CXD8/CXD-ROUTER/Sch/CXD-ROUTER-1.kicad_sch

## KiCad design Sch/CXD-ROUTER-1.kicad_sch (2026-08-12)

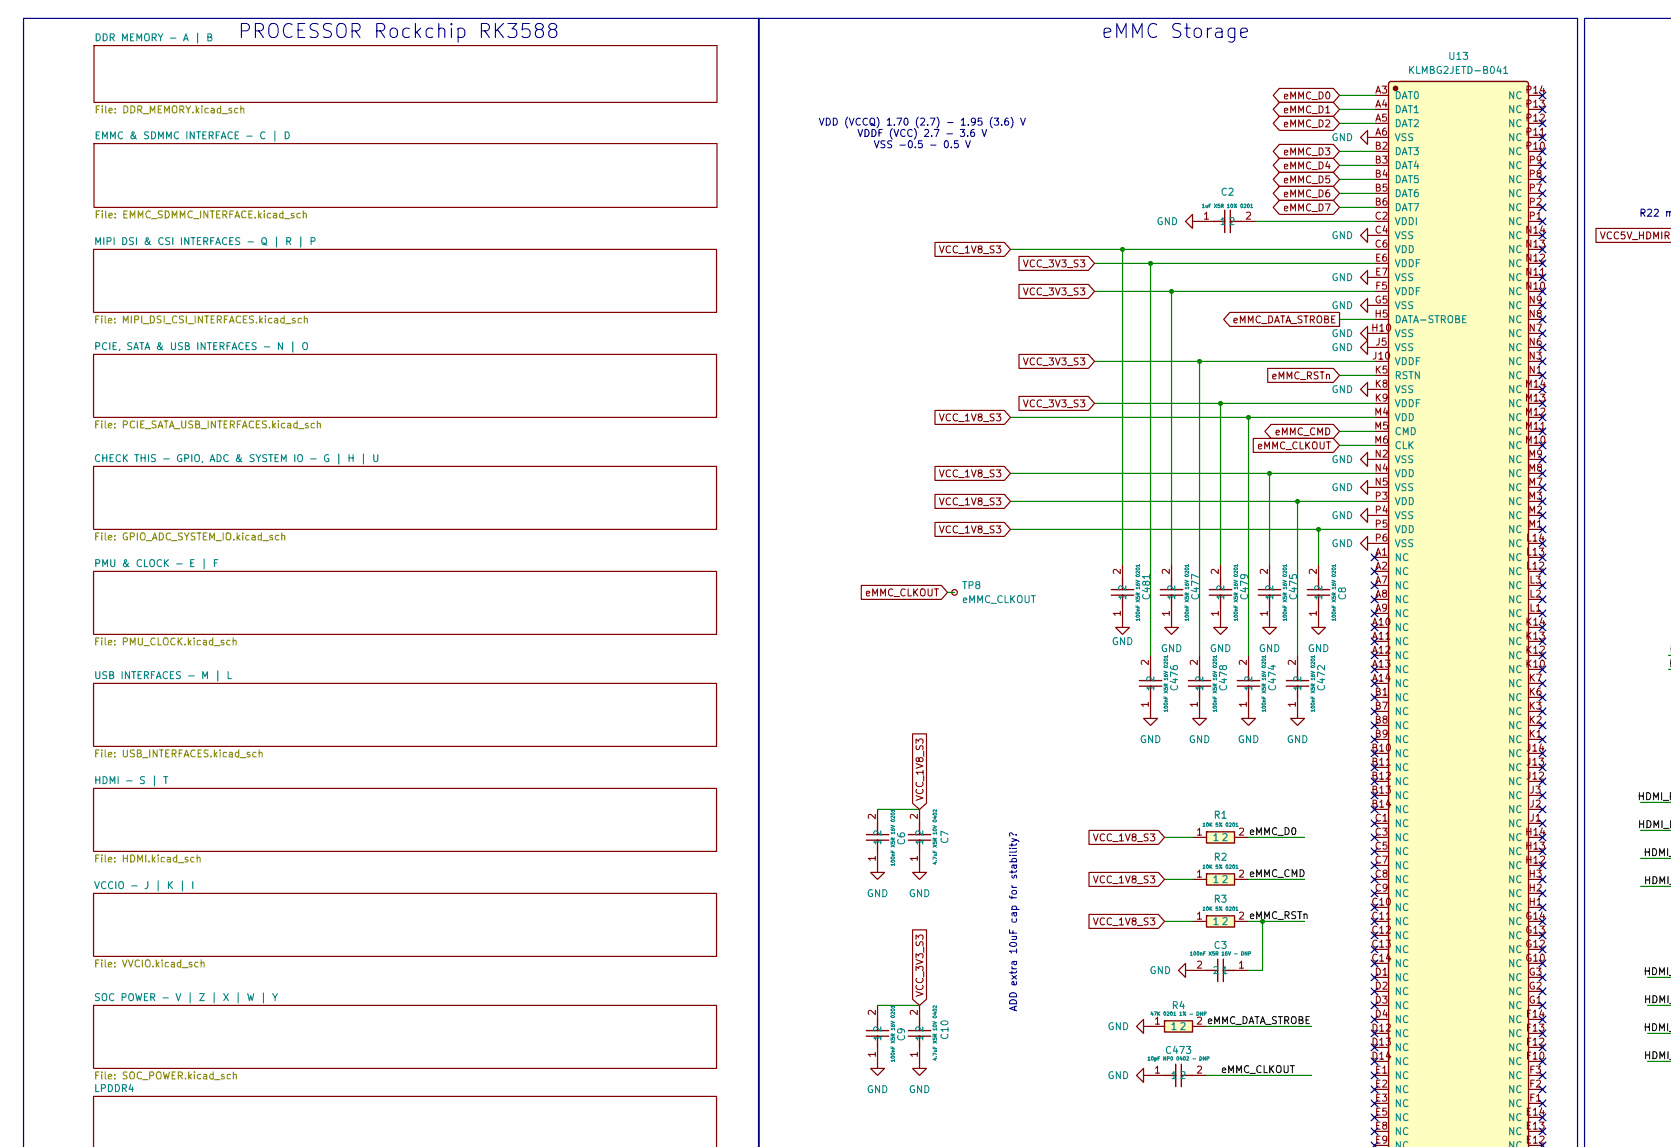
[picture p30: schematic CXD-ROUTER-1.kicad_sch, part in row 1, column 1]

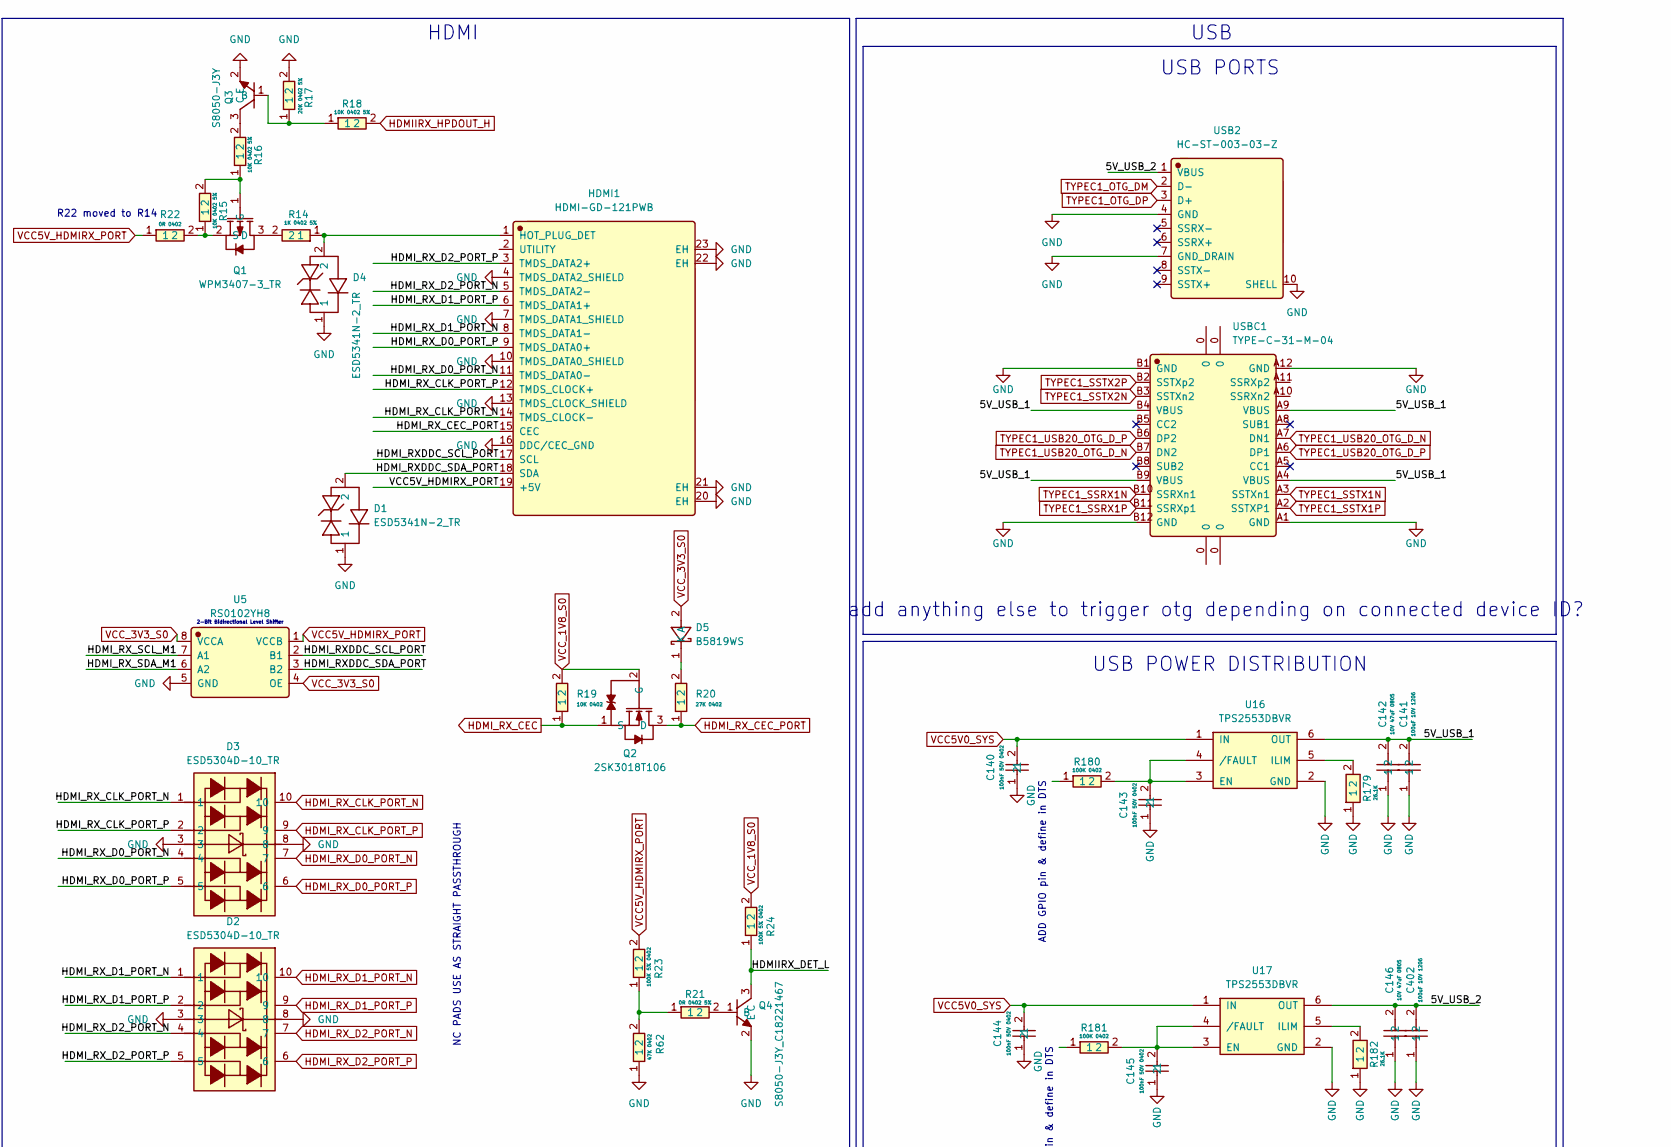
[picture p31: schematic CXD-ROUTER-1.kicad_sch, part in row 1, column 2]

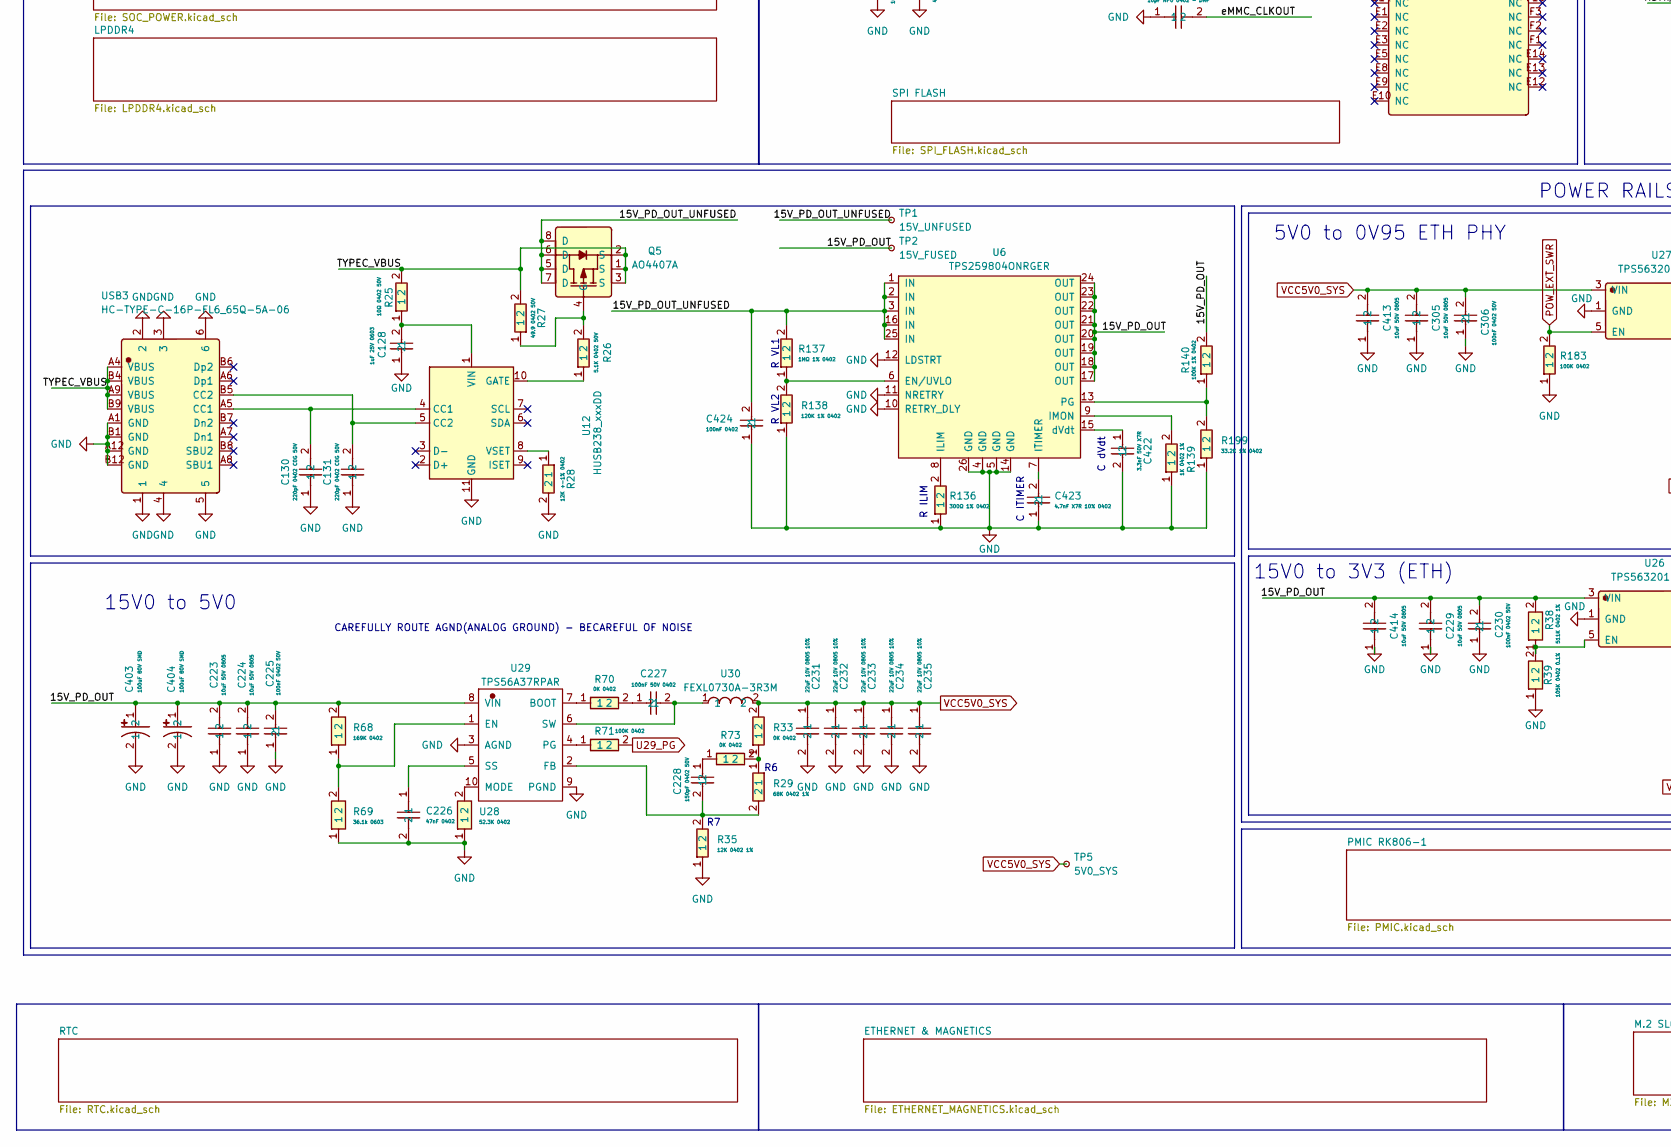
[picture p32: schematic CXD-ROUTER-1.kicad_sch, part in row 2, column 1]

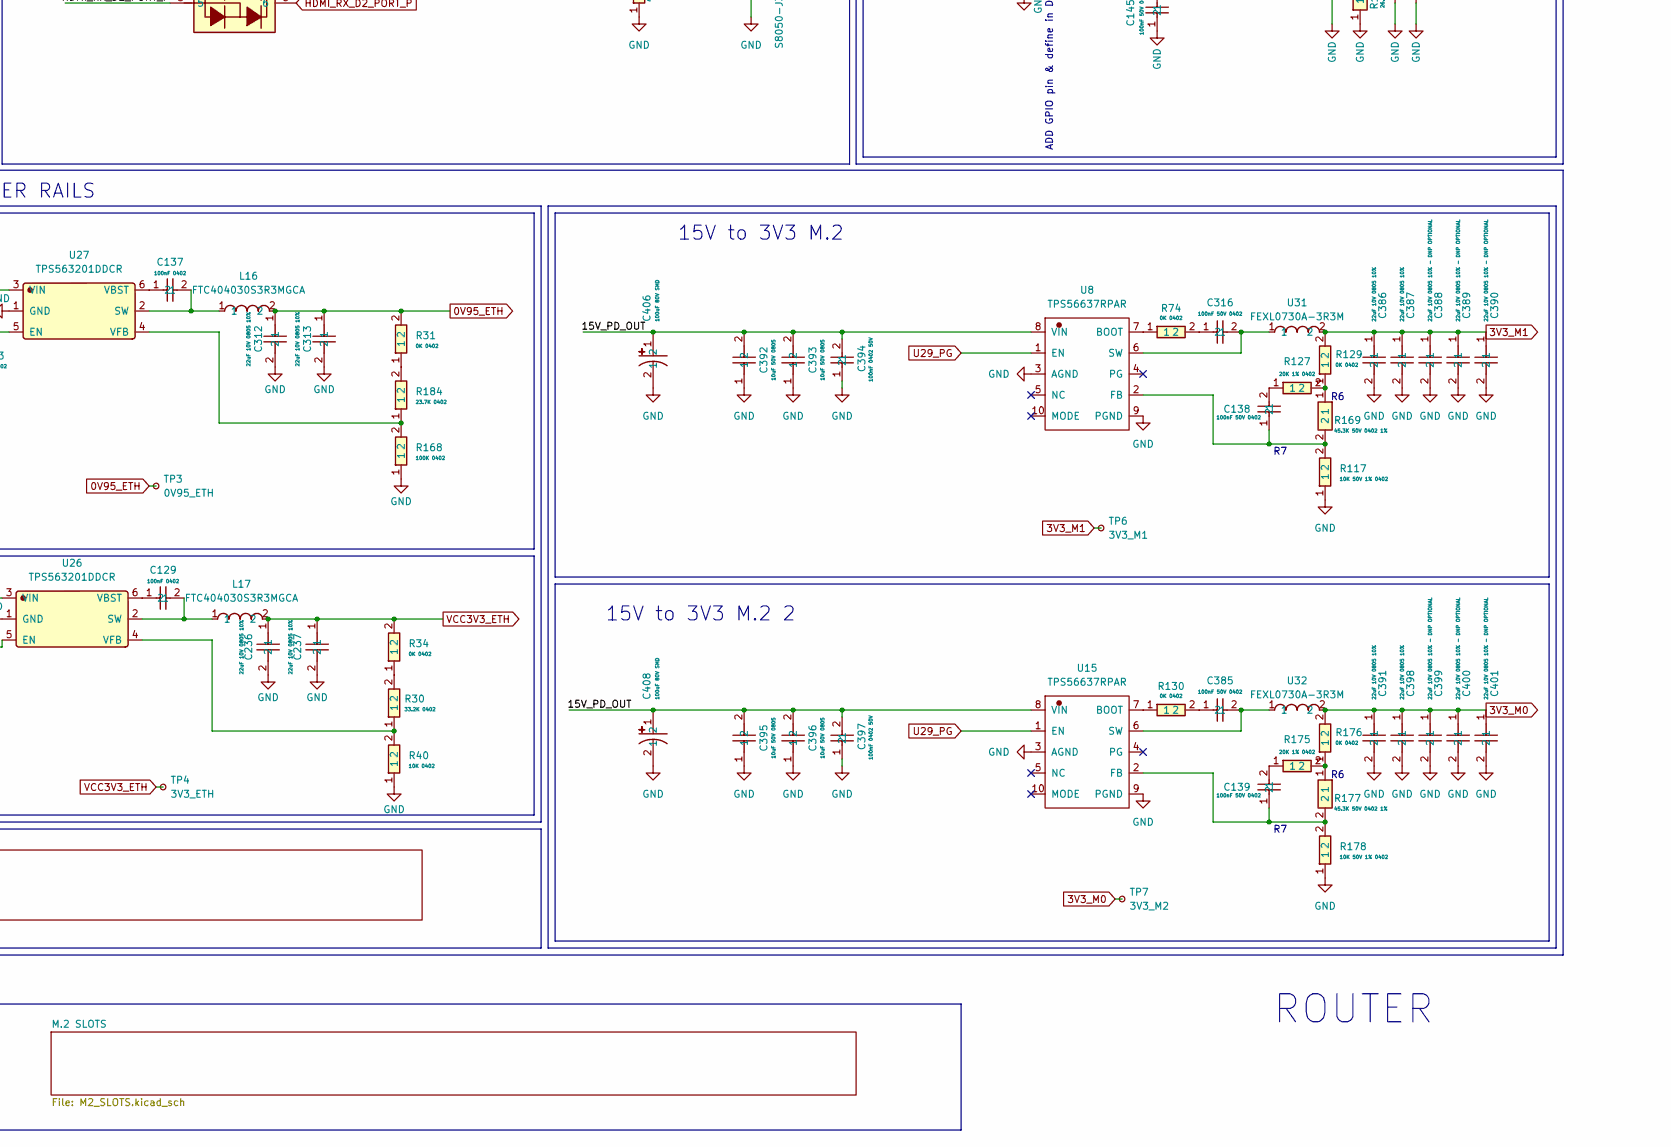
[picture p33: schematic CXD-ROUTER-1.kicad_sch, part in row 2, column 2]

Parts:
C2: 1uF X5R 10% 0201; RC0201FR-0749R9L; Manufacturer Part CC0201KRX5R5BB105; LCSC C541330
C3: 100nF X5R 16V - DNP; RC0201FR-0749R9L; Manufacturer Part CL03A104KO3NNNC; LCSC C307380
C6, C8, C9, C472, C474, C475, C476, C477, C478, C479, C481: 100nF X5R 16V 0201; RC0201FR-0749R9L; Manufacturer Part CL03A104KO3NNNC; LCSC C307380
C7, C10: 4.7uF X5R 10V 0402; RC0402JR-070RL; Manufacturer Part CL05A475KP5NRNC; LCSC C368809
C128: 1uF 25V 0603; CL10B105KA8NNNC; Manufacturer Part CL10B105KA8NNNC; LCSC C29936
C129, C137, C424: 100nF 0402; RC0402JR-070RL; Manufacturer Part CC0402KRX5R9BB104; LCSC C105882
C130, C131: 220pF 0402 C0G 50V; RC0402JR-070RL; Manufacturer Part GRM1555C1H221JA01D; LCSC C71693
C138, C139, C140, C143, C144, C145, C227, C316, C385: 100nF 50V 0402; RC0402JR-070RL; Manufacturer Part CC0402KRX5R9BB104; LCSC C105882
C141, C402: 100uF 10V 1206; GRM31CR61A107MEA8L; Manufacturer Part GRM31CR61A107MEA8L; LCSC C883598
C142, C146: 10V 47uF 0805; GRM21BR61A476ME15L; Manufacturer Part GRM21BR61A476ME15L; LCSC C124129
C223, C224, C229, C305, C392, C393, C395, C396, C413, C414: 10uF 50V 0805; GRM21BR61H106KE43L; Manufacturer Part GRM21BR61H106KE43L; LCSC C440198
C225, C230, C306, C394, C397: 100nF 0402 50V; RC0402JR-070RL; Manufacturer Part CC0402KRX5R9BB104; LCSC C105882
C226: 47nF 0402; RC0402JR-070RL; Manufacturer Part CL05B473KB5VPNC; LCSC C307339
C228: 150pF 0402 50V; RC0402JR-070RL; Manufacturer Part CC0402JRNPO9BN151; LCSC C106998
C231, C232, C233, C234, C235, C236, C237, C312, C313, C386, C387, C391, C398: 22uF 10V 0805 10%; CL21A226KPCLRNC; Manufacturer Part CL21A226KPCLRNC; LCSC C318688
C388, C389, C390, C399, C400, C401: 22uF 10V 0805 10% - DNP OPTIONAL; CL21A226KPCLRNC; Manufacturer Part CL21A226KPCLRNC; LCSC C318688
C403, C404, C406, C408: 100uF 80V SMD; VKME1001K101MV; Manufacturer Part VKME1001K101MV; LCSC C487410
C422: 3.3nF 50V X7R; RC0402FR-071KL; Manufacturer Part CC0402KRX7R9BB332; LCSC C107028
C423: 4.7nF X7R 10% 0402; RC0402FR-071KL; Manufacturer Part CC0402KRX7R9BB472; LCSC C106208
C473: 10pF NP0 0402 - DNP; FRC0402F1693TS; Manufacturer Part CC0402FRNPO9BN100; LCSC C513681
D1, D4: ESD5341N-2_TR; Manufacturer Part ESD5341N-2/TR; LCSC C239773
D2, D3: ESD5304D-10_TR; Manufacturer Part ESD5304D-10/TR; LCSC C153722
D5: B5819WS; B5819WS_C916992; Manufacturer Part B5819WS; LCSC C916992
HDMI1: HDMI-GD-121PWB; Manufacturer Part HDMI-GD-121PWB; LCSC C7425334
L16, L17: FTC404030S3R3MGCA; Manufacturer Part FTC404030S3R3MGCA; LCSC C39676082
Q1: WPM3407-3_TR; Manufacturer Part WPM3407-3/TR; LCSC C167139
Q2: 2SK3018T106; Manufacturer Part 2SK3018T106; LCSC C113315
Q3: S8050-J3Y; S8050-J3Y_C18221467; Manufacturer Part S8050-J3Y; LCSC C18221467
Q4: S8050-J3Y_C18221467; Manufacturer Part S8050-J3Y; LCSC C18221467
Q5: AO4407A; Manufacturer Part AO4407A; LCSC C16072
R1, R2, R3: 10K 5% 0201; RC0402JR-0710KL; Manufacturer Part RC0402JR-0710KL; LCSC C60489
R4: 47K 0201 1% - DNP; RC0201FR-0747KL; Manufacturer Part RC0201FR-0747KL; LCSC C138139
R14: 1K 0402 5%; RC0402JR-071KL; Manufacturer Part RC0402JR-071KL; LCSC C105637
R15, R16, R18: 10K 0402 5%; RC0402JR-0710KL; Manufacturer Part RC0402JR-0710KL; LCSC C60489
R17: 20K 0402 5%; RC0402JR-0720KL; Manufacturer Part RC0402JR-0720KL; LCSC C137902
R19, R40: 10K 0402; RC0402FR-0710KL; Manufacturer Part RC0402FR-0710KL; LCSC C60490
R20: 27K 0402; RC0402JR-0727KL; Manufacturer Part RC0402JR-0727KL; LCSC C137891
R21: 0R 0402 5%; RC0402JR-070RL; Manufacturer Part RC0402JR-070RL; LCSC C60485
R22: 0R 0402; RC0402JR-070RL; Manufacturer Part RC0402JR-070RL; LCSC C60485
R23, R24: 100K 5% 0402; RC0402JR-07100KL; Manufacturer Part RC0402JR-07100KL; LCSC C106234
R25: 10Ω 0402 50V; RC0402FR-0710RL; Manufacturer Part RC0402FR-0710RL; LCSC C138066
R26: 5.1K 0402 50V; RC0402FR-075K1L; Manufacturer Part RC0402FR-075K1L; LCSC C105872
R27: 49.9 0402 50V; RC0402FR-0749K9L; Manufacturer Part RC0402FR-0749K9L; LCSC C137969
R28: 12K +-1% 0402; 0402WGF1402TCE; Manufacturer Part 0402WGF1402TCE; LCSC C54831
R29: 68K 0402 1%; RC0402FR-0768KL; Manufacturer Part RC0402FR-0768KL; LCSC C137947
R30: 33.2K 0402; RC0402FR-0733K2L; Manufacturer Part RC0402FR-0733K2L; LCSC C130276
R31, R33, R34, R70, R73, R74, R129, R130, R176: 0K 0402; RC0402JR-070RL; Manufacturer Part RC0402JR-070RL; LCSC C60485
R35: 12K 0402 1%; RC0402FR-0712KL; Manufacturer Part RC0402FR-0712KL; LCSC C114760
R38: 511K 0402 1%; AF0402FR-07511KL; Manufacturer Part AF0402FR-07511KL; LCSC C2100703
R39: 105K 0402 0.1%; ARG02BTC1053; Manufacturer Part ARG02BTC1053; LCSC C2984407
R62: 47K 0402; RC0201FR-0747KL; Manufacturer Part RC0201FR-0747KL; LCSC C138139
R68: 169K 0402; FRC0402F1693TS; Manufacturer Part FRC0402F1693TS; LCSC C2974012
R69: 36.1k 0603; RT0603BRD0736K1L; Manufacturer Part RT0603BRD0736K1L; LCSC C861351
R71, R168, R180, R181, R183: 100K 0402; RC0402FR-07100KL; Manufacturer Part RC0402FR-07100KL; LCSC C60491
R117, R178: 10K 50V 1% 0402; RC0402FR-0710KL; Manufacturer Part RC0402FR-0710KL; LCSC C60490
R127, R175: 20K 1% 0402; RC0402FR-0720KL; Manufacturer Part RC0402FR-0720KL; LCSC C93942
R136: 300Ω 1% 0402; RC0402FR-07300RL; Manufacturer Part RC0402FR-07300RL; LCSC C138010
R137: 1MΩ 1% 0402; RC0402FR-071ML; Manufacturer Part RC0402FR-071ML; LCSC C138033
R138: 120K 1% 0402; RC0402FR-07120KL; Manufacturer Part RC0402FR-07120KL; LCSC C93945
R139: 1K 0402 1%; RC0402FR-071KL; Manufacturer Part RC0402FR-071KL; LCSC C106235
R140: 100K 1% 0402; RC0402FR-07100KL; Manufacturer Part RC0402FR-07100KL; LCSC C60491
R169, R177: 45.3K 50V 0402 1%; RT0402BRD0745K3L; Manufacturer Part RT0402BRD0745K3L; LCSC C852795
R179, R182: 26.1K; AT0402BRD0726K1L; Manufacturer Part AT0402BRD0726K1L; LCSC C850915
R184: 23.7K 0402; RT0402BRD0723K7L; Manufacturer Part RT0402BRD0723K7L; LCSC C852656
R199: 33.2K 1% 0402; RC0402FR-0733K2L; Manufacturer Part RC0402FR-0733K2L; LCSC C130276
TP1: 15V_UNFUSED; TestPoint_Pad_1.0x1.0mm
TP2: 15V_FUSED; TestPoint_Pad_1.0x1.0mm
TP3: 0V95_ETH; TestPoint_Pad_1.0x1.0mm
TP4: 3V3_ETH; TestPoint_Pad_1.0x1.0mm
TP5: 5V0_SYS; TestPoint_Pad_1.0x1.0mm
TP6: 3V3_M1; TestPoint_Pad_1.0x1.0mm
TP7: 3V3_M2; TestPoint_Pad_1.0x1.0mm
TP8: eMMC_CLKOUT; TestPoint_Pad_1.0x1.0mm
U5: RS0102YH8; Manufacturer Part RS0102YH8; LCSC C783414
U6: TPS259804ONRGER; Manufacturer Part TPS259804ONRGER; LCSC C2878936
U8, U15: TPS56637RPAR; Manufacturer Part TPS56637RPAR; LCSC C841386
U12: HUSB238_xxxDD; WDFN-10-1EP_3x3mm_P0.5mm_EP1.8x2.5mm
U13: KLMBG2JETD-B041; Manufacturer Part KLMBG2JETD-B041; LCSC C2803245
U16, U17: TPS2553DBVR; Manufacturer Part TPS2553DBVR; LCSC C55266
U26, U27: TPS563201DDCR; Manufacturer Part TPS563201DDCR; LCSC C116592
U28: 52.3K 0402; RT0402BRD0752K3L; Manufacturer Part RT0402BRD0752K3L; LCSC C852832
U29: TPS56A37RPAR; Manufacturer Part TPS56A37RPAR; LCSC C22392669
U30, U31, U32: FEXL0730A-3R3M; Manufacturer Part FEXL0730A-3R3M; LCSC C5378561
USB2: HC-ST-003-03-Z; Manufacturer Part HC-ST-003-03-Z; LCSC C2845335
USB3: HC-TYPE-C-16P-FL6_65Q-5A-06; Manufacturer Part HC-TYPE-C-16P-FL6.65Q-5A-06; LCSC C5342434
USBC1: TYPE-C-31-M-04; Manufacturer Part TYPE-C-31-M-04; LCSC C129018

Connections:
0V95_ETH: C312.1, C313.1, L16.2, R31.2, TP3.1
3V3_M0: C391.1, C398.1, C399.1, C400.1, C401.1, R176.2, TP7.1, U32.2
3V3_M1: C386.1, C387.1, C388.1, C389.1, C390.1, R129.2, TP6.1, U31.2
5V_USB_1: C141.2, C142.2, U16.6 (OUT), USBC1.A4 (VBUS), USBC1.A9 (VBUS), USBC1.B4 (VBUS), USBC1.B9 (VBUS)
5V_USB_2: C146.2, C402.2, U17.6 (OUT), USB2.1 (VBUS)
15V_PD_OUT: C223.2, C224.2, C225.2, C229.2, C230.2, C392.2, C393.2, C394.2, C395.2, C396.2, C397.2, C403.1, C404.1, C406.1, C408.1, C414.2, R38.2, R68.2, R140.2, TP2.1, U6.17 (OUT), U6.18 (OUT), U6.19 (OUT), U6.20 (OUT), U6.21 (OUT), U6.22 (OUT), U6.23 (OUT), U6.24 (OUT), U8.8 (VIN), U15.8 (VIN), U26.3 (VIN), U29.8 (VIN)
15V_PD_OUT_UNFUSED: C424.2, Q5.5 (D), Q5.6 (D), Q5.7 (D), Q5.8 (D), R137.2, TP1.1, U6.1 (IN), U6.2 (IN), U6.3 (IN), U6.16 (IN), U6.25 (IN)
GND: C2.1, C3.2, C6.1, C7.1, C8.1, C9.1, C10.1, C128.1, C130.1, C131.1, C140.1, C141.1, C142.1, C143.1, C144.1, C145.1, C146.1, C223.1, C224.1, C225.1, C226.2, C229.1, C230.1, C231.2, C232.2, C233.2, C234.2, C235.2, C236.2, C237.2, C305.1, C306.1, C312.2, C313.2, C386.2, C387.2, C388.2, C389.2, C390.2, C391.2, C392.1, C393.1, C394.1, C395.1, C396.1, C397.1, C398.2, C399.2, C400.2, C401.2, C402.1, C403.2, C404.2, C406.2, C408.2, C413.1, C414.1, C422.2, C423.1, C424.1, C472.1, C473.1, C474.1, C475.1, C476.1, C477.1, C478.1, C479.1, C481.1, D1.1, D2.3, D2.8, D3.3, D3.8, D4.1, HDMI1.4 (TMDS_DATA2_SHIELD), HDMI1.7 (TMDS_DATA1_SHIELD), HDMI1.10 (TMDS_DATA0_SHIELD), HDMI1.13 (TMDS_CLOCK_SHIELD), HDMI1.16 (DDC/CEC_GND), HDMI1.20 (EH), HDMI1.21 (EH), HDMI1.22 (EH), HDMI1.23 (EH), Q3.2 (E), Q4.2 (E), R4.1, R17.2, R28.2, R35.1, R39.1, R40.1, R62.1, R69.1, R117.1, R136.1, R138.1, R139.1, R168.1, R178.1, R179.1, R182.1, R183.1, R199.1, U5.5 (GND), U6.4 (GND), U6.5 (GND), U6.10 (RETRY_DLY), U6.11 (NRETRY), U6.12 (LDSTRT), U6.14 (GND), U6.26 (GND), U8.3 (AGND), U8.9 (PGND), U12.11 (GND), U13.A6 (VSS), U13.C4 (VSS), U13.E7 (VSS), U13.G5 (VSS), U13.H10 (VSS), U13.J5 (VSS), U13.K8 (VSS), U13.N2 (VSS), U13.N5 (VSS), U13.P4 (VSS), U13.P6 (VSS), U15.3 (AGND), U15.9 (PGND), U16.2 (GND), U17.2 (GND), U26.1 (GND), U27.1 (GND), U28.1, U29.3 (AGND), U29.9 (PGND), USB2.4 (GND), USB2.7 (GND_DRAIN), USB2.10 (SHELL), USB3.1, USB3.2, USB3.3, USB3.4, USB3.5, USB3.6, USB3.A1 (GND), USB3.A12 (GND), USB3.B1 (GND), USB3.B12 (GND), USBC1.A1 (GND), USBC1.A12 (GND), USBC1.B1 (GND), USBC1.B12 (GND)
HDMIIRX_DET_L: Q4.3 (C), R24.1
HDMIIRX_HPDOUT_H: R18.2
HDMI_RXDDC_SCL_PORT: HDMI1.17 (SCL), U5.2 (B1)
HDMI_RXDDC_SDA_PORT: D1.2, HDMI1.18 (SDA), U5.3 (B2)
HDMI_RX_CEC: Q2.1 (S), R19.1
HDMI_RX_CEC_PORT: HDMI1.15 (CEC), Q2.3 (D), R20.1
HDMI_RX_CLK_PORT_N: D3.1, D3.10, HDMI1.14 (TMDS_CLOCK-)
HDMI_RX_CLK_PORT_P: D3.2, D3.9, HDMI1.12 (TMDS_CLOCK+)
HDMI_RX_D0_PORT_N: D3.4, D3.7, HDMI1.11 (TMDS_DATA0-)
HDMI_RX_D0_PORT_P: D3.5, D3.6, HDMI1.9 (TMDS_DATA0+)
HDMI_RX_D1_PORT_N: D2.1, D2.10, HDMI1.8 (TMDS_DATA1-)
HDMI_RX_D1_PORT_P: D2.2, D2.9, HDMI1.6 (TMDS_DATA1+)
HDMI_RX_D2_PORT_N: D2.4, D2.7, HDMI1.5 (TMDS_DATA2-)
HDMI_RX_D2_PORT_P: D2.5, D2.6, HDMI1.3 (TMDS_DATA2+)
HDMI_RX_SCL_M1: U5.7 (A1)
HDMI_RX_SDA_M1: U5.6 (A2)
unnamed: C2.2, U13.C2 (VDDI)
unnamed: C128.2, R25.1, U12.1 (VIN)
unnamed: C129.1, U26.6 (VBST)
unnamed: C129.2, L17.1, U26.2 (SW)
unnamed: C130.2, U12.4 (CC1), USB3.A5 (CC1)
unnamed: C131.2, U12.5 (CC2), USB3.B5 (CC2)
unnamed: C137.1, U27.6 (VBST)
unnamed: C137.2, L16.1, U27.2 (SW)
unnamed: C138.1, R117.2, R169.2, U8.2 (FB)
unnamed: C138.2, R127.1
unnamed: C139.1, R177.2, R178.2, U15.2 (FB)
unnamed: C139.2, R175.1
unnamed: C143.2, R180.2, U16.3 (EN), U16.4 (/FAULT)
unnamed: C145.2, R181.2, U17.3 (EN), U17.4 (/FAULT)
unnamed: C226.1, U29.5 (SS)
unnamed: C227.1, R70.2
unnamed: C227.2, U29.6 (SW), U30.1
unnamed: C228.1, R73.1
unnamed: C228.2, R29.2, R35.2, U29.2 (FB)
unnamed: C316.1, R74.2
unnamed: C316.2, U8.6 (SW), U31.1
unnamed: C385.1, R130.2
unnamed: C385.2, U15.6 (SW), U32.1
unnamed: C422.1, U6.15 (dVdt)
unnamed: C423.2, U6.7 (ITIMER)
unnamed: D4.2, R14.1
unnamed: D5.1 (K), R20.2
unnamed: Q1.1 (G), R15.2, R16.1
unnamed: Q1.2 (S), R15.1, R22.2
unnamed: Q1.3 (D), R14.2
unnamed: Q3.1 (B), R17.1, R18.1
unnamed: Q3.3 (C), R16.2
unnamed: Q4.1 (B), R21.2
unnamed: Q5.4 (G), R26.2, R27.1
unnamed: R21.1, R23.1, R62.2
unnamed: R26.1, U12.10 (GATE)
unnamed: R28.1, U12.8 (VSET)
unnamed: R29.1, R33.1, R73.2
unnamed: R30.1, R40.2, U26.4 (VFB)
unnamed: R30.2, R34.1
unnamed: R38.1, R39.2, U26.5 (EN)
unnamed: R68.1, R69.2, U29.1 (EN)
unnamed: R70.1, U29.7 (BOOT)
unnamed: R71.1, U29.4 (PG)
unnamed: R74.1, U8.7 (BOOT)
unnamed: R127.2, R129.1, R169.1
unnamed: R130.1, U15.7 (BOOT)
unnamed: R136.2, U6.8 (ILIM)
unnamed: R137.1, R138.2, U6.6 (EN/UVLO)
unnamed: R139.2, U6.9 (IMON)
unnamed: R140.1, R199.2, U6.13 (PG)
unnamed: R168.2, R184.1, U27.4 (VFB)
unnamed: R175.2, R176.1, R177.1
unnamed: R179.2, U16.5 (ILIM)
unnamed: R182.2, U17.5 (ILIM)
unnamed: R31.1, R184.2
unnamed: U28.2, U29.10 (MODE)
POW_EXT_SWR: R183.2, U27.5 (EN)
TYPEC1_OTG_DM: USB2.2 (D-)
TYPEC1_OTG_DP: USB2.3 (D+)
TYPEC1_SSRX1N: USBC1.B10 (SSRXn1)
TYPEC1_SSRX1P: USBC1.B11 (SSRXp1)
TYPEC1_SSTX1N: USBC1.A3 (SSTXn1)
TYPEC1_SSTX1P: USBC1.A2 (SSTXP1)
TYPEC1_SSTX2N: USBC1.B3 (SSTXn2)
TYPEC1_SSTX2P: USBC1.B2 (SSTXp2)
TYPEC1_USB20_OTG_D_N: USBC1.A7 (DN1), USBC1.B7 (DN2)
TYPEC1_USB20_OTG_D_P: USBC1.A6 (DP1), USBC1.B6 (DP2)
TYPEC_VBUS: Q5.1 (S), Q5.2 (S), Q5.3 (S), R25.2, R27.2, USB3.A4 (VBUS), USB3.A9 (VBUS), USB3.B4 (VBUS), USB3.B9 (VBUS)
U29_PG: R71.2, U8.1 (EN), U15.1 (EN)
VCC3V3_ETH: C236.1, C237.1, L17.2, R34.2, TP4.1
VCC5V0_SYS: C140.2, C144.2, C231.1, C232.1, C233.1, C234.1, C235.1, C305.2, C306.2, C413.2, R33.2, TP5.1, U16.1 (IN), U17.1 (IN), U27.3 (VIN), U30.2
VCC5V_HDMIRX_PORT: HDMI1.19 (+5V), R22.1, R23.2, U5.1 (VCCB)
VCC_1V8_S0: Q2.2 (G), R19.2, R24.2
VCC_1V8_S3: C6.2, C7.2, C8.2, C472.2, C474.2, C475.2, C481.2, R1.1, R2.1, R3.1, U13.C6 (VDD), U13.M4 (VDD), U13.N4 (VDD), U13.P3 (VDD), U13.P5 (VDD)
VCC_3V3_S0: D5.2 (A), U5.4 (OE), U5.8 (VCCA)
VCC_3V3_S3: C9.2, C10.2, C476.2, C477.2, C478.2, C479.2, U13.E6 (VDDF), U13.F5 (VDDF), U13.J10 (VDDF), U13.K9 (VDDF)
eMMC_CLKOUT: C473.2, TP8.1, U13.M6 (CLK)
eMMC_CMD: R2.2, U13.M5 (CMD)
eMMC_D0: R1.2, U13.A3 (DAT0)
eMMC_D1: U13.A4 (DAT1)
eMMC_D2: U13.A5 (DAT2)
eMMC_D3: U13.B2 (DAT3)
eMMC_D4: U13.B3 (DAT4)
eMMC_D5: U13.B4 (DAT5)
eMMC_D6: U13.B5 (DAT6)
eMMC_D7: U13.B6 (DAT7)
eMMC_DATA_STROBE: R4.2, U13.H5 (DATA-STROBE)
eMMC_RSTn: C3.1, R3.2, U13.K5 (RSTN)

Notes on the sheet:
C ITIMER
add anything else to trigger otg depending on connected device ID?
eMMC Storage
R22 moved to R14
ADD extra 10uF cap for stability?
5V0 to 0V95 ETH PHY
NC PADS USE AS STRAIGHT PASSTHROUGH
VDD (VCCQ) 1.70 (2.7) - 1.95 (3.6) V VDDF (VCC) 2.7 - 3.6 V VSS -0.5 - 0.5 V
ROUTER
R VL1
C dVdt  
USB POWER DISTRIBUTION
USB
15V0 to 5V0
POWER RAILS
R VL2
R ILIM
HDMI
CAREFULLY ROUTE AGND(ANALOG GROUND) - BECAREFUL OF NOISE
15V to 3V3 M.2
PROCESSOR Rockchip RK3588
USB PORTS
15V0 to 3V3 (ETH)
2-Bit Bidirectional Level Shifter
ADD GPIO pin & define in DTS
15V to 3V3 M.2 2
