CXD8/CXD-ROUTER/Sch/DDR_MEMORY-2.kicad_sch

## KiCad design Sch/DDR_MEMORY-2.kicad_sch (2026-08-12)

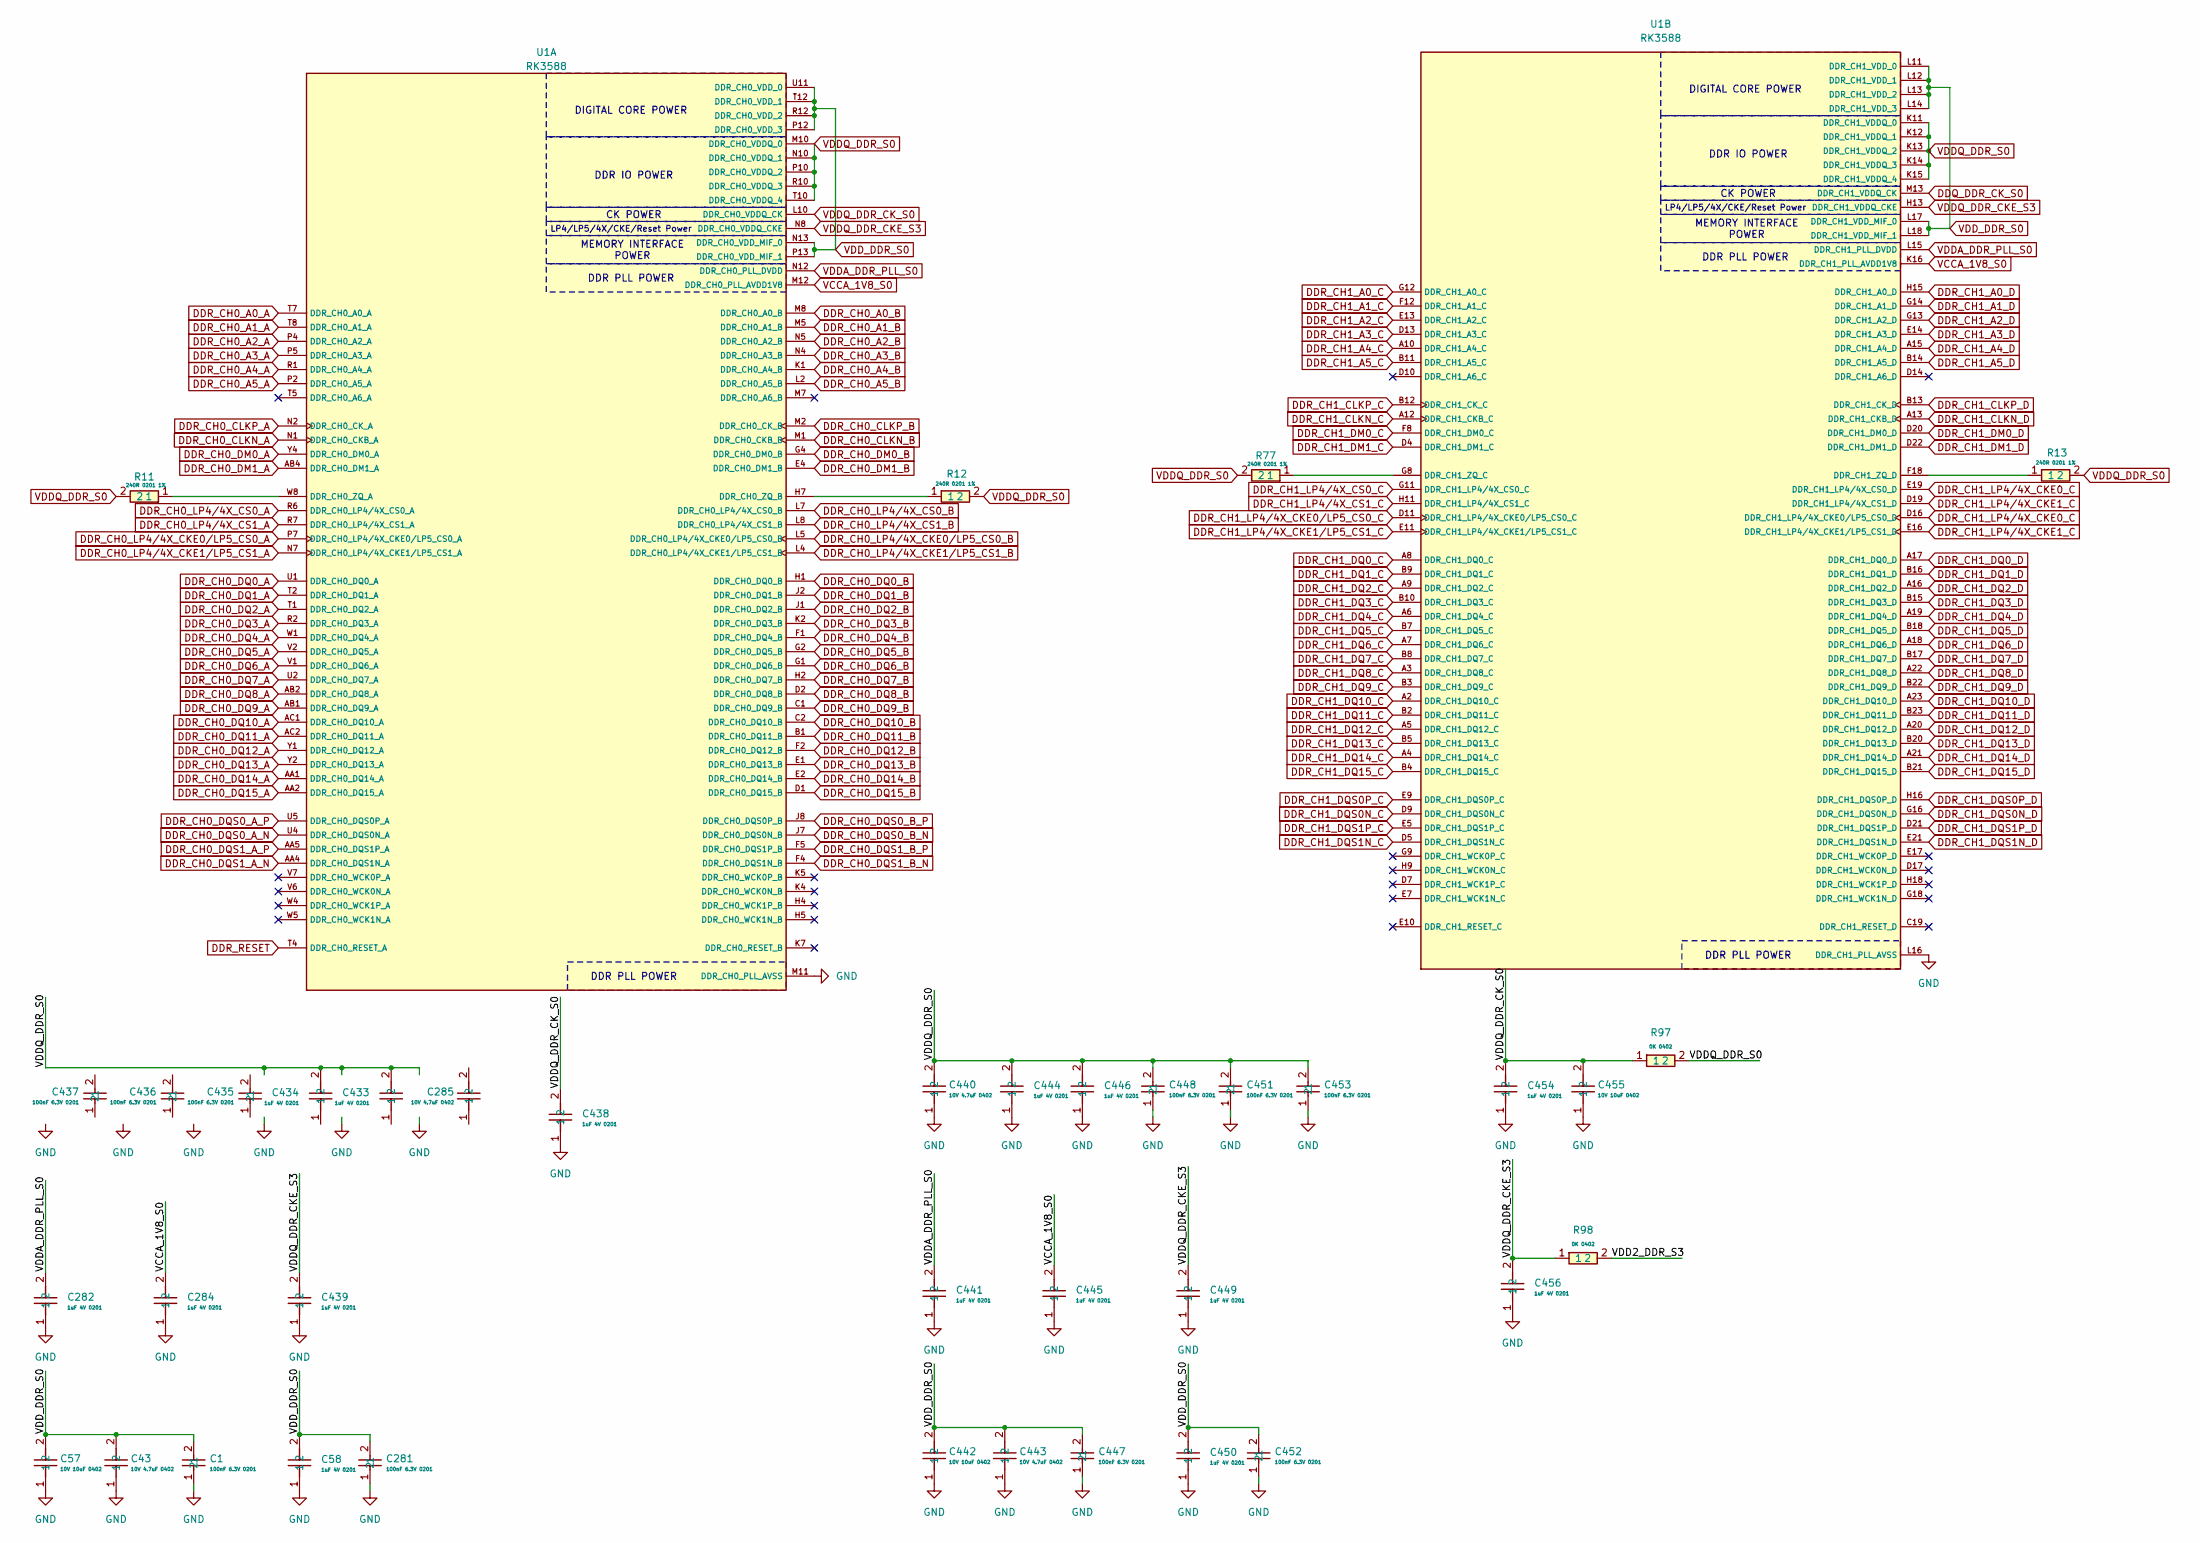
[picture p34: schematic DDR_MEMORY-2.kicad_sch]

Parts:
C1, C281, C435, C436, C437, C447, C448, C451, C452, C453: 100nF 6.3V 0201; RC0201FR-0749R9L; Manufacturer Part CC0201KRX5R5BB104; LCSC C190187
C43, C285, C440, C443: 10V 4.7uF 0402; FRC0402F1693TS; Manufacturer Part CC0402MRX5R6BB475; LCSC C469468
C57, C442, C455: 10V 10uF 0402; 10uF_X5R_10V_0402; Manufacturer Part CL05A106MP5NUNC; LCSC C315248
C58, C282, C284, C433, C434, C438, C439, C441, C444, C445, C446, C449, C450, C454, C456: 1uF 4V 0201; RC0201FR-0749R9L; Manufacturer Part GRM033C80G105MEA2D; LCSC C161455
R11, R12, R13, R77: 240R 0201 1%; RC0201FR-07240RL; Manufacturer Part RC0201FR-07240RL; LCSC C155745
R97, R98: 0K 0402; RC0402JR-070RL; Manufacturer Part RC0402JR-070RL; LCSC C60485
U1: RK3588; BGA1088C65P34X34_2300X2300X204N; PARTREV 1.0

Connections:
DDQ_DDR_CK_S0: U1.M13 (DDR_CH1_VDDQ_CK)
DDR_CH0_A0_A: U1.T7 (DDR_CH0_A0_A)
DDR_CH0_A0_B: U1.M8 (DDR_CH0_A0_B)
DDR_CH0_A1_A: U1.T8 (DDR_CH0_A1_A)
DDR_CH0_A1_B: U1.M5 (DDR_CH0_A1_B)
DDR_CH0_A2_A: U1.P4 (DDR_CH0_A2_A)
DDR_CH0_A2_B: U1.N5 (DDR_CH0_A2_B)
DDR_CH0_A3_A: U1.P5 (DDR_CH0_A3_A)
DDR_CH0_A3_B: U1.N4 (DDR_CH0_A3_B)
DDR_CH0_A4_A: U1.R1 (DDR_CH0_A4_A)
DDR_CH0_A4_B: U1.K1 (DDR_CH0_A4_B)
DDR_CH0_A5_A: U1.P2 (DDR_CH0_A5_A)
DDR_CH0_A5_B: U1.L2 (DDR_CH0_A5_B)
DDR_CH0_CLKN_A: U1.N1 (DDR_CH0_CKB_A)
DDR_CH0_CLKN_B: U1.M1 (DDR_CH0_CKB_B)
DDR_CH0_CLKP_A: U1.N2 (DDR_CH0_CK_A)
DDR_CH0_CLKP_B: U1.M2 (DDR_CH0_CK_B)
DDR_CH0_DM0_A: U1.Y4 (DDR_CH0_DM0_A)
DDR_CH0_DM0_B: U1.G4 (DDR_CH0_DM0_B)
DDR_CH0_DM1_A: U1.AB4 (DDR_CH0_DM1_A)
DDR_CH0_DM1_B: U1.E4 (DDR_CH0_DM1_B)
DDR_CH0_DQ0_A: U1.U1 (DDR_CH0_DQ0_A)
DDR_CH0_DQ0_B: U1.H1 (DDR_CH0_DQ0_B)
DDR_CH0_DQ1_A: U1.T2 (DDR_CH0_DQ1_A)
DDR_CH0_DQ1_B: U1.J2 (DDR_CH0_DQ1_B)
DDR_CH0_DQ2_A: U1.T1 (DDR_CH0_DQ2_A)
DDR_CH0_DQ2_B: U1.J1 (DDR_CH0_DQ2_B)
DDR_CH0_DQ3_A: U1.R2 (DDR_CH0_DQ3_A)
DDR_CH0_DQ3_B: U1.K2 (DDR_CH0_DQ3_B)
DDR_CH0_DQ4_A: U1.W1 (DDR_CH0_DQ4_A)
DDR_CH0_DQ4_B: U1.F1 (DDR_CH0_DQ4_B)
DDR_CH0_DQ5_A: U1.V2 (DDR_CH0_DQ5_A)
DDR_CH0_DQ5_B: U1.G2 (DDR_CH0_DQ5_B)
DDR_CH0_DQ6_A: U1.V1 (DDR_CH0_DQ6_A)
DDR_CH0_DQ6_B: U1.G1 (DDR_CH0_DQ6_B)
DDR_CH0_DQ7_A: U1.U2 (DDR_CH0_DQ7_A)
DDR_CH0_DQ7_B: U1.H2 (DDR_CH0_DQ7_B)
DDR_CH0_DQ8_A: U1.AB2 (DDR_CH0_DQ8_A)
DDR_CH0_DQ8_B: U1.D2 (DDR_CH0_DQ8_B)
DDR_CH0_DQ9_A: U1.AB1 (DDR_CH0_DQ9_A)
DDR_CH0_DQ9_B: U1.C1 (DDR_CH0_DQ9_B)
DDR_CH0_DQ10_A: U1.AC1 (DDR_CH0_DQ10_A)
DDR_CH0_DQ10_B: U1.C2 (DDR_CH0_DQ10_B)
DDR_CH0_DQ11_A: U1.AC2 (DDR_CH0_DQ11_A)
DDR_CH0_DQ11_B: U1.B1 (DDR_CH0_DQ11_B)
DDR_CH0_DQ12_A: U1.Y1 (DDR_CH0_DQ12_A)
DDR_CH0_DQ12_B: U1.F2 (DDR_CH0_DQ12_B)
DDR_CH0_DQ13_A: U1.Y2 (DDR_CH0_DQ13_A)
DDR_CH0_DQ13_B: U1.E1 (DDR_CH0_DQ13_B)
DDR_CH0_DQ14_A: U1.AA1 (DDR_CH0_DQ14_A)
DDR_CH0_DQ14_B: U1.E2 (DDR_CH0_DQ14_B)
DDR_CH0_DQ15_A: U1.AA2 (DDR_CH0_DQ15_A)
DDR_CH0_DQ15_B: U1.D1 (DDR_CH0_DQ15_B)
DDR_CH0_DQS0_A_N: U1.U4 (DDR_CH0_DQS0N_A)
DDR_CH0_DQS0_A_P: U1.U5 (DDR_CH0_DQS0P_A)
DDR_CH0_DQS0_B_N: U1.J7 (DDR_CH0_DQS0N_B)
DDR_CH0_DQS0_B_P: U1.J8 (DDR_CH0_DQS0P_B)
DDR_CH0_DQS1_A_N: U1.AA4 (DDR_CH0_DQS1N_A)
DDR_CH0_DQS1_A_P: U1.AA5 (DDR_CH0_DQS1P_A)
DDR_CH0_DQS1_B_N: U1.F4 (DDR_CH0_DQS1N_B)
DDR_CH0_DQS1_B_P: U1.F5 (DDR_CH0_DQS1P_B)
DDR_CH0_LP4/4X_CKE0/LP5_CS0_A: U1.P7 (DDR_CH0_LP4/4X_CKE0/LP5_CS0_A)
DDR_CH0_LP4/4X_CKE0/LP5_CS0_B: U1.L5 (DDR_CH0_LP4/4X_CKE0/LP5_CS0_B)
DDR_CH0_LP4/4X_CKE1/LP5_CS1_A: U1.N7 (DDR_CH0_LP4/4X_CKE1/LP5_CS1_A)
DDR_CH0_LP4/4X_CKE1/LP5_CS1_B: U1.L4 (DDR_CH0_LP4/4X_CKE1/LP5_CS1_B)
DDR_CH0_LP4/4X_CS0_A: U1.R6 (DDR_CH0_LP4/4X_CS0_A)
DDR_CH0_LP4/4X_CS0_B: U1.L7 (DDR_CH0_LP4/4X_CS0_B)
DDR_CH0_LP4/4X_CS1_A: U1.R7 (DDR_CH0_LP4/4X_CS1_A)
DDR_CH0_LP4/4X_CS1_B: U1.L8 (DDR_CH0_LP4/4X_CS1_B)
DDR_CH1_A0_C: U1.G12 (DDR_CH1_A0_C)
DDR_CH1_A0_D: U1.H15 (DDR_CH1_A0_D)
DDR_CH1_A1_C: U1.F12 (DDR_CH1_A1_C)
DDR_CH1_A1_D: U1.G14 (DDR_CH1_A1_D)
DDR_CH1_A2_C: U1.E13 (DDR_CH1_A2_C)
DDR_CH1_A2_D: U1.G13 (DDR_CH1_A2_D)
DDR_CH1_A3_C: U1.D13 (DDR_CH1_A3_C)
DDR_CH1_A3_D: U1.E14 (DDR_CH1_A3_D)
DDR_CH1_A4_C: U1.A10 (DDR_CH1_A4_C)
DDR_CH1_A4_D: U1.A15 (DDR_CH1_A4_D)
DDR_CH1_A5_C: U1.B11 (DDR_CH1_A5_C)
DDR_CH1_A5_D: U1.B14 (DDR_CH1_A5_D)
DDR_CH1_CLKN_C: U1.A12 (DDR_CH1_CKB_C)
DDR_CH1_CLKN_D: U1.A13 (DDR_CH1_CKB_D)
DDR_CH1_CLKP_C: U1.B12 (DDR_CH1_CK_C)
DDR_CH1_CLKP_D: U1.B13 (DDR_CH1_CK_D)
DDR_CH1_DM0_C: U1.F8 (DDR_CH1_DM0_C)
DDR_CH1_DM0_D: U1.D20 (DDR_CH1_DM0_D)
DDR_CH1_DM1_C: U1.D4 (DDR_CH1_DM1_C)
DDR_CH1_DM1_D: U1.D22 (DDR_CH1_DM1_D)
DDR_CH1_DQ0_C: U1.A8 (DDR_CH1_DQ0_C)
DDR_CH1_DQ0_D: U1.A17 (DDR_CH1_DQ0_D)
DDR_CH1_DQ1_C: U1.B9 (DDR_CH1_DQ1_C)
DDR_CH1_DQ1_D: U1.B16 (DDR_CH1_DQ1_D)
DDR_CH1_DQ2_C: U1.A9 (DDR_CH1_DQ2_C)
DDR_CH1_DQ2_D: U1.A16 (DDR_CH1_DQ2_D)
DDR_CH1_DQ3_C: U1.B10 (DDR_CH1_DQ3_C)
DDR_CH1_DQ3_D: U1.B15 (DDR_CH1_DQ3_D)
DDR_CH1_DQ4_C: U1.A6 (DDR_CH1_DQ4_C)
DDR_CH1_DQ4_D: U1.A19 (DDR_CH1_DQ4_D)
DDR_CH1_DQ5_C: U1.B7 (DDR_CH1_DQ5_C)
DDR_CH1_DQ5_D: U1.B18 (DDR_CH1_DQ5_D)
DDR_CH1_DQ6_C: U1.A7 (DDR_CH1_DQ6_C)
DDR_CH1_DQ6_D: U1.A18 (DDR_CH1_DQ6_D)
DDR_CH1_DQ7_C: U1.B8 (DDR_CH1_DQ7_C)
DDR_CH1_DQ7_D: U1.B17 (DDR_CH1_DQ7_D)
DDR_CH1_DQ8_C: U1.A3 (DDR_CH1_DQ8_C)
DDR_CH1_DQ8_D: U1.A22 (DDR_CH1_DQ8_D)
DDR_CH1_DQ9_C: U1.B3 (DDR_CH1_DQ9_C)
DDR_CH1_DQ9_D: U1.B22 (DDR_CH1_DQ9_D)
DDR_CH1_DQ10_C: U1.A2 (DDR_CH1_DQ10_C)
DDR_CH1_DQ10_D: U1.A23 (DDR_CH1_DQ10_D)
DDR_CH1_DQ11_C: U1.B2 (DDR_CH1_DQ11_C)
DDR_CH1_DQ11_D: U1.B23 (DDR_CH1_DQ11_D)
DDR_CH1_DQ12_C: U1.A5 (DDR_CH1_DQ12_C)
DDR_CH1_DQ12_D: U1.A20 (DDR_CH1_DQ12_D)
DDR_CH1_DQ13_C: U1.B5 (DDR_CH1_DQ13_C)
DDR_CH1_DQ13_D: U1.B20 (DDR_CH1_DQ13_D)
DDR_CH1_DQ14_C: U1.A4 (DDR_CH1_DQ14_C)
DDR_CH1_DQ14_D: U1.A21 (DDR_CH1_DQ14_D)
DDR_CH1_DQ15_C: U1.B4 (DDR_CH1_DQ15_C)
DDR_CH1_DQ15_D: U1.B21 (DDR_CH1_DQ15_D)
DDR_CH1_DQS0N_C: U1.D9 (DDR_CH1_DQS0N_C)
DDR_CH1_DQS0N_D: U1.G16 (DDR_CH1_DQS0N_D)
DDR_CH1_DQS0P_C: U1.E9 (DDR_CH1_DQS0P_C)
DDR_CH1_DQS0P_D: U1.H16 (DDR_CH1_DQS0P_D)
DDR_CH1_DQS1N_C: U1.D5 (DDR_CH1_DQS1N_C)
DDR_CH1_DQS1N_D: U1.E21 (DDR_CH1_DQS1N_D)
DDR_CH1_DQS1P_C: U1.E5 (DDR_CH1_DQS1P_C)
DDR_CH1_DQS1P_D: U1.D21 (DDR_CH1_DQS1P_D)
DDR_CH1_LP4/4X_CKE0_C: U1.D16 (DDR_CH1_LP4/4X_CKE0/LP5_CS0_D), U1.E19 (DDR_CH1_LP4/4X_CS0_D)
DDR_CH1_LP4/4X_CKE0/LP5_CS0_C: U1.D11 (DDR_CH1_LP4/4X_CKE0/LP5_CS0_C)
DDR_CH1_LP4/4X_CKE1_C: U1.D19 (DDR_CH1_LP4/4X_CS1_D), U1.E16 (DDR_CH1_LP4/4X_CKE1/LP5_CS1_D)
DDR_CH1_LP4/4X_CKE1/LP5_CS1_C: U1.E11 (DDR_CH1_LP4/4X_CKE1/LP5_CS1_C)
DDR_CH1_LP4/4X_CS0_C: U1.G11 (DDR_CH1_LP4/4X_CS0_C)
DDR_CH1_LP4/4X_CS1_C: U1.H11 (DDR_CH1_LP4/4X_CS1_C)
DDR_RESET: U1.T4 (DDR_CH0_RESET_A)
GND: C1.1, C43.1, C57.1, C58.1, C281.1, C282.1, C284.1, C438.1, C439.1, C440.1, C441.1, C442.1, C443.1, C444.1, C445.1, C446.1, C447.1, C448.1, C449.1, C450.1, C451.1, C452.1, C453.1, C454.1, C455.1, C456.1, U1.L16 (DDR_CH1_PLL_AVSS), U1.M11 (DDR_CH0_PLL_AVSS)
unnamed: R11.1, U1.W8 (DDR_CH0_ZQ_A)
unnamed: R12.1, U1.H7 (DDR_CH0_ZQ_B)
unnamed: R13.1, U1.F18 (DDR_CH1_ZQ_D)
unnamed: R77.1, U1.G8 (DDR_CH1_ZQ_C)
VCCA_1V8_S0: C284.2, C445.2, U1.K16 (DDR_CH1_PLL_AVDD1V8), U1.M12 (DDR_CH0_PLL_AVDD1V8)
VDD2_DDR_S3: R98.2
VDDA_DDR_PLL_S0: C282.2, C441.2, U1.L15 (DDR_CH1_PLL_DVDD), U1.N12 (DDR_CH0_PLL_DVDD)
VDDQ_DDR_CKE_S3: C439.2, C449.2, C456.2, R98.1, U1.H13 (DDR_CH1_VDDQ_CKE), U1.N8 (DDR_CH0_VDDQ_CKE)
VDDQ_DDR_CK_S0: C438.2, C454.2, C455.2, R97.1, U1.L10 (DDR_CH0_VDDQ_CK)
VDDQ_DDR_S0: C433.2, C434.2, C440.2, C444.2, C446.2, C448.2, C451.2, C453.2, R11.2, R12.2, R13.2, R77.2, R97.2, U1.K11 (DDR_CH1_VDDQ_0), U1.K12 (DDR_CH1_VDDQ_1), U1.K13 (DDR_CH1_VDDQ_2), U1.K14 (DDR_CH1_VDDQ_3), U1.K15 (DDR_CH1_VDDQ_4), U1.M10 (DDR_CH0_VDDQ_0), U1.N10 (DDR_CH0_VDDQ_1), U1.P10 (DDR_CH0_VDDQ_2), U1.R10 (DDR_CH0_VDDQ_3), U1.T10 (DDR_CH0_VDDQ_4)
VDD_DDR_S0: C1.2, C43.2, C57.2, C58.2, C281.2, C442.2, C443.2, C447.2, C450.2, C452.2, U1.L11 (DDR_CH1_VDD_0), U1.L12 (DDR_CH1_VDD_1), U1.L13 (DDR_CH1_VDD_2), U1.L14 (DDR_CH1_VDD_3), U1.L17 (DDR_CH1_VDD_MIF_0), U1.L18 (DDR_CH1_VDD_MIF_1), U1.N13 (DDR_CH0_VDD_MIF_0), U1.P12 (DDR_CH0_VDD_3), U1.P13 (DDR_CH0_VDD_MIF_1), U1.R12 (DDR_CH0_VDD_2), U1.T12 (DDR_CH0_VDD_1), U1.U11 (DDR_CH0_VDD_0)

Notes on the sheet:
DIGITAL CORE POWER
DDR PLL POWER
LP4/LP5/4X/CKE/Reset Power
DDR IO POWER
MEMORY INTERFACE POWER
CK POWER
