CXD8/CXD-ROUTER/Sch/EMMC_SDMMC_INTERFACE-3.kicad_sch

## KiCad design Sch/EMMC_SDMMC_INTERFACE-3.kicad_sch (2026-08-12)

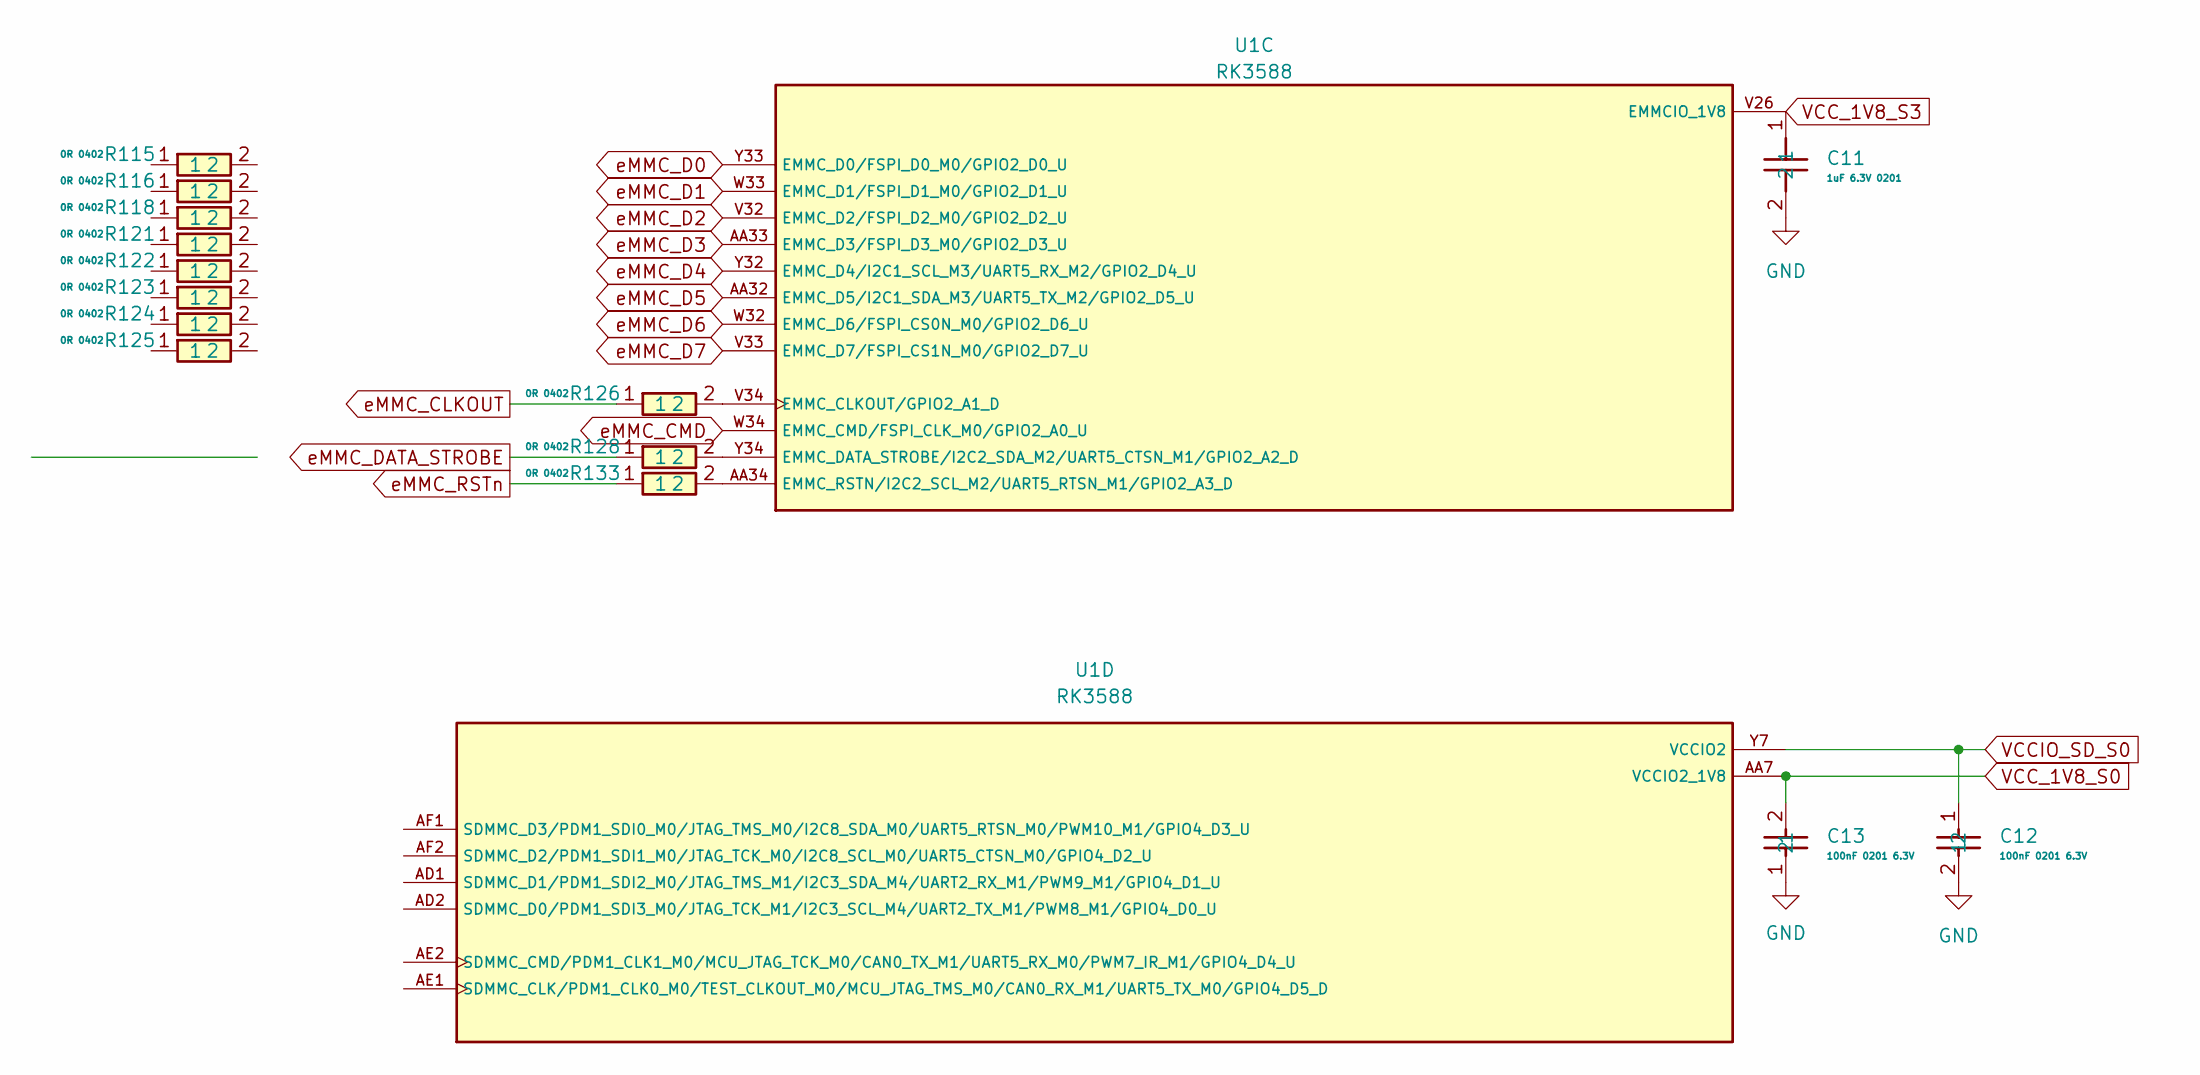
[picture p35: schematic EMMC_SDMMC_INTERFACE-3.kicad_sch]

Parts:
C11: 1uF 6.3V 0201; RC0201FR-0749R9L; Manufacturer Part CC0201KRX5R5BB105; LCSC C541330
C12, C13: 100nF 0201 6.3V; RC0201FR-0749R9L; Manufacturer Part CC0201KRX5R5BB104; LCSC C190187
R115, R116, R118, R121, R122, R123, R124, R125, R126, R128, R133: 0R 0402; RC0402JR-070RL; Manufacturer Part RC0402JR-070RL; LCSC C60485
U1: RK3588; BGA1088C65P34X34_2300X2300X204N; PARTREV 1.0

Connections:
GND: C11.2, C12.2, C13.1
unnamed: R126.2, U1.V34 (EMMC_CLKOUT/GPIO2_A1_D)
unnamed: R128.2, U1.Y34 (EMMC_DATA_STROBE/I2C2_SDA_M2/UART5_CTSN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)
unnamed: R133.2, U1.AA34 (EMMC_RSTN/I2C2_SCL_M2/UART5_RTSN_M1/GPI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)
VCCIO_SD_S0: C12.1, U1.Y7 (VCCIO2)
VCC_1V8_S0: C13.2, U1.AA7 (VCCIO2_1V8)
VCC_1V8_S3: C11.1, U1.V26 (EMMCIO_1V8)
eMMC_CLKOUT: R126.1
eMMC_CMD: U1.W34 (EMMC_CMD/FSPI_CLK_M0/GPIO2_A0_U)
eMMC_D0: U1.Y33 (EMMC_D0/FSPI_D0_M0/GPIO2_D0_U)
eMMC_D1: U1.W33 (EMMC_D1/FSPI_D1_M0/GPIO2_D1_U)
eMMC_D2: U1.V32 (EMMC_D2/FSPI_D2_M0/GPIO2_D2_U)
eMMC_D3: U1.AA33 (EMMC_D3/FSPI_D3_M0/GPIO2_D3_U)
eMMC_D4: U1.Y32 (EMMC_D4/I2C1_SCL_M3/UART5_RX_M2/GPIO2_D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)
eMMC_D5: U1.AA32 (EMMC_D5/I2C1_SDA_M3/UART5_TX_M2/GPIO2_D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)
eMMC_D6: U1.W32 (EMMC_D6/FSPI_CS0N_M0/GPIO2_D6_U)
eMMC_D7: U1.V33 (EMMC_D7/FSPI_CS1N_M0/GPIO2_D7_U)
eMMC_DATA_STROBE: R128.1
eMMC_RSTn: R133.1
