CXD8/CXD-ROUTER/Sch/ETHERNET_MAGNETICS-11.kicad_sch

## KiCad design Sch/ETHERNET_MAGNETICS-11.kicad_sch (2026-08-12)

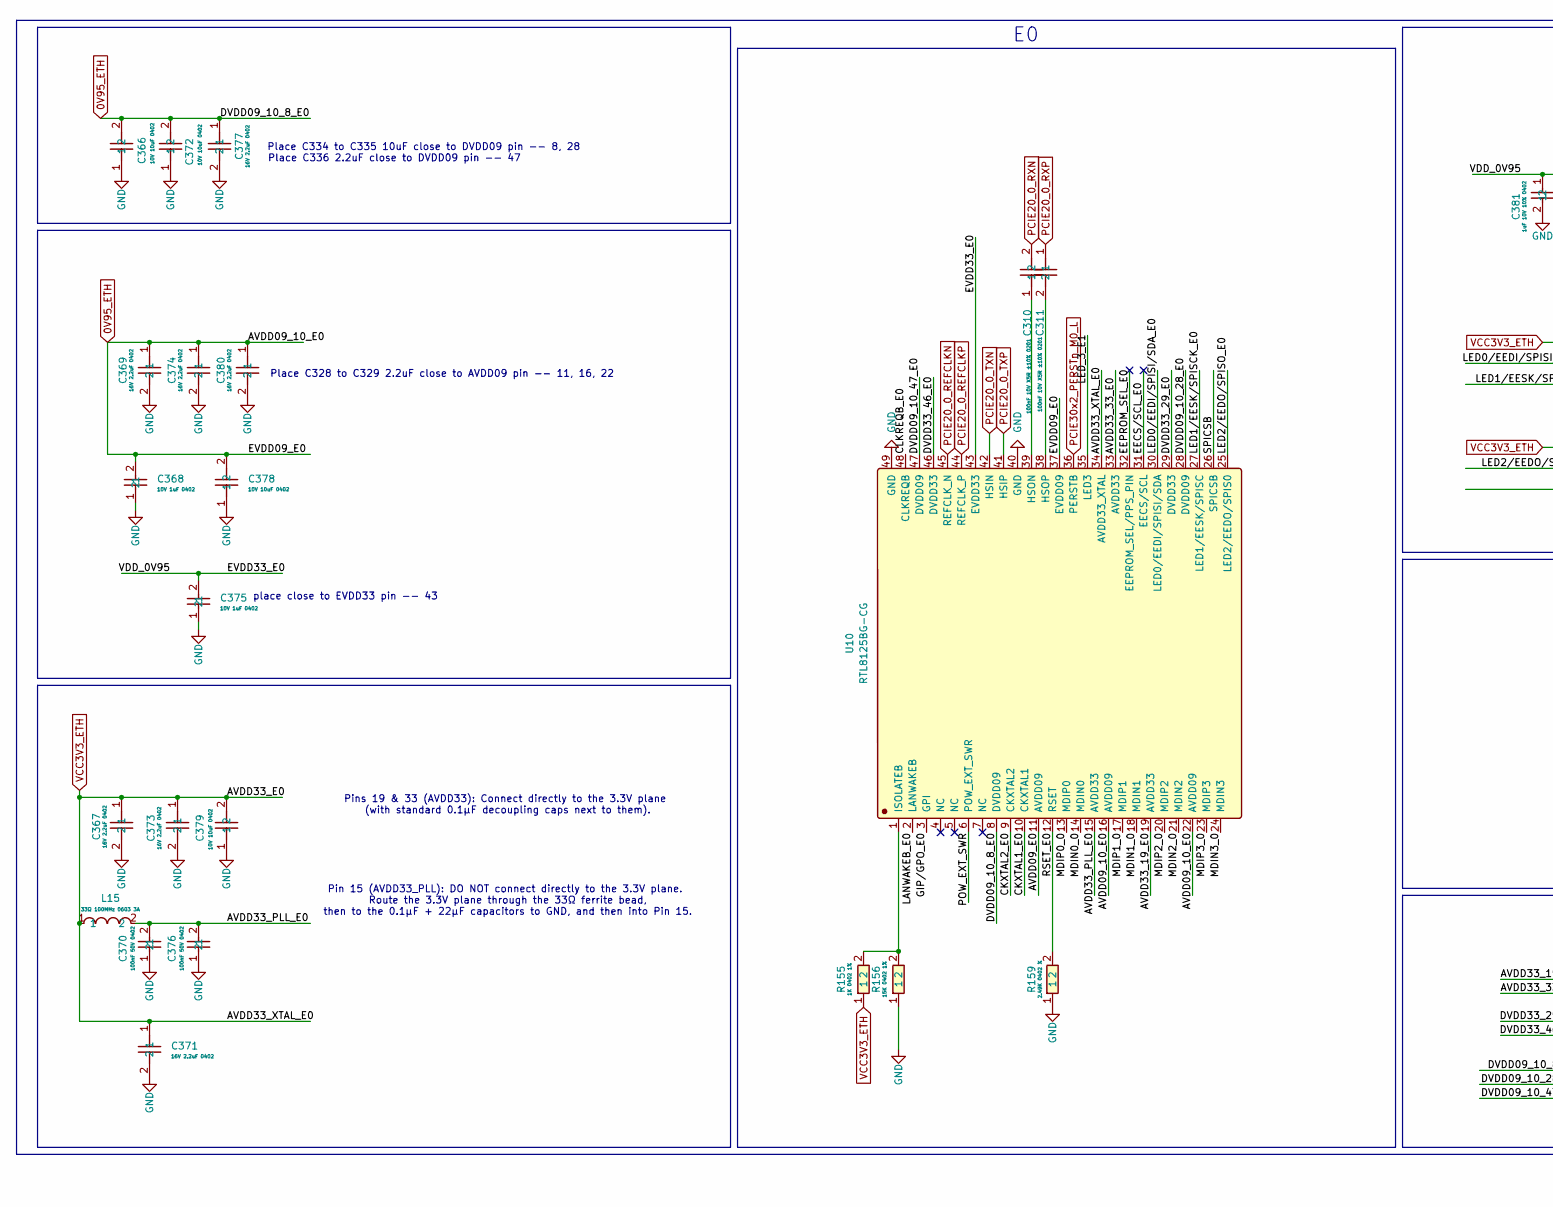
[picture p36: schematic ETHERNET_MAGNETICS-11.kicad_sch, part in row 1, column 1]

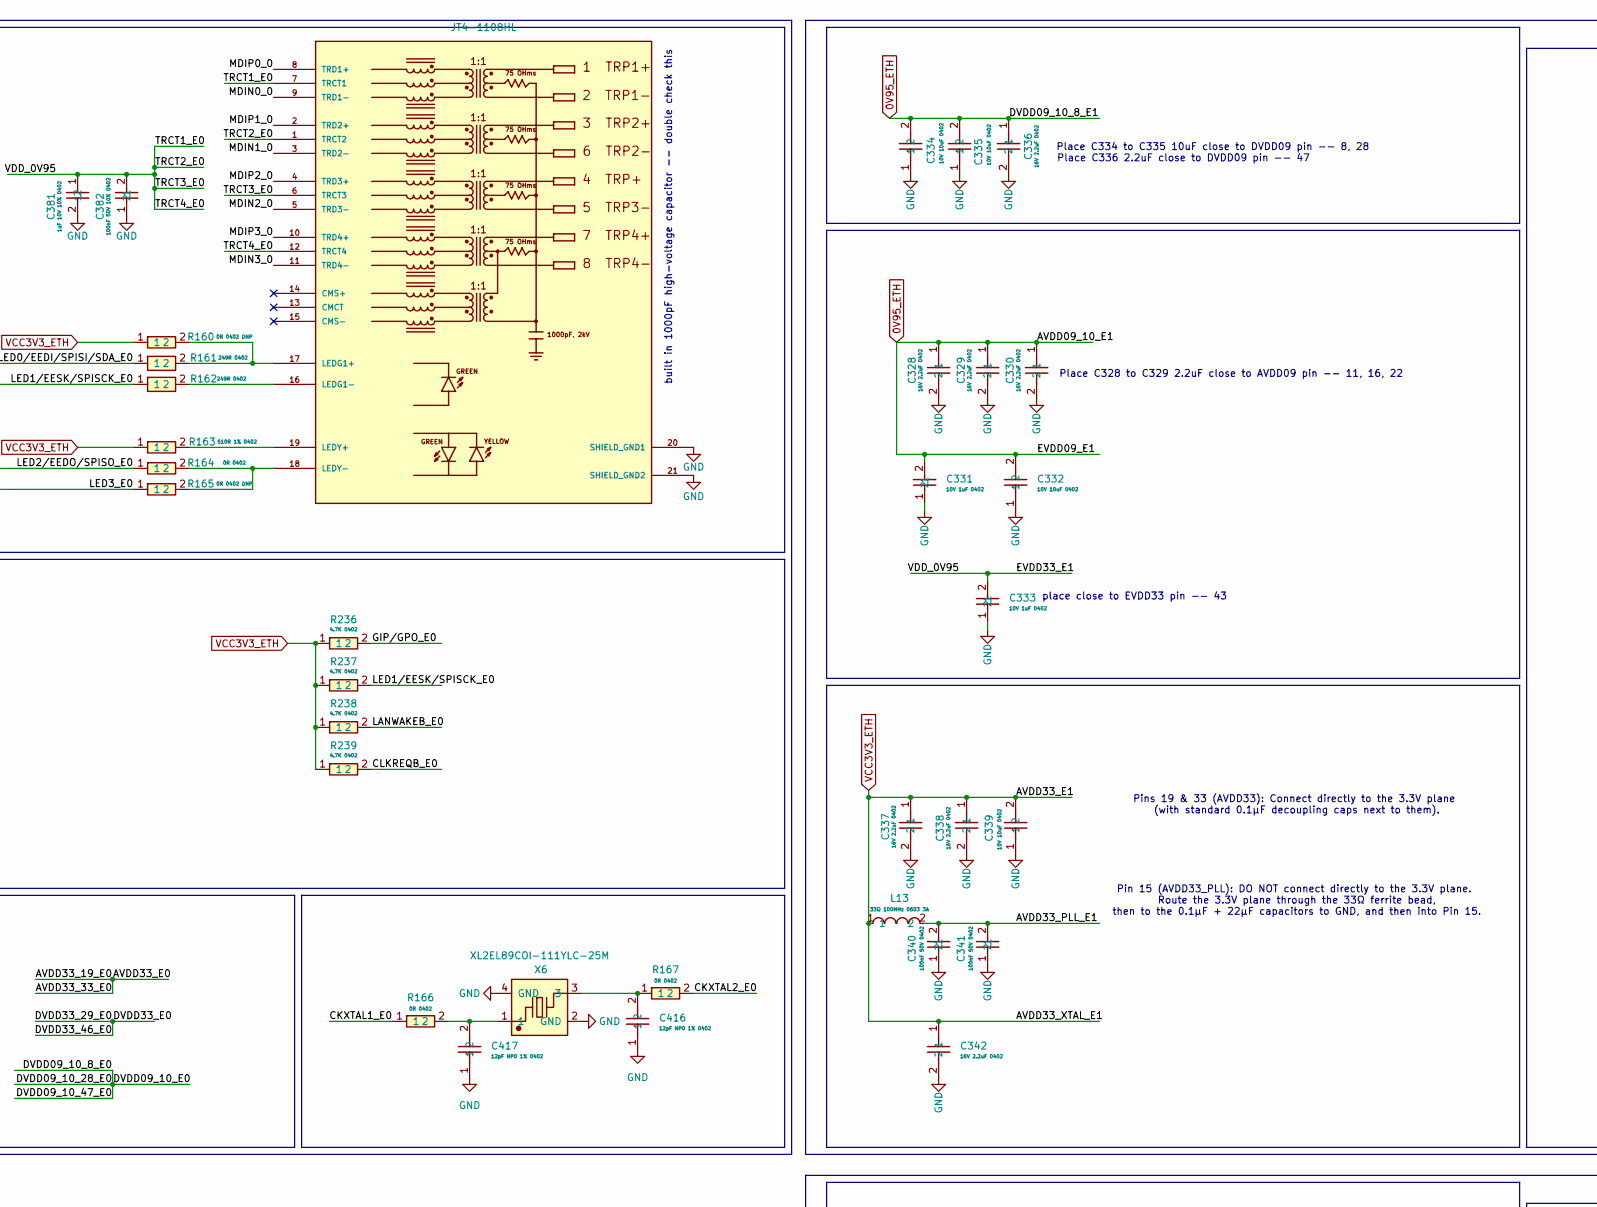
[picture p37: schematic ETHERNET_MAGNETICS-11.kicad_sch, part in row 1, column 2]

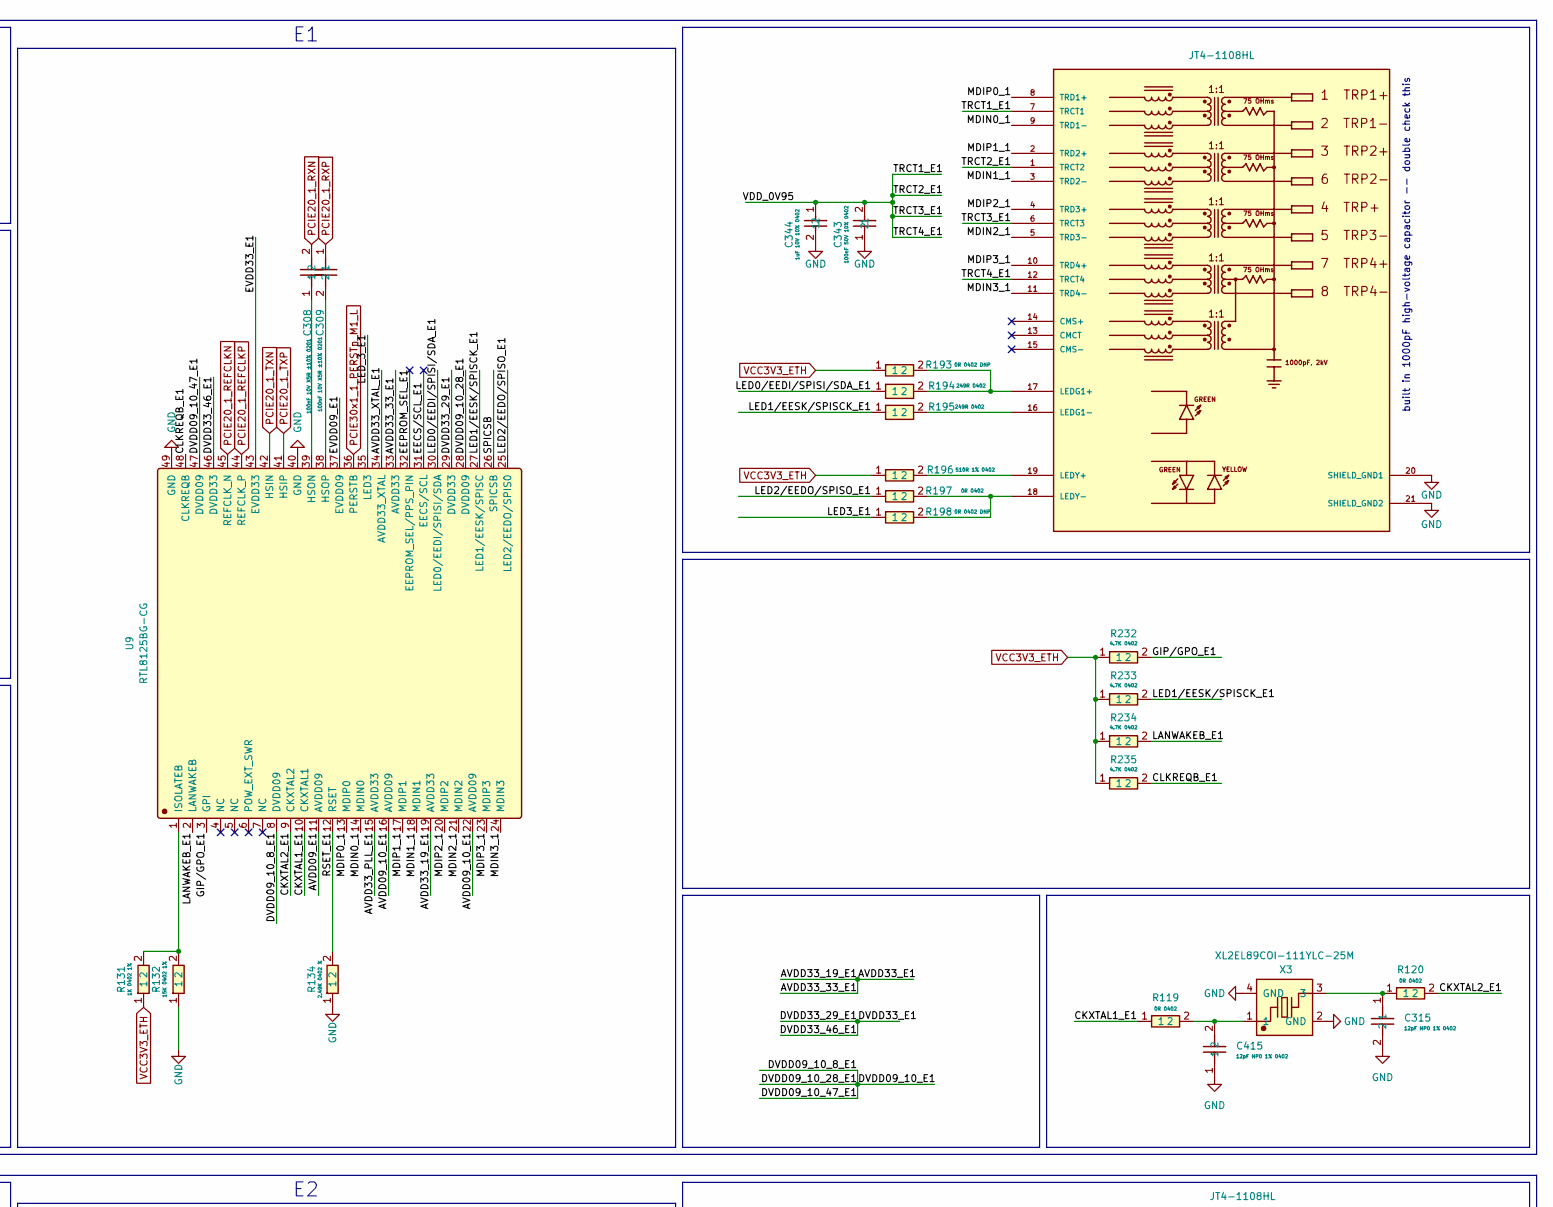
[picture p38: schematic ETHERNET_MAGNETICS-11.kicad_sch, part in row 1, column 3]

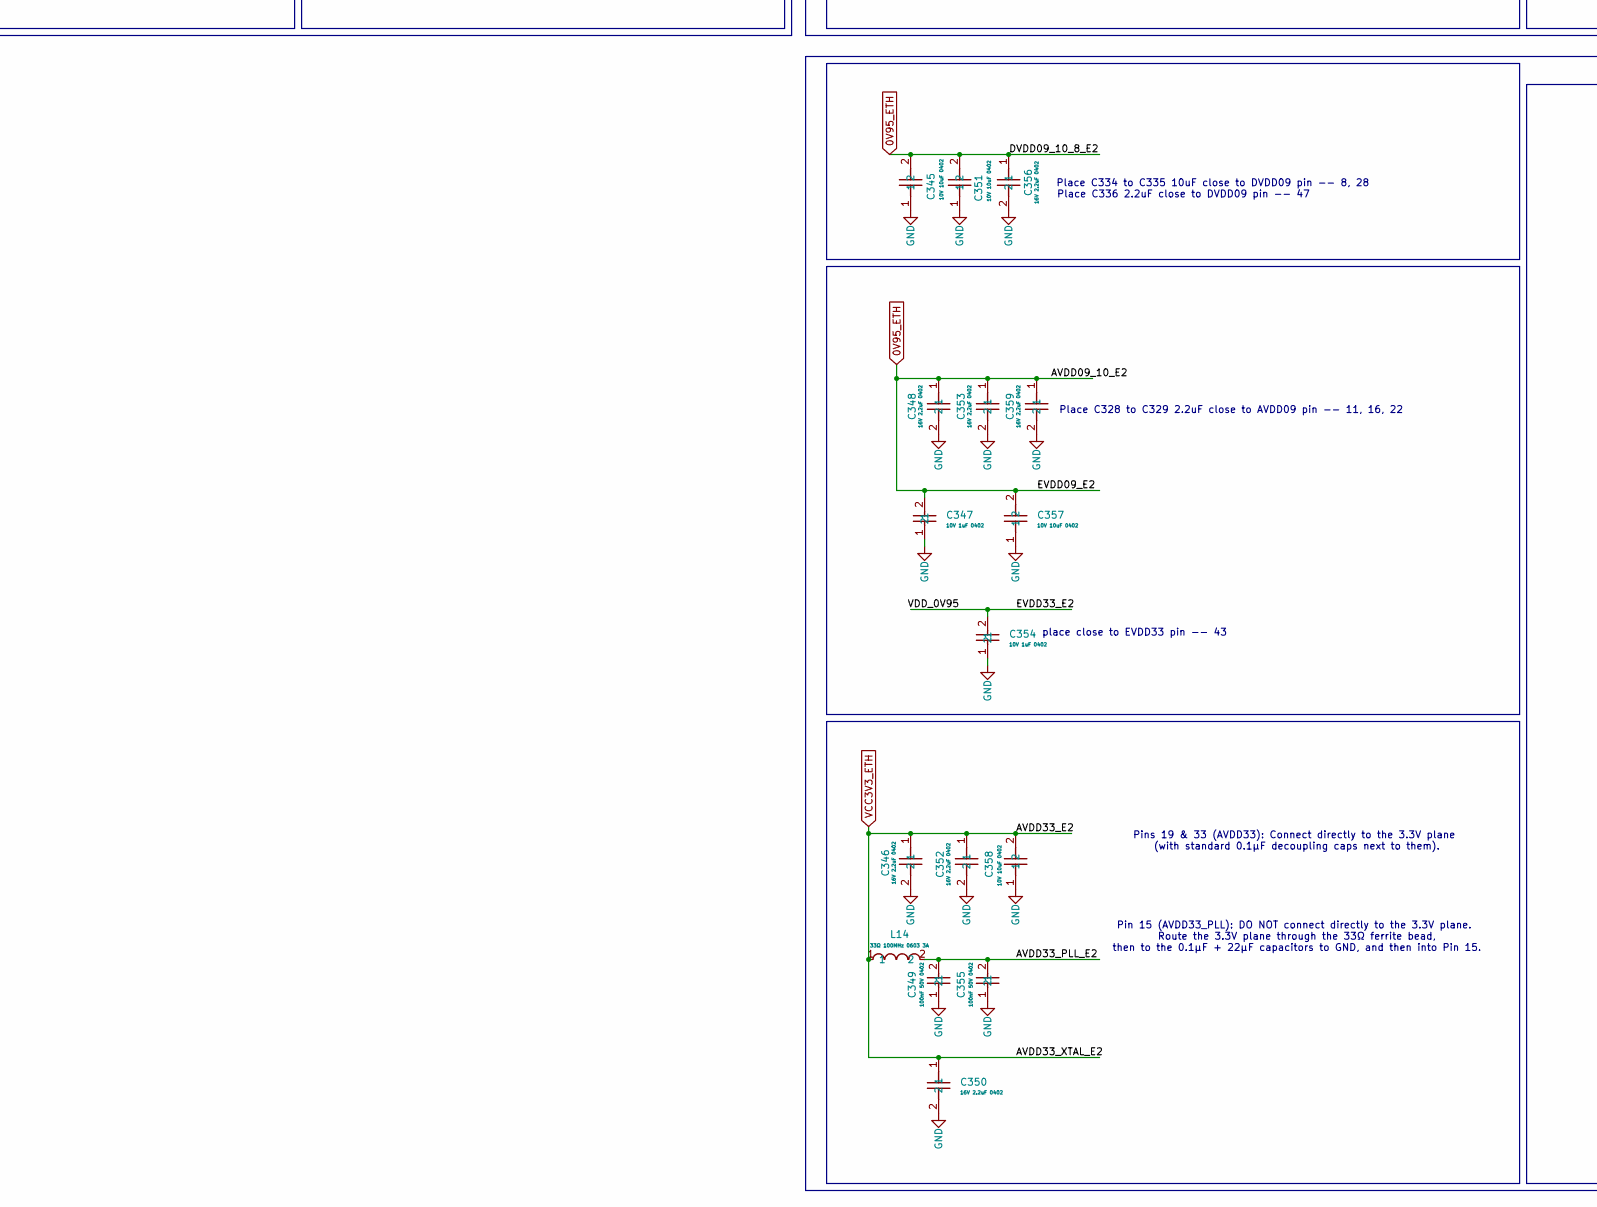
[picture p39: schematic ETHERNET_MAGNETICS-11.kicad_sch, part in row 2, column 2]

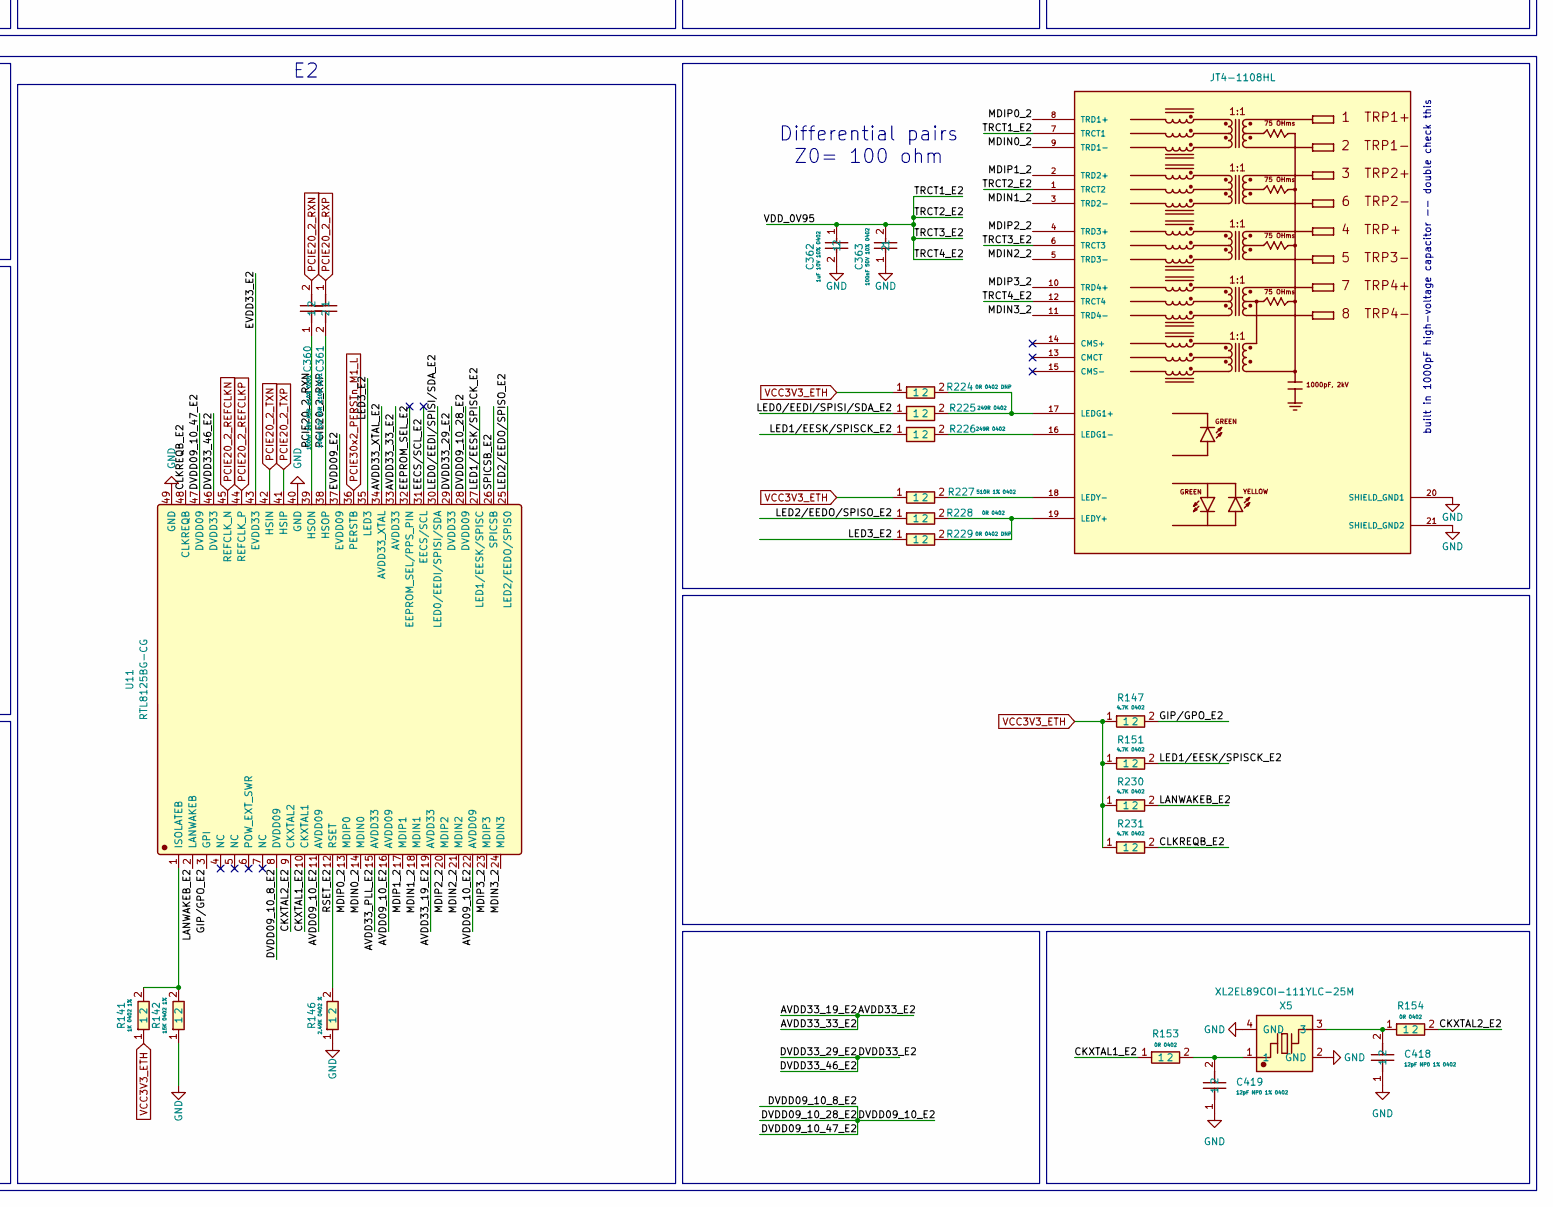
[picture p40: schematic ETHERNET_MAGNETICS-11.kicad_sch, part in row 2, column 3]

Parts:
C308, C309, C310, C311, C360, C361: 100nF 10V X5R ±10% 0201; CL03A104KP3NNNC; Manufacturer Part CL03A104KP3NNNC; LCSC C49062
C315, C415, C416, C417, C418, C419: 12pF NP0 1% 0402; RC0402FR-071KL; Manufacturer Part CC0402FRNPO9BN120; LCSC C326662
C328, C329, C330, C336, C337, C338, C342, C346, C348, C350, C352, C353, C356, C359, C367, C369, C371, C373, C374, C377, C380: 16V 2.2uF 0402; FRC0402F1693TS; Manufacturer Part CL05A225KO5NQNC; LCSC C170151
C331, C333, C347, C354, C368, C375: 10V 1uF 0402; FRC0402F1693TS; Manufacturer Part CL05A105KP5NNNC; LCSC C14445
C332, C334, C335, C339, C345, C351, C357, C358, C366, C372, C378, C379: 10V 10uF 0402; 10uF_X5R_10V_0402; Manufacturer Part CL05A106MP5NUNC; LCSC C315248
C340, C341, C349, C355, C370, C376: 100nF 50V 0402; RC0402JR-070RL; Manufacturer Part CC0402KRX5R9BB104; LCSC C105882
C343, C363, C382: 100nF 50V 10% 0402; RC0402JR-070RL; Manufacturer Part CC0402KRX5R9BB104; LCSC C105882
C344, C362, C381: 1uF 10V 10% 0402; FRC0402F1693TS; Manufacturer Part CL05A105KP5NNNC; LCSC C14445
J0, J1, J2: JT4-1108HL; PULSE_JT4-1108HL
L13, L14, L15: 33Ω 100MHz 0603 3A; BLM18PG330SN1D; Manufacturer Part BLM18PG330SN1D; LCSC C88984
R119, R120, R153, R154, R164, R166, R167, R197, R228: 0R 0402; RC0402JR-070RL; Manufacturer Part RC0402JR-070RL; LCSC C60485
R131, R141, R155: 1K 0402 1%; RC0402FR-071KL; Manufacturer Part RC0402FR-071KL; LCSC C106235
R132, R142, R156: 15K 0402 1%; RC0402FR-0715KL; Manufacturer Part RC0402FR-0715KL; LCSC C114761
R134, R146, R159: 2.49K 0402 %; RC0402FR-072K49L; Manufacturer Part RC0402FR-072K49L; LCSC C145071
R147, R151, R230, R231, R232, R233, R234, R235, R236, R237, R238, R239: 4.7K 0402; RC0402FR-074K7L; Manufacturer Part RC0402FR-074K7L; LCSC C105871
R160, R165, R193, R198, R224, R229: 0R 0402 DNP; RC0402JR-070RL; Manufacturer Part RC0402JR-070RL; LCSC C60485
R161, R162, R194, R195, R225, R226: 249R 0402; CRCW0402249RFKED; Manufacturer Part CRCW0402249RFKED; LCSC C482112
R163, R196, R227: 510R 1% 0402; RC0402FR-07510RL; Manufacturer Part RC0402FR-07510RL; LCSC C276273
U9, U10, U11: RTL8125BG-CG; Manufacturer Part RTL8125BG-CG; LCSC C3013605
X3, X5, X6: XL2EL89COI-111YLC-25M; Manufacturer Part XL2EL89COI-111YLC-25M; LCSC C5444544

Connections:
0V95_ETH: C328.1, C329.1, C330.1, C331.2, C332.2, C334.2, C335.2, C336.1, C345.2, C347.2, C348.1, C351.2, C353.1, C356.1, C357.2, C359.1, C366.2, C368.2, C369.1, C372.2, C374.1, C377.1, C378.2, C380.1, U9.8 (DVDD09), U9.16 (AVDD09), U9.22 (AVDD09), U9.28 (DVDD09), U9.37 (EVDD09), U9.47 (DVDD09), U10.8 (DVDD09), U10.16 (AVDD09), U10.22 (AVDD09), U10.28 (DVDD09), U10.37 (EVDD09), U10.47 (DVDD09), U11.8 (DVDD09), U11.11 (AVDD09), U11.16 (AVDD09), U11.22 (AVDD09), U11.28 (DVDD09), U11.37 (EVDD09), U11.47 (DVDD09)
AVDD09_E0: U10.11 (AVDD09)
AVDD09_E1: U9.11 (AVDD09)
AVDD33_PLL_E0: C370.2, C376.2, L15.2, U10.15 (AVDD33)
AVDD33_PLL_E1: C340.2, C341.2, L13.2, U9.15 (AVDD33)
AVDD33_PLL_E2: C349.2, C355.2, L14.2, U11.15 (AVDD33)
CKXTAL1_E0: R166.1, U10.10 (CKXTAL1)
CKXTAL1_E1: R119.1, U9.10 (CKXTAL1)
CKXTAL1_E2: R153.1, U11.10 (CKXTAL1)
CKXTAL2_E0: R167.2, U10.9 (CKXTAL2)
CKXTAL2_E1: R120.2, U9.9 (CKXTAL2)
CKXTAL2_E2: R154.2, U11.9 (CKXTAL2)
CLKREQB_E0: R239.2, U10.48 (CLKREQB)
CLKREQB_E1: R235.2, U9.48 (CLKREQB)
CLKREQB_E2: R231.2, U11.48 (CLKREQB)
DVDD33_29_E0: U10.29 (DVDD33), U10.46 (DVDD33)
DVDD33_29_E1: U9.29 (DVDD33), U9.46 (DVDD33)
DVDD33_29_E2: U11.29 (DVDD33), U11.46 (DVDD33)
EECS/SCL_E0: U10.31 (EECS/SCL)
EECS/SCL_E1: U9.31 (EECS/SCL)
EECS/SCL_E2: U11.31 (EECS/SCL)
EEPROM_SEL_E0: U10.32 (EEPROM_SEL/PPS_PIN)
EEPROM_SEL_E1: U9.32 (EEPROM_SEL/PPS_PIN)
EEPROM_SEL_E2: U11.32 (EEPROM_SEL/PPS_PIN)
EVDD33_E0: C333.2, C343.2, C344.1, C354.2, C362.1, C363.2, C375.2, C381.1, C382.2, J0.1 (TRCT2), J0.6 (TRCT3), J0.7 (TRCT1), J0.12 (TRCT4), J1.1 (TRCT2), J1.6 (TRCT3), J1.7 (TRCT1), J1.12 (TRCT4), J2.1 (TRCT2), J2.6 (TRCT3), J2.7 (TRCT1), J2.12 (TRCT4), U9.43 (EVDD33), U10.43 (EVDD33), U11.43 (EVDD33)
GIP/GPO_E0: R236.2, U10.3 (GPI)
GIP/GPO_E1: R232.2, U9.3 (GPI)
GIP/GPO_E2: R147.2, U11.3 (GPI)
GND: C315.2, C328.2, C329.2, C330.2, C331.1, C332.1, C333.1, C334.1, C335.1, C336.2, C337.2, C338.2, C339.1, C340.1, C341.1, C342.2, C343.1, C344.2, C345.1, C346.2, C347.1, C348.2, C349.1, C350.2, C351.1, C352.2, C353.2, C354.1, C355.1, C356.2, C357.1, C358.1, C359.2, C362.2, C363.1, C366.1, C367.2, C368.1, C369.2, C370.1, C371.2, C372.1, C373.2, C374.2, C375.1, C376.1, C377.2, C378.1, C379.1, C380.2, C381.2, C382.1, C415.1, C416.1, C417.1, C418.1, C419.1, J0.20 (SHIELD_GND1), J0.21 (SHIELD_GND2), J1.20 (SHIELD_GND1), J1.21 (SHIELD_GND2), J2.20 (SHIELD_GND1), J2.21 (SHIELD_GND2), R132.1, R134.1, R142.1, R146.1, R156.1, R159.1, U9.40 (GND), U9.49 (GND), U10.40 (GND), U10.49 (GND), U11.40 (GND), U11.49 (GND), X3.2 (GND), X3.4 (GND), X5.2 (GND), X5.4 (GND), X6.2 (GND), X6.4 (GND)
LANWAKEB_E0: R238.2, U10.2 (LANWAKEB)
LANWAKEB_E1: R234.2, U9.2 (LANWAKEB)
LANWAKEB_E2: R230.2, U11.2 (LANWAKEB)
LED0/EEDI/SPISI/SDA_E0: R161.1, U10.30 (LED0/EEDI/SPISI/SDA)
LED0/EEDI/SPISI/SDA_E1: R194.1, U9.30 (LED0/EEDI/SPISI/SDA)
LED0/EEDI/SPISI/SDA_E2: R225.1, U11.30 (LED0/EEDI/SPISI/SDA)
LED1/EESK/SPISCK_E0: R162.1, R237.2, U10.27 (LED1/EESK/SPISC)
LED1/EESK/SPISCK_E1: R195.1, R233.2, U9.27 (LED1/EESK/SPISC)
LED1/EESK/SPISCK_E2: R151.2, R226.1, U11.27 (LED1/EESK/SPISC)
LED2/EEDO/SPISO_E0: R164.1, U10.25 (LED2/EEDO/SPIS0)
LED2/EEDO/SPISO_E1: R197.1, U9.25 (LED2/EEDO/SPIS0)
LED2/EEDO/SPISO_E2: R228.1, U11.25 (LED2/EEDO/SPIS0)
LED3_E0: R165.1
LED3_E1: R198.1
LED3_E2: R229.1, U11.35 (LED3)
LED_3_E1: U9.35 (LED3), U10.35 (LED3)
MDIN0_0: J0.9 (TRD1-), U10.14 (MDIN0)
MDIN0_1: J1.9 (TRD1-), U9.14 (MDIN0)
MDIN0_2: J2.9 (TRD1-), U11.14 (MDIN0)
MDIN1_0: J0.3 (TRD2-), U10.18 (MDIN1)
MDIN1_1: J1.3 (TRD2-), U9.18 (MDIN1)
MDIN1_2: J2.3 (TRD2-), U11.18 (MDIN1)
MDIN2_0: J0.5 (TRD3-), U10.21 (MDIN2)
MDIN2_1: J1.5 (TRD3-), U9.21 (MDIN2)
MDIN2_2: J2.5 (TRD3-), U11.21 (MDIN2)
MDIN3_0: J0.11 (TRD4-), U10.24 (MDIN3)
MDIN3_1: J1.11 (TRD4-), U9.24 (MDIN3)
MDIN3_2: J2.11 (TRD4-), U11.24 (MDIN3)
MDIP0_0: J0.8 (TRD1+), U10.13 (MDIP0)
MDIP0_1: J1.8 (TRD1+), U9.13 (MDIP0)
MDIP0_2: J2.8 (TRD1+), U11.13 (MDIP0)
MDIP1_0: J0.2 (TRD2+), U10.17 (MDIP1)
MDIP1_1: J1.2 (TRD2+), U9.17 (MDIP1)
MDIP1_2: J2.2 (TRD2+), U11.17 (MDIP1)
MDIP2_0: J0.4 (TRD3+), U10.20 (MDIP2)
MDIP2_1: J1.4 (TRD3+), U9.20 (MDIP2)
MDIP2_2: J2.4 (TRD3+), U11.20 (MDIP2)
MDIP3_0: J0.10 (TRD4+), U10.23 (MDIP3)
MDIP3_1: J1.10 (TRD4+), U9.23 (MDIP3)
MDIP3_2: J2.10 (TRD4+), U11.23 (MDIP3)
unnamed: C308.1, U9.39 (HSON)
unnamed: C309.2, U9.38 (HSOP)
unnamed: C310.1, U10.39 (HSON)
unnamed: C311.2, U10.38 (HSOP)
unnamed: C315.1, R120.1, X3.3
unnamed: C415.2, R119.2, X3.1
unnamed: C416.2, R167.1, X6.3
unnamed: C417.2, R166.2, X6.1
unnamed: C418.2, R154.1, X5.3
unnamed: C419.2, R153.2, X5.1
unnamed: J0.16 (LEDG1-), R162.2
unnamed: J0.17 (LEDG1+), R160.2, R161.2
unnamed: J0.18 (LEDY-), R164.2, R165.2
unnamed: J0.19 (LEDY+), R163.2
unnamed: J1.16 (LEDG1-), R195.2
unnamed: J1.17 (LEDG1+), R193.2, R194.2
unnamed: J1.18 (LEDY-), R197.2, R198.2
unnamed: J1.19 (LEDY+), R196.2
unnamed: J2.16 (LEDG1-), R226.2
unnamed: J2.17 (LEDG1+), R224.2, R225.2
unnamed: J2.18 (LEDY-), R227.2
unnamed: J2.19 (LEDY+), R228.2, R229.2
unnamed: R131.2, R132.2, U9.1 (ISOLATEB)
unnamed: R141.2, R142.2, U11.1 (ISOLATEB)
unnamed: R155.2, R156.2, U10.1 (ISOLATEB)
PCIE20_0_REFCLKN: U10.45 (REFCLK_N)
PCIE20_0_REFCLKP: U10.44 (REFCLK_P)
PCIE20_0_RXN: C310.2
PCIE20_0_RXP: C311.1
PCIE20_0_TXN: U10.42 (HSIN)
PCIE20_0_TXP: U10.41 (HSIP)
PCIE20_1_REFCLKN: U9.45 (REFCLK_N)
PCIE20_1_REFCLKP: U9.44 (REFCLK_P)
PCIE20_1_RXN: C308.2
PCIE20_1_RXP: C309.1
PCIE20_1_TXN: U9.42 (HSIN)
PCIE20_1_TXP: U9.41 (HSIP)
PCIE20_2_REFCLKN: U11.45 (REFCLK_N)
PCIE20_2_REFCLKP: U11.44 (REFCLK_P)
PCIE20_2_RXN: C360.1, C360.2, U11.39 (HSON)
PCIE20_2_RXP: C361.1, C361.2, U11.38 (HSOP)
PCIE20_2_TXN: U11.42 (HSIN)
PCIE20_2_TXP: U11.41 (HSIP)
PCIE30x1_1_PERSTn_M1_L: U9.36 (PERSTB)
PCIE30x2_PERSTn_M0_L: U10.36 (PERSTB)
PCIE30x2_PERSTn_M1_L: U11.36 (PERSTB)
POW_EXT_SWR: U10.6 (POW_EXT_SWR)
RSET_E0: R159.2, U10.12 (RSET)
RSET_E1: R134.2, U9.12 (RSET)
RSET_E2: R146.2, U11.12 (RSET)
SPICSB: U9.26 (SPICSB), U10.26 (SPICSB)
SPICSB_E2: U11.26 (SPICSB)
VCC3V3_ETH: C337.1, C338.1, C339.2, C342.1, C346.1, C350.1, C352.1, C358.2, C367.1, C371.1, C373.1, C379.2, L13.1, L14.1, L15.1, R131.1, R141.1, R147.1, R151.1, R155.1, R160.1, R163.1, R193.1, R196.1, R224.1, R227.1, R230.1, R231.1, R232.1, R233.1, R234.1, R235.1, R236.1, R237.1, R238.1, R239.1, U9.19 (AVDD33), U9.33 (AVDD33), U9.34 (AVDD33_XTAL), U10.19 (AVDD33), U10.33 (AVDD33), U10.34 (AVDD33_XTAL), U11.19 (AVDD33), U11.33 (AVDD33), U11.34 (AVDD33_XTAL)

Notes on the sheet:
Place C336 2.2uF close to DVDD09 pin -- 47
place close to EVDD33 pin -- 43
Place C334 to C335 10uF close to DVDD09 pin -- 8, 28
Pins 19 & 33 (AVDD33): Connect directly to the 3.3V plane (with standard 0.1µF decoupling caps next to them). Pin 15 (AVDD33_PLL): DO NOT connect directly to the 3.3V plane. Route the 3.3V plane through the 33Ω ferrite bead, then to the 0.1µF + 22µF capacitors to GND, and then into Pin 15.
built in 1000pF high-voltage capacitor -- double check this
Place C328 to C329 2.2uF close to AVDD09 pin -- 11, 16, 22
Differential pairs Z0= 100 ohm
