CXD8/CXD-ROUTER/Sch/GPIO_ADC_SYSTEM_IO-6.kicad_sch

## KiCad design Sch/GPIO_ADC_SYSTEM_IO-6.kicad_sch (2026-08-12)

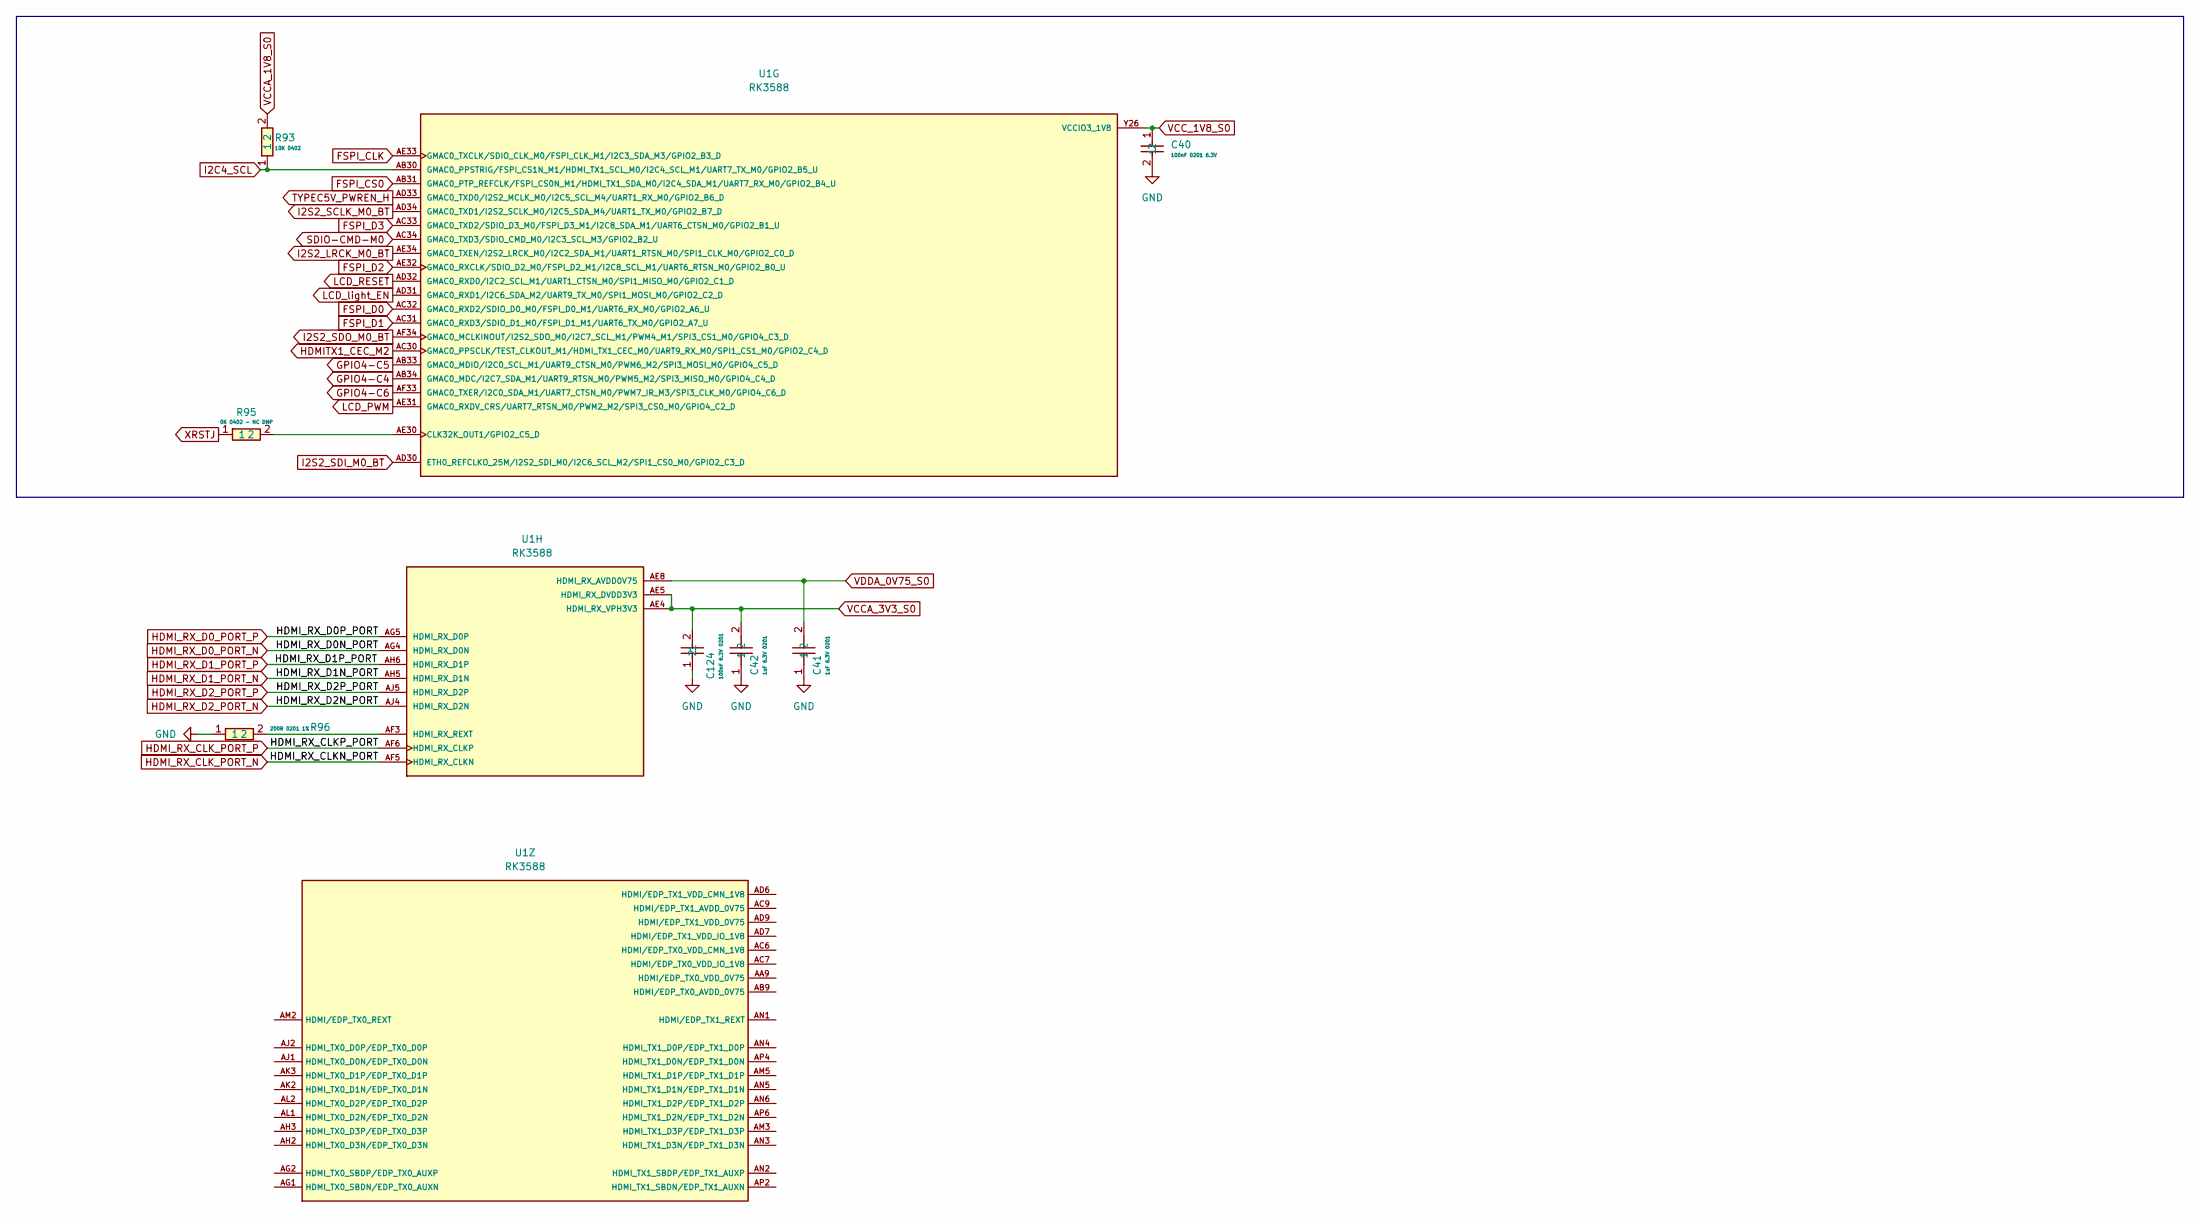
[picture p41: schematic GPIO_ADC_SYSTEM_IO-6.kicad_sch]

Parts:
C40: 100nF 0201 6.3V; RC0201FR-0749R9L; Manufacturer Part CC0201KRX5R5BB104; LCSC C190187
C41, C42: 1uF 6.3V 0201; RC0201FR-0749R9L; Manufacturer Part CC0201KRX5R5BB105; LCSC C541330
C124: 100nF 6.3V 0201; RC0201FR-0749R9L; Manufacturer Part CC0201KRX5R5BB104; LCSC C190187
R93: 10K 0402; RC0402JR-0710KL; Manufacturer Part RC0402JR-0710KL; LCSC C60489
R95: 0K 0402 - NC DNP; RC0402JR-070RL; Manufacturer Part RC0402JR-070RL; LCSC C60485
R96: 200R 0201 1%; RC0201FR-07200RL; Manufacturer Part RC0201FR-07200RL; LCSC C274337
U1: RK3588; BGA1088C65P34X34_2300X2300X204N; PARTREV 1.0

Connections:
FSPI_CLK: U1.AE33 (GMAC0_TXCLK/SDIO_CLK_M0/FSPI_CLK_M1/I2C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)
FSPI_CS0: U1.AB31 (GMAC0_PTP_REFCLK/FSPI_CS0N_M1/HDMI_TX1_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)
FSPI_D0: U1.AC32 (GMAC0_RXD2/SDIO_D0_M0/FSPI_D0_M1/UART6_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)
FSPI_D1: U1.AC31 (GMAC0_RXD3/SDIO_D1_M0/FSPI_D1_M1/UART6_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)
FSPI_D2: U1.AE32 (GMAC0_RXCLK/SDIO_D2_M0/FSPI_D2_M1/I2C8_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)
FSPI_D3: U1.AC33 (GMAC0_TXD2/SDIO_D3_M0/FSPI_D3_M1/I2C8_S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)
GND: C40.2, C41.1, C42.1, C124.1, R96.1
GPIO4-C4: U1.AB34 (GMAC0_MDC/I2C7_SDA_M1/UART9_RTSN_M0/PWM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)
GPIO4-C5: U1.AB33 (GMAC0_MDIO/I2C0_SCL_M1/UART9_CTSN_M0/PW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)
GPIO4-C6: U1.AF33 (GMAC0_TXER/I2C0_SDA_M1/UART7_CTSN_M0/PW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)
HDMITX1_CEC_M2: U1.AC30 (GMAC0_PPSCLK/TEST_CLKOUT_M1/HDMI_TX1_CE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)
HDMI_RX_CLK_PORT_N: U1.AF5 (HDMI_RX_CLKN)
HDMI_RX_CLK_PORT_P: U1.AF6 (HDMI_RX_CLKP)
HDMI_RX_D0_PORT_N: U1.AG4 (HDMI_RX_D0N)
HDMI_RX_D0_PORT_P: U1.AG5 (HDMI_RX_D0P)
HDMI_RX_D1_PORT_N: U1.AH5 (HDMI_RX_D1N)
HDMI_RX_D1_PORT_P: U1.AH6 (HDMI_RX_D1P)
HDMI_RX_D2_PORT_N: U1.AJ4 (HDMI_RX_D2N)
HDMI_RX_D2_PORT_P: U1.AJ5 (HDMI_RX_D2P)
I2C4_SCL: R93.1, U1.AB30 (GMAC0_PPSTRIG/FSPI_CS1N_M1/HDMI_TX1_SCL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)
I2S2_LRCK_M0_BT: U1.AE34 (GMAC0_TXEN/I2S2_LRCK_M0/I2C2_SDA_M1/UAR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)
I2S2_SCLK_M0_BT: U1.AD34 (GMAC0_TXD1/I2S2_SCLK_M0/I2C5_SDA_M4/UAR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)
I2S2_SDI_M0_BT: U1.AD30 (ETH0_REFCLKO_25M/I2S2_SDI_M0/I2C6_SCL_M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)
I2S2_SDO_M0_BT: U1.AF34 (GMAC0_MCLKINOUT/I2S2_SDO_M0/I2C7_SCL_M1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)
LCD_PWM: U1.AE31 (GMAC0_RXDV_CRS/UART7_RTSN_M0/PWM2_M2/SP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)
LCD_RESET: U1.AD32 (GMAC0_RXD0/I2C2_SCL_M1/UART1_CTSN_M0/SP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)
LCD_light_EN: U1.AD31 (GMAC0_RXD1/I2C6_SDA_M2/UART9_TX_M0/SPI1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)
unnamed: R95.2, U1.AE30 (CLK32K_OUT1/GPIO2_C5_D)
unnamed: R96.2, U1.AF3 (HDMI_RX_REXT)
SDIO-CMD-M0: U1.AC34 (GMAC0_TXD3/SDIO_CMD_M0/I2C3_SCL_M3/GPIO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)
TYPEC5V_PWREN_H: U1.AD33 (GMAC0_TXD0/I2S2_MCLK_M0/I2C5_SCL_M4/UAR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)
VCCA_1V8_S0: R93.2
VCCA_3V3_S0: C42.2, C124.2, U1.AE4 (HDMI_RX_VPH3V3), U1.AE5 (HDMI_RX_DVDD3V3)
VCC_1V8_S0: C40.1, U1.Y26 (VCCIO3_1V8)
VDDA_0V75_S0: C41.2, U1.AE8 (HDMI_RX_AVDD0V75)
XRSTJ: R95.1
