CXD8/CXD-ROUTER/Sch/HDMI-9.kicad_sch

## KiCad design Sch/HDMI-9.kicad_sch (2026-08-12)

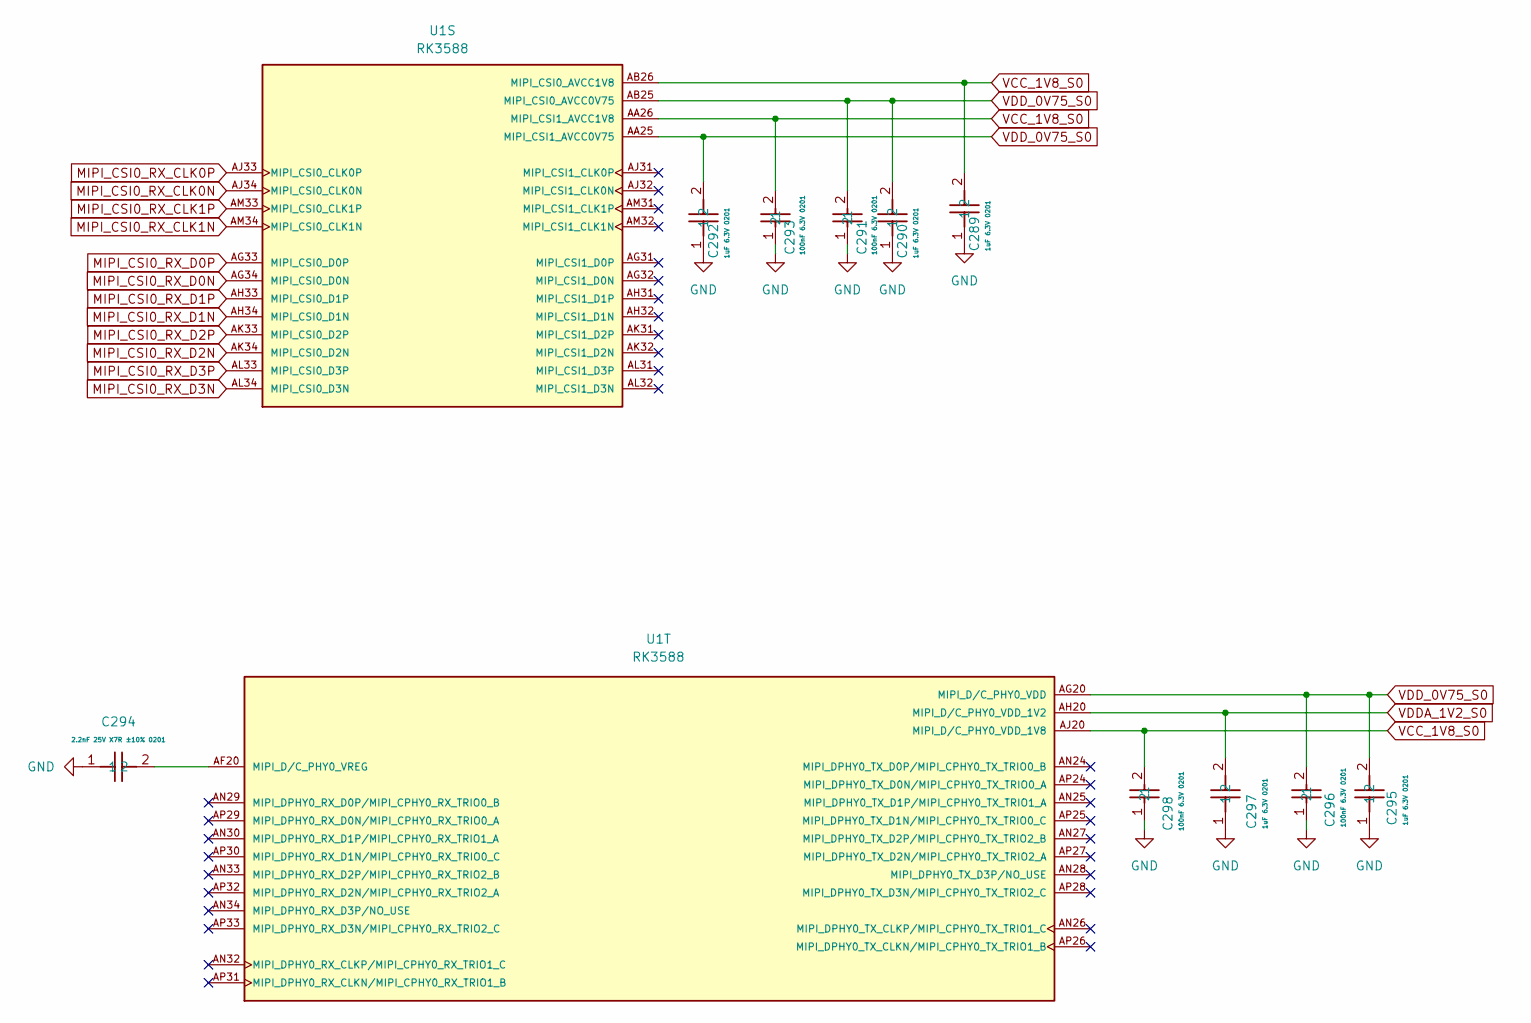
[picture p42: schematic HDMI-9.kicad_sch]

Parts:
C289, C290, C292, C295, C297: 1uF 6.3V 0201; RC0201FR-0749R9L; Manufacturer Part CC0201KRX5R5BB105; LCSC C541330
C291, C293, C296, C298: 100nF 6.3V 0201; RC0201FR-0749R9L; Manufacturer Part CC0201KRX5R5BB104; LCSC C190187
C294: 2.2nF 25V X7R ±10% 0201; RC0201FR-0747KL; Manufacturer Part GRM033R71E222KA12D; LCSC C161488
U1: RK3588; BGA1088C65P34X34_2300X2300X204N; PARTREV 1.0

Connections:
GND: C289.1, C290.1, C291.1, C292.1, C293.1, C294.1, C295.1, C296.1, C297.1, C298.1
MIPI_CSI0_RX_CLK0N: U1.AJ34 (MIPI_CSI0_CLK0N)
MIPI_CSI0_RX_CLK0P: U1.AJ33 (MIPI_CSI0_CLK0P)
MIPI_CSI0_RX_CLK1N: U1.AM34 (MIPI_CSI0_CLK1N)
MIPI_CSI0_RX_CLK1P: U1.AM33 (MIPI_CSI0_CLK1P)
MIPI_CSI0_RX_D0N: U1.AG34 (MIPI_CSI0_D0N)
MIPI_CSI0_RX_D0P: U1.AG33 (MIPI_CSI0_D0P)
MIPI_CSI0_RX_D1N: U1.AH34 (MIPI_CSI0_D1N)
MIPI_CSI0_RX_D1P: U1.AH33 (MIPI_CSI0_D1P)
MIPI_CSI0_RX_D2N: U1.AK34 (MIPI_CSI0_D2N)
MIPI_CSI0_RX_D2P: U1.AK33 (MIPI_CSI0_D2P)
MIPI_CSI0_RX_D3N: U1.AL34 (MIPI_CSI0_D3N)
MIPI_CSI0_RX_D3P: U1.AL33 (MIPI_CSI0_D3P)
unnamed: C294.2, U1.AF20 (MIPI_D/C_PHY0_VREG)
VCC_1V8_S0: C289.2, C293.2, C298.2, U1.AA26 (MIPI_CSI1_AVCC1V8), U1.AB26 (MIPI_CSI0_AVCC1V8), U1.AJ20 (MIPI_D/C_PHY0_VDD_1V8)
VDDA_1V2_S0: C297.2, U1.AH20 (MIPI_D/C_PHY0_VDD_1V2)
VDD_0V75_S0: C290.2, C291.2, C292.2, C295.2, C296.2, U1.AA25 (MIPI_CSI1_AVCC0V75), U1.AB25 (MIPI_CSI0_AVCC0V75), U1.AG20 (MIPI_D/C_PHY0_VDD)
