CXD8/CXD-ROUTER/Sch/LPDDR4-15.kicad_sch

## KiCad design Sch/LPDDR4-15.kicad_sch (2026-08-12)

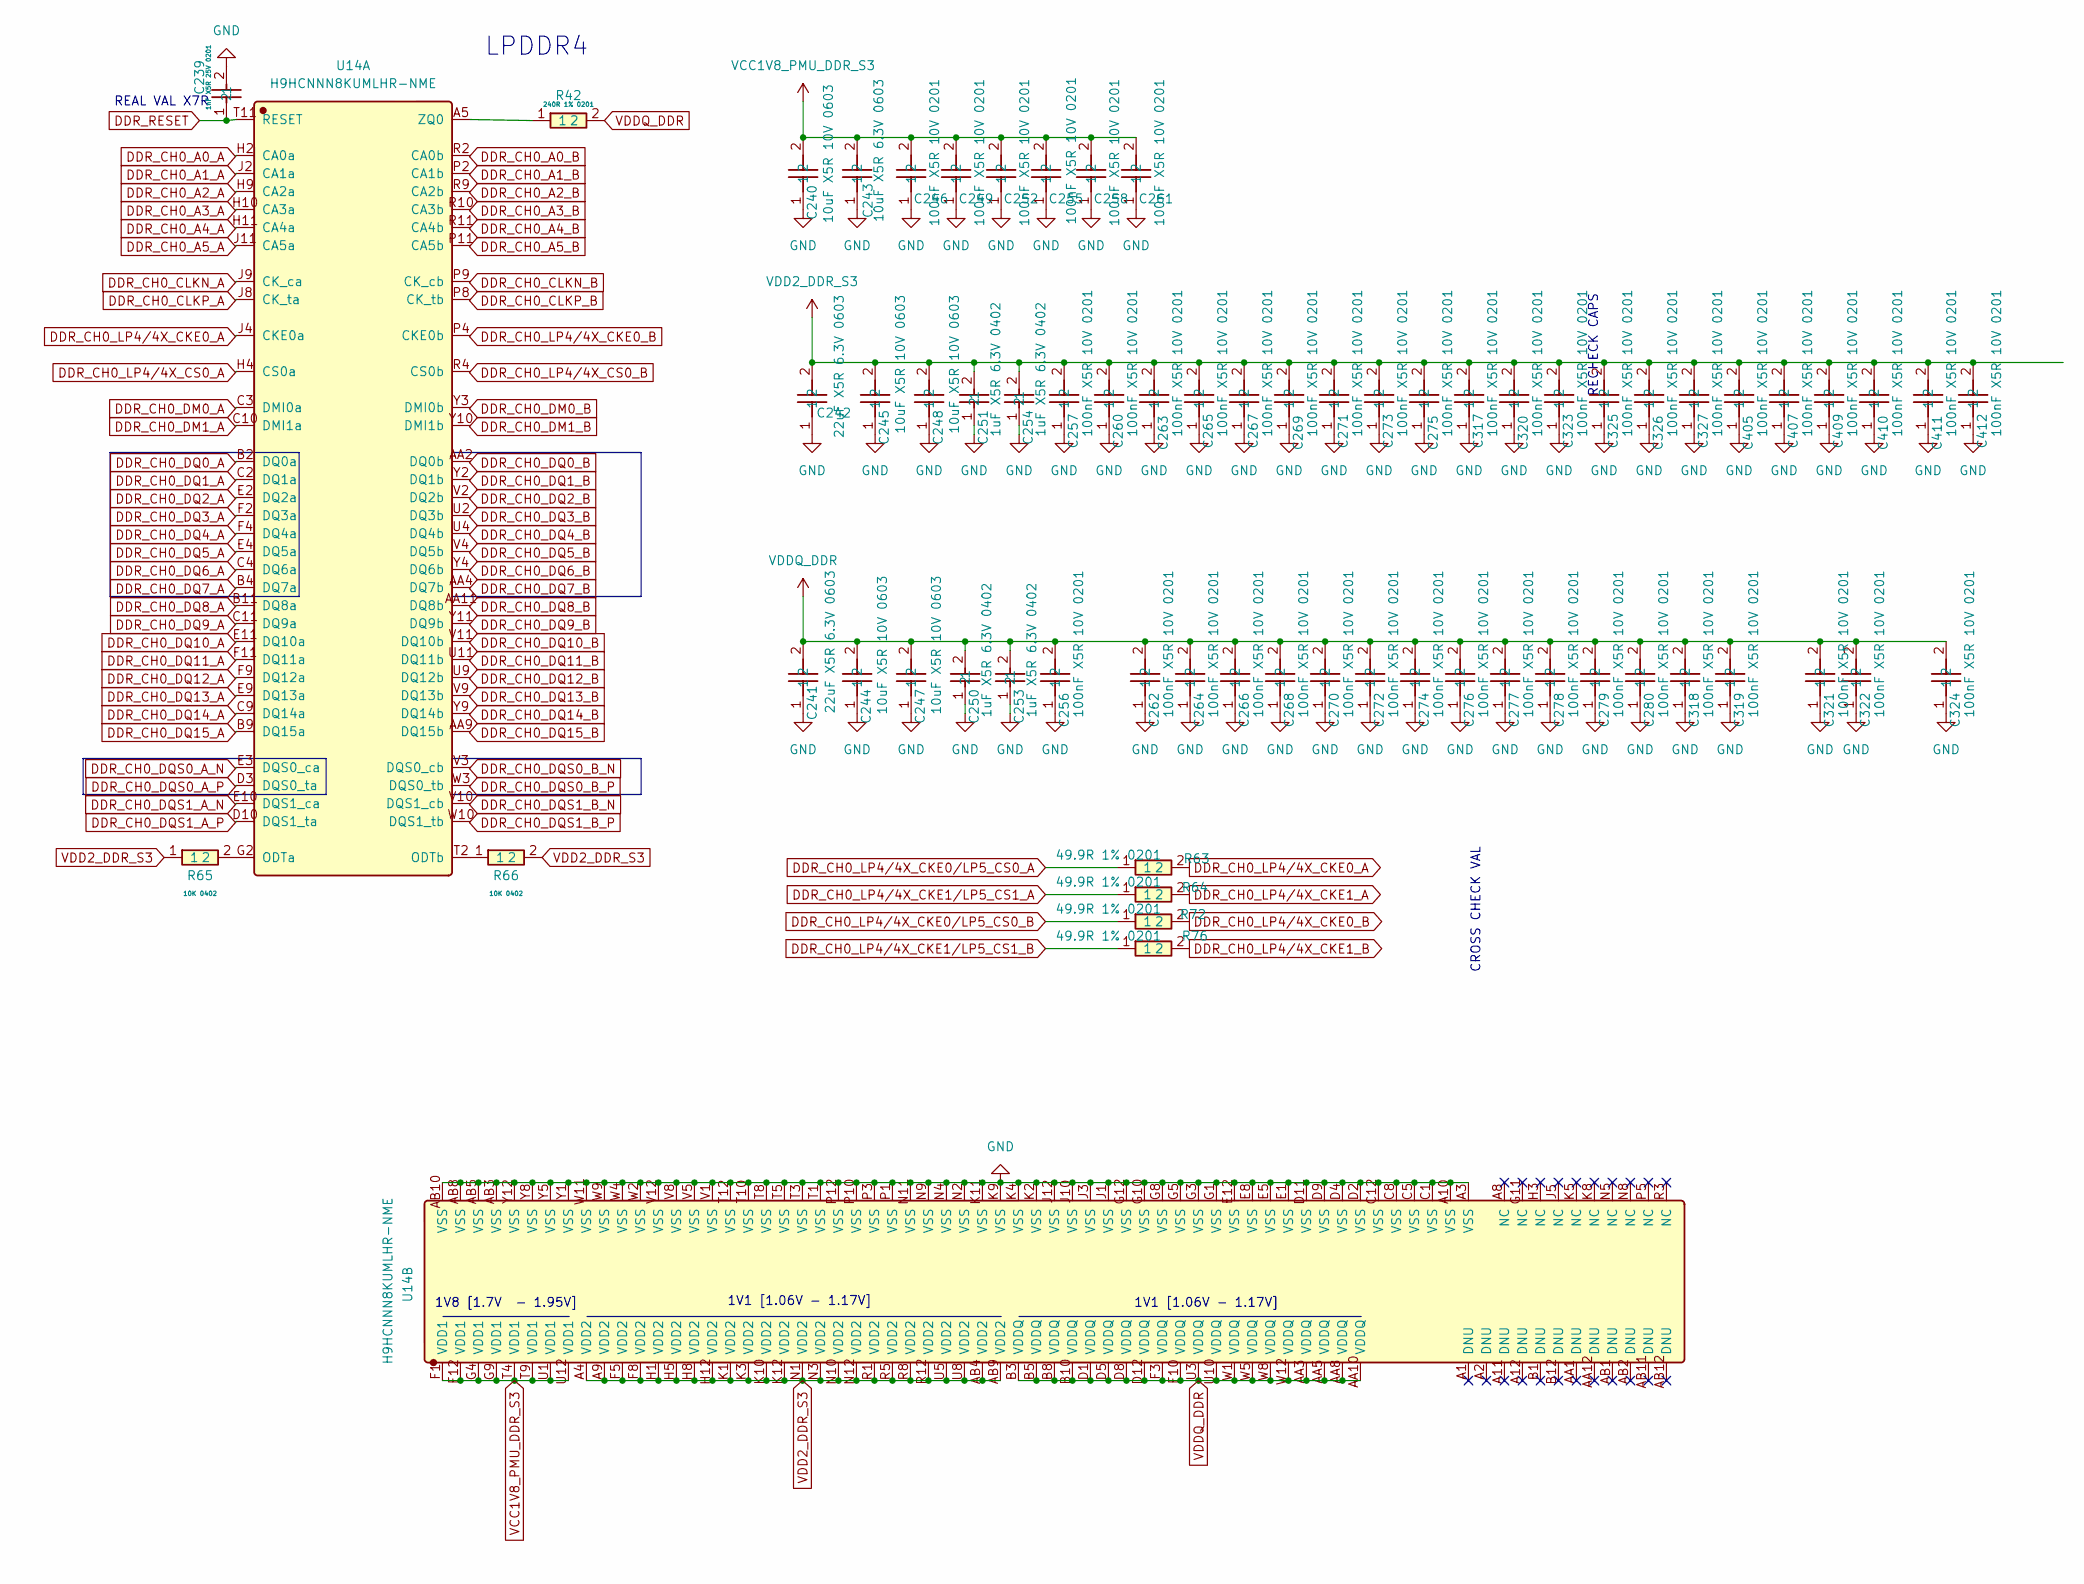
[picture p43: schematic LPDDR4-15.kicad_sch]

Parts:
C239: 1nF X5R 25V 0201; RC0201FR-07240RL; Manufacturer Part GRM033R71E102KA01D; LCSC C76943
C240, C244, C245, C247, C248: 10uF X5R 10V 0603; CL10A106KP8NNNC; Manufacturer Part CL10A106KP8NNNC; LCSC C19702
C241, C242: 22uF X5R 6.3V 0603; CL10A226MQ8NRNC; Manufacturer Part CL10A226MQ8NRNC; LCSC C59461
C243: 10uF X5R 6.3V 0603; CL10A106KQ8NNNC; Manufacturer Part CL10A106KQ8NNNC; LCSC C95839
C246, C249, C252, C255, C256, C257, C258, C260, C261, C262, C263, C264, C265, C266, C267, C268, C269, C270, C271, C272, C273, C274, C275, C276, C277, C278, C279, C280, C317, C318, C319, C320, C321, C322, C323, C324, C325, C326, C327, C405, C407, C409, C410, C411, C412: 100nF X5R 10V 0201; CL03A104KP3NNNC; Manufacturer Part CL03A104KP3NNNC; LCSC C49062
C250, C251, C253, C254: 1uF X5R 6.3V 0402; CL05A105KQ5NNNC; Manufacturer Part CL05A105KQ5NNNC; LCSC C107372
R42: 240R 1% 0201; RC0201FR-07240RL; Manufacturer Part RC0201FR-07240RL; LCSC C155745
R63, R64, R72, R76: 49.9R 1% 0201; RC0201FR-0749R9L; Manufacturer Part RC0201FR-0749R9L; LCSC C155744
R65, R66: 10K 0402; RC0402FR-0710KL; Manufacturer Part RC0402FR-0710KL; LCSC C60490
U14: H9HCNNN8KUMLHR-NME; Manufacturer Part H9HCNNN8KUMLHR-NME; LCSC C2912103

Connections:
DDR_CH0_A0_A: U14.H2 (CA0a)
DDR_CH0_A0_B: U14.R2 (CA0b)
DDR_CH0_A1_A: U14.J2 (CA1a)
DDR_CH0_A1_B: U14.P2 (CA1b)
DDR_CH0_A2_A: U14.H9 (CA2a)
DDR_CH0_A2_B: U14.R9 (CA2b)
DDR_CH0_A3_A: U14.H10 (CA3a)
DDR_CH0_A3_B: U14.R10 (CA3b)
DDR_CH0_A4_A: U14.H11 (CA4a)
DDR_CH0_A4_B: U14.R11 (CA4b)
DDR_CH0_A5_A: U14.J11 (CA5a)
DDR_CH0_A5_B: U14.P11 (CA5b)
DDR_CH0_CLKN_A: U14.J9 (CK_ca)
DDR_CH0_CLKN_B: U14.P9 (CK_cb)
DDR_CH0_CLKP_A: U14.J8 (CK_ta)
DDR_CH0_CLKP_B: U14.P8 (CK_tb)
DDR_CH0_DM0_A: U14.C3 (DMI0a)
DDR_CH0_DM0_B: U14.Y3 (DMI0b)
DDR_CH0_DM1_A: U14.C10 (DMI1a)
DDR_CH0_DM1_B: U14.Y10 (DMI1b)
DDR_CH0_DQ0_A: U14.B2 (DQ0a)
DDR_CH0_DQ0_B: U14.AA2 (DQ0b)
DDR_CH0_DQ1_A: U14.C2 (DQ1a)
DDR_CH0_DQ1_B: U14.Y2 (DQ1b)
DDR_CH0_DQ2_A: U14.E2 (DQ2a)
DDR_CH0_DQ2_B: U14.V2 (DQ2b)
DDR_CH0_DQ3_A: U14.F2 (DQ3a)
DDR_CH0_DQ3_B: U14.U2 (DQ3b)
DDR_CH0_DQ4_A: U14.F4 (DQ4a)
DDR_CH0_DQ4_B: U14.U4 (DQ4b)
DDR_CH0_DQ5_A: U14.E4 (DQ5a)
DDR_CH0_DQ5_B: U14.V4 (DQ5b)
DDR_CH0_DQ6_A: U14.C4 (DQ6a)
DDR_CH0_DQ6_B: U14.Y4 (DQ6b)
DDR_CH0_DQ7_A: U14.B4 (DQ7a)
DDR_CH0_DQ7_B: U14.AA4 (DQ7b)
DDR_CH0_DQ8_A: U14.B11 (DQ8a)
DDR_CH0_DQ8_B: U14.AA11 (DQ8b)
DDR_CH0_DQ9_A: U14.C11 (DQ9a)
DDR_CH0_DQ9_B: U14.Y11 (DQ9b)
DDR_CH0_DQ10_A: U14.E11 (DQ10a)
DDR_CH0_DQ10_B: U14.V11 (DQ10b)
DDR_CH0_DQ11_A: U14.F11 (DQ11a)
DDR_CH0_DQ11_B: U14.U11 (DQ11b)
DDR_CH0_DQ12_A: U14.F9 (DQ12a)
DDR_CH0_DQ12_B: U14.U9 (DQ12b)
DDR_CH0_DQ13_A: U14.E9 (DQ13a)
DDR_CH0_DQ13_B: U14.V9 (DQ13b)
DDR_CH0_DQ14_A: U14.C9 (DQ14a)
DDR_CH0_DQ14_B: U14.Y9 (DQ14b)
DDR_CH0_DQ15_A: U14.B9 (DQ15a)
DDR_CH0_DQ15_B: U14.AA9 (DQ15b)
DDR_CH0_DQS0_A_N: U14.E3 (DQS0_ca)
DDR_CH0_DQS0_A_P: U14.D3 (DQS0_ta)
DDR_CH0_DQS0_B_N: U14.V3 (DQS0_cb)
DDR_CH0_DQS0_B_P: U14.W3 (DQS0_tb)
DDR_CH0_DQS1_A_N: U14.E10 (DQS1_ca)
DDR_CH0_DQS1_A_P: U14.D10 (DQS1_ta)
DDR_CH0_DQS1_B_N: U14.V10 (DQS1_cb)
DDR_CH0_DQS1_B_P: U14.W10 (DQS1_tb)
DDR_CH0_LP4/4X_CKE0_A: R63.2, U14.J4 (CKE0a)
DDR_CH0_LP4/4X_CKE0_B: R72.2, U14.P4 (CKE0b)
DDR_CH0_LP4/4X_CKE0/LP5_CS0_A: R63.1
DDR_CH0_LP4/4X_CKE0/LP5_CS0_B: R72.1
DDR_CH0_LP4/4X_CKE1_A: R64.2
DDR_CH0_LP4/4X_CKE1_B: R76.2
DDR_CH0_LP4/4X_CKE1/LP5_CS1_A: R64.1
DDR_CH0_LP4/4X_CKE1/LP5_CS1_B: R76.1
DDR_CH0_LP4/4X_CS0_A: U14.H4 (CS0a)
DDR_CH0_LP4/4X_CS0_B: U14.R4 (CS0b)
DDR_RESET: C239.1, U14.T11 (RESET)
GND: C239.2, C240.1, C241.1, C242.1, C243.1, C244.1, C245.1, C246.1, C247.1, C248.1, C249.1, C250.1, C251.1, C252.1, C253.1, C254.1, C255.1, C256.1, C257.1, C258.1, C260.1, C261.1, C262.1, C263.1, C264.1, C265.1, C266.1, C267.1, C268.1, C269.1, C270.1, C271.1, C272.1, C273.1, C274.1, C275.1, C276.1, C277.1, C278.1, C279.1, C280.1, C317.1, C318.1, C319.1, C320.1, C321.1, C322.1, C323.1, C324.1, C325.1, C326.1, C327.1, C405.1, C407.1, C409.1, C410.1, C411.1, C412.1, U14.A3 (VSS), U14.A10 (VSS), U14.AB3 (VSS), U14.AB5 (VSS), U14.AB8 (VSS), U14.AB10 (VSS), U14.C1 (VSS), U14.C5 (VSS), U14.C8 (VSS), U14.C12 (VSS), U14.D2 (VSS), U14.D4 (VSS), U14.D9 (VSS), U14.D11 (VSS), U14.E1 (VSS), U14.E5 (VSS), U14.E8 (VSS), U14.E12 (VSS), U14.G1 (VSS), U14.G3 (VSS), U14.G5 (VSS), U14.G8 (VSS), U14.G10 (VSS), U14.G12 (VSS), U14.J1 (VSS), U14.J3 (VSS), U14.J10 (VSS), U14.J12 (VSS), U14.K2 (VSS), U14.K4 (VSS), U14.K9 (VSS), U14.K11 (VSS), U14.N2 (VSS), U14.N4 (VSS), U14.N9 (VSS), U14.N11 (VSS), U14.P1 (VSS), U14.P3 (VSS), U14.P10 (VSS), U14.P12 (VSS), U14.T1 (VSS), U14.T3 (VSS), U14.T5 (VSS), U14.T8 (VSS), U14.T10 (VSS), U14.T12 (VSS), U14.V1 (VSS), U14.V5 (VSS), U14.V8 (VSS), U14.V12 (VSS), U14.W2 (VSS), U14.W4 (VSS), U14.W9 (VSS), U14.W11 (VSS), U14.Y1 (VSS), U14.Y5 (VSS), U14.Y8 (VSS), U14.Y12 (VSS)
unnamed: R42.1, U14.A5 (ZQ0)
unnamed: R65.2, U14.G2 (ODTa)
unnamed: R66.1, U14.T2 (ODTb)
VCC1V8_PMU_DDR_S3: C240.2, C243.2, C246.2, C249.2, C252.2, C255.2, C258.2, C261.2, U14.F1 (VDD1), U14.F12 (VDD1), U14.G4 (VDD1), U14.G9 (VDD1), U14.T4 (VDD1), U14.T9 (VDD1), U14.U1 (VDD1), U14.U12 (VDD1)
VDD2_DDR_S3: C242.2, C245.2, C248.2, C251.2, C254.2, C257.2, C260.2, C263.2, C265.2, C267.2, C269.2, C271.2, C273.2, C275.2, C317.2, C320.2, C323.2, C325.2, C326.2, C327.2, C405.2, C407.2, C409.2, C410.2, C411.2, C412.2, R65.1, R66.2, U14.A4 (VDD2), U14.A9 (VDD2), U14.AB4 (VDD2), U14.AB9 (VDD2), U14.F5 (VDD2), U14.F8 (VDD2), U14.H1 (VDD2), U14.H5 (VDD2), U14.H8 (VDD2), U14.H12 (VDD2), U14.K1 (VDD2), U14.K3 (VDD2), U14.K10 (VDD2), U14.K12 (VDD2), U14.N1 (VDD2), U14.N3 (VDD2), U14.N10 (VDD2), U14.N12 (VDD2), U14.R1 (VDD2), U14.R5 (VDD2), U14.R8 (VDD2), U14.R12 (VDD2), U14.U5 (VDD2), U14.U8 (VDD2)
VDDQ_DDR: C241.2, C244.2, C247.2, C250.2, C253.2, C256.2, C262.2, C264.2, C266.2, C268.2, C270.2, C272.2, C274.2, C276.2, C277.2, C278.2, C279.2, C280.2, C318.2, C319.2, C321.2, C322.2, C324.2, R42.2, U14.AA3 (VDDQ), U14.AA5 (VDDQ), U14.AA8 (VDDQ), U14.AA10 (VDDQ), U14.B3 (VDDQ), U14.B5 (VDDQ), U14.B8 (VDDQ), U14.B10 (VDDQ), U14.D1 (VDDQ), U14.D5 (VDDQ), U14.D8 (VDDQ), U14.D12 (VDDQ), U14.F3 (VDDQ), U14.F10 (VDDQ), U14.U3 (VDDQ), U14.U10 (VDDQ), U14.W1 (VDDQ), U14.W5 (VDDQ), U14.W8 (VDDQ), U14.W12 (VDDQ)

Notes on the sheet:
1V1 [1.06V - 1.17V]
REAL VAL X7R
1V8 [1.7V - 1.95V]
RECHECK CAPS
LPDDR4
CROSS CHECK VAL
