CXD8/CXD-ROUTER/Sch/M2_SLOTS-13.kicad_sch

## KiCad design Sch/M2_SLOTS-13.kicad_sch (2026-08-12)

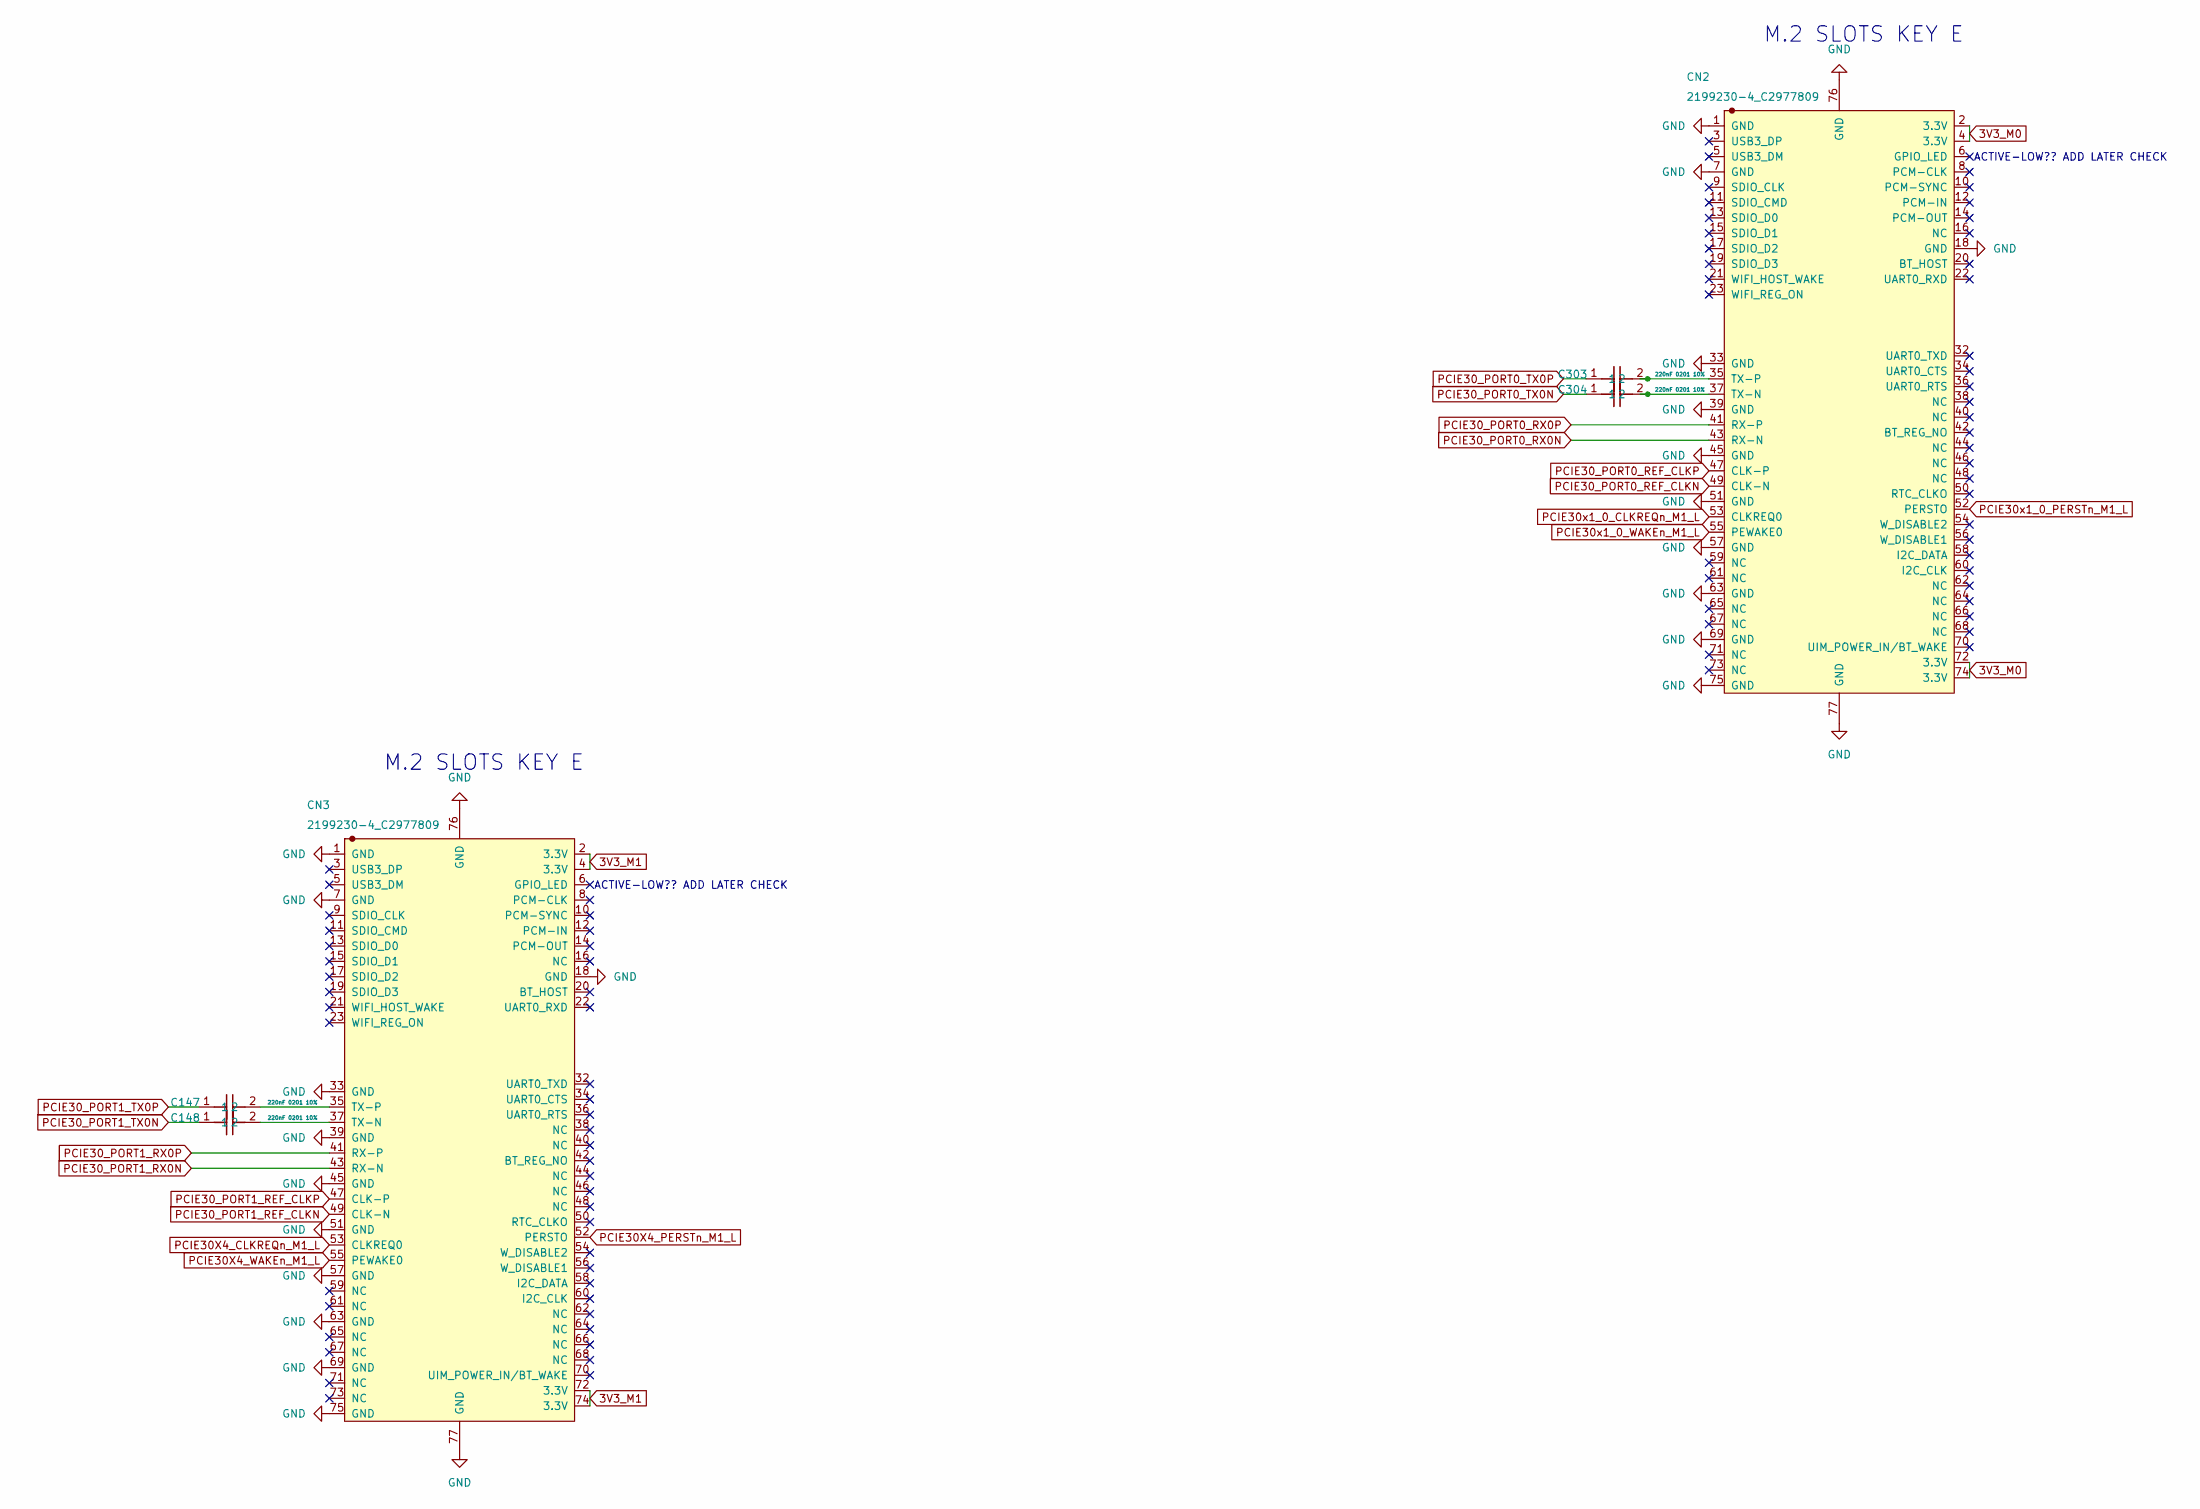
[picture p44: schematic M2_SLOTS-13.kicad_sch]

Parts:
C147, C148, C303, C304: 220nF 0201 10%; RC0201FR-0749R9L; Manufacturer Part GRM033R61E224KE01D; LCSC C701263
CN2, CN3: 2199230-4_C2977809; Manufacturer Part 2199230-4; LCSC C2977809

Connections:
3V3_M0: CN2.2 (3.3V), CN2.4 (3.3V), CN2.72 (3.3V), CN2.74 (3.3V)
3V3_M1: CN3.2 (3.3V), CN3.4 (3.3V), CN3.72 (3.3V), CN3.74 (3.3V)
GND: CN2.1 (GND), CN2.7 (GND), CN2.18 (GND), CN2.33 (GND), CN2.39 (GND), CN2.45 (GND), CN2.51 (GND), CN2.57 (GND), CN2.63 (GND), CN2.69 (GND), CN2.75 (GND), CN2.76 (GND), CN2.77 (GND), CN3.1 (GND), CN3.7 (GND), CN3.18 (GND), CN3.33 (GND), CN3.39 (GND), CN3.45 (GND), CN3.51 (GND), CN3.57 (GND), CN3.63 (GND), CN3.69 (GND), CN3.75 (GND), CN3.76 (GND), CN3.77 (GND)
unnamed: C147.2, CN3.35 (TX-P)
unnamed: C148.2, CN3.37 (TX-N)
unnamed: C303.2, CN2.35 (TX-P)
unnamed: C304.2, CN2.37 (TX-N)
PCIE30X4_CLKREQn_M1_L: CN3.53 (CLKREQ0)
PCIE30X4_PERSTn_M1_L: CN3.52 (PERSTO)
PCIE30X4_WAKEn_M1_L: CN3.55 (PEWAKE0)
PCIE30_PORT0_REF_CLKN: CN2.49 (CLK-N)
PCIE30_PORT0_REF_CLKP: CN2.47 (CLK-P)
PCIE30_PORT0_RX0N: CN2.43 (RX-N)
PCIE30_PORT0_RX0P: CN2.41 (RX-P)
PCIE30_PORT0_TX0N: C304.1
PCIE30_PORT0_TX0P: C303.1
PCIE30_PORT1_REF_CLKN: CN3.49 (CLK-N)
PCIE30_PORT1_REF_CLKP: CN3.47 (CLK-P)
PCIE30_PORT1_RX0N: CN3.43 (RX-N)
PCIE30_PORT1_RX0P: CN3.41 (RX-P)
PCIE30_PORT1_TX0N: C148.1
PCIE30_PORT1_TX0P: C147.1
PCIE30x1_0_CLKREQn_M1_L: CN2.53 (CLKREQ0)
PCIE30x1_0_PERSTn_M1_L: CN2.52 (PERSTO)
PCIE30x1_0_WAKEn_M1_L: CN2.55 (PEWAKE0)

Notes on the sheet:
ACTIVE-LOW?? ADD LATER CHECK
M.2 SLOTS KEY E
