CXD8/CXD-ROUTER/Sch/MIPI_DSI_CSI_INTERFACES-4.kicad_sch

## KiCad design Sch/MIPI_DSI_CSI_INTERFACES-4.kicad_sch (2026-08-12)

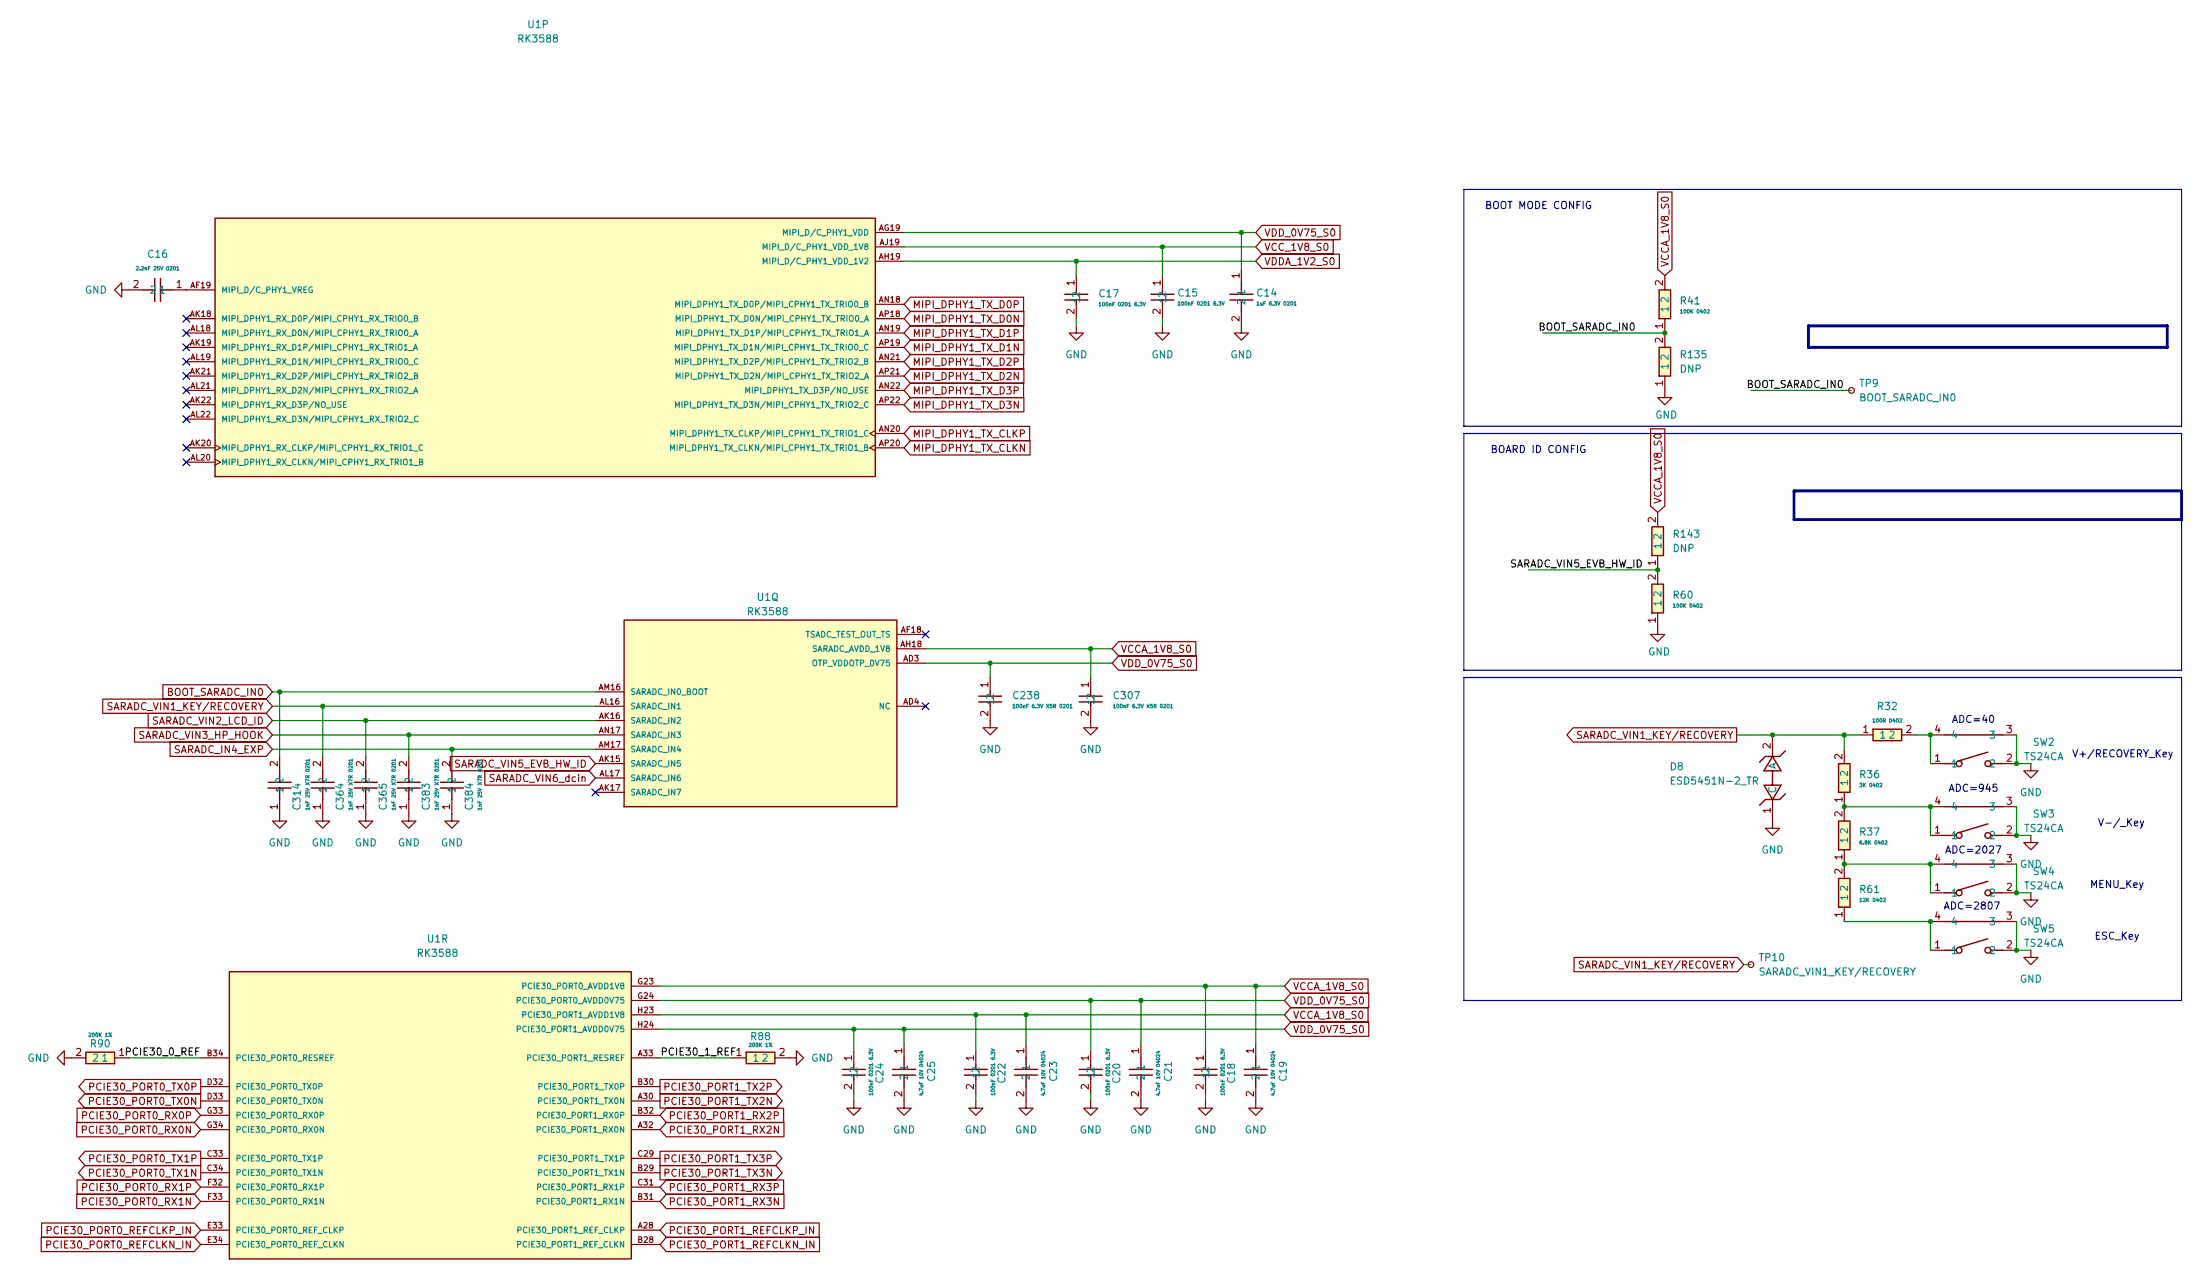
[picture p45: schematic MIPI_DSI_CSI_INTERFACES-4.kicad_sch]

Parts:
C14: 1uF 6.3V 0201; RC0201FR-0749R9L; Manufacturer Part CC0201KRX5R5BB105; LCSC C541330
C15, C17, C18, C20, C22, C24: 100nF 0201 6.3V; RC0201FR-0749R9L; Manufacturer Part CC0201KRX5R5BB104; LCSC C190187
C16: 2.2nF 25V 0201; RC0201FR-0747KL; Manufacturer Part GRM033R71E222KA12D; LCSC C161488
C19, C21, C23, C25: 4.7uF 10V 04024; RC0402JR-070RL; Manufacturer Part CL05A475KP5NRNC; LCSC C368809
C238, C307: 100nF 6.3V X5R 0201; RC0201FR-0749R9L; Manufacturer Part CC0201KRX5R5BB104; LCSC C190187
C314, C364, C365, C383, C384: 1nF 25V X7R 0201; RC0201FR-0749R9L; Manufacturer Part CC0201JRX7R8BB102; LCSC C526941
D8: ESD5451N-2_TR; Manufacturer Part ESD5451N-2/TR; LCSC C239604
R32: 100R 0402; RC0402FR-07100RL; Manufacturer Part RC0402FR-07100RL; LCSC C106232
R36: 3K 0402; RC0402FR-073KL; Manufacturer Part RC0402FR-073KL; LCSC C137987
R37: 6.8K 0402; RC0402FR-076K8L; Manufacturer Part RC0402FR-076K8L; LCSC C93940
R41, R60: 100K 0402; RC0402FR-07100KL; Manufacturer Part RC0402FR-07100KL; LCSC C60491
R61: 12K 0402; RC0402FR-0712KL; Manufacturer Part RC0402FR-0712KL; LCSC C114760
R88, R90: 200K 1%; RC0201FR-07200KL; Manufacturer Part RC0201FR-07200KL; LCSC C138163
R135, R143: DNP; RC0402JR-070RL; Manufacturer Part RC0402JR-070RL; LCSC C60485
SW2, SW3, SW4, SW5: TS24CA; Manufacturer Part TS24CA; LCSC C393942
TP9: BOOT_SARADC_IN0; TestPoint_Pad_1.0x1.0mm
TP10: SARADC_VIN1_KEY/RECOVERY; TestPoint_Pad_1.0x1.0mm
U1: RK3588; BGA1088C65P34X34_2300X2300X204N; PARTREV 1.0

Connections:
BOOT_SARADC_IN0: C314.2, R41.1, R135.2, TP9.1, U1.AM16 (SARADC_IN0_BOOT)
GND: C14.2, C15.2, C16.2, C17.2, C18.2, C19.2, C20.2, C21.2, C22.2, C23.2, C24.2, C25.2, C238.2, C307.2, C314.1, C364.1, C365.1, C383.1, C384.1, D8.1 (C), R60.1, R88.2, R90.2, R135.1, SW2.2, SW2.3, SW3.2, SW3.3, SW4.2, SW4.3, SW5.2, SW5.3
MIPI_DPHY1_TX_CLKN: U1.AP20 (MIPI_DPHY1_TX_CLKN/MIPI_CPHY1_TX_TRIO1_B)
MIPI_DPHY1_TX_CLKP: U1.AN20 (MIPI_DPHY1_TX_CLKP/MIPI_CPHY1_TX_TRIO1_C)
MIPI_DPHY1_TX_D0N: U1.AP18 (MIPI_DPHY1_TX_D0N/MIPI_CPHY1_TX_TRIO0_A)
MIPI_DPHY1_TX_D0P: U1.AN18 (MIPI_DPHY1_TX_D0P/MIPI_CPHY1_TX_TRIO0_B)
MIPI_DPHY1_TX_D1N: U1.AP19 (MIPI_DPHY1_TX_D1N/MIPI_CPHY1_TX_TRIO0_C)
MIPI_DPHY1_TX_D1P: U1.AN19 (MIPI_DPHY1_TX_D1P/MIPI_CPHY1_TX_TRIO1_A)
MIPI_DPHY1_TX_D2N: U1.AP21 (MIPI_DPHY1_TX_D2N/MIPI_CPHY1_TX_TRIO2_A)
MIPI_DPHY1_TX_D2P: U1.AN21 (MIPI_DPHY1_TX_D2P/MIPI_CPHY1_TX_TRIO2_B)
MIPI_DPHY1_TX_D3N: U1.AP22 (MIPI_DPHY1_TX_D3N/MIPI_CPHY1_TX_TRIO2_C)
MIPI_DPHY1_TX_D3P: U1.AN22 (MIPI_DPHY1_TX_D3P/NO_USE)
unnamed: C16.1, U1.AF19 (MIPI_D/C_PHY1_VREG)
unnamed: R32.2, SW2.1, SW2.4
unnamed: R36.1, R37.2, SW3.1, SW3.4
unnamed: R37.1, R61.2, SW4.1, SW4.4
unnamed: R61.1, SW5.1, SW5.4
PCIE30_0_REF: R90.1, U1.B34 (PCIE30_PORT0_RESREF)
PCIE30_1_REF: R88.1, U1.A33 (PCIE30_PORT1_RESREF)
PCIE30_PORT0_REFCLKN_IN: U1.E34 (PCIE30_PORT0_REF_CLKN)
PCIE30_PORT0_REFCLKP_IN: U1.E33 (PCIE30_PORT0_REF_CLKP)
PCIE30_PORT0_RX0N: U1.G34 (PCIE30_PORT0_RX0N)
PCIE30_PORT0_RX0P: U1.G33 (PCIE30_PORT0_RX0P)
PCIE30_PORT0_RX1N: U1.F33 (PCIE30_PORT0_RX1N)
PCIE30_PORT0_RX1P: U1.F32 (PCIE30_PORT0_RX1P)
PCIE30_PORT0_TX0N: U1.D33 (PCIE30_PORT0_TX0N)
PCIE30_PORT0_TX0P: U1.D32 (PCIE30_PORT0_TX0P)
PCIE30_PORT0_TX1N: U1.C34 (PCIE30_PORT0_TX1N)
PCIE30_PORT0_TX1P: U1.C33 (PCIE30_PORT0_TX1P)
PCIE30_PORT1_REFCLKN_IN: U1.B28 (PCIE30_PORT1_REF_CLKN)
PCIE30_PORT1_REFCLKP_IN: U1.A28 (PCIE30_PORT1_REF_CLKP)
PCIE30_PORT1_RX2N: U1.A32 (PCIE30_PORT1_RX0N)
PCIE30_PORT1_RX2P: U1.B32 (PCIE30_PORT1_RX0P)
PCIE30_PORT1_RX3N: U1.B31 (PCIE30_PORT1_RX1N)
PCIE30_PORT1_RX3P: U1.C31 (PCIE30_PORT1_RX1P)
PCIE30_PORT1_TX2N: U1.A30 (PCIE30_PORT1_TX0N)
PCIE30_PORT1_TX2P: U1.B30 (PCIE30_PORT1_TX0P)
PCIE30_PORT1_TX3N: U1.B29 (PCIE30_PORT1_TX1N)
PCIE30_PORT1_TX3P: U1.C29 (PCIE30_PORT1_TX1P)
SARADC_IN4_EXP: C384.2, U1.AM17 (SARADC_IN4)
SARADC_VIN1_KEY/RECOVERY: C364.2, D8.2 (A), R32.1, R36.2, TP10.1, U1.AL16 (SARADC_IN1)
SARADC_VIN2_LCD_ID: C365.2, U1.AK16 (SARADC_IN2)
SARADC_VIN3_HP_HOOK: C383.2, U1.AN17 (SARADC_IN3)
SARADC_VIN5_EVB_HW_ID: R60.2, R143.1, U1.AK15 (SARADC_IN5)
SARADC_VIN6_dcin: U1.AL17 (SARADC_IN6)
VCCA_1V8_S0: C18.1, C19.1, C22.1, C23.1, C307.1, R41.2, R143.2, U1.AH18 (SARADC_AVDD_1V8), U1.G23 (PCIE30_PORT0_AVDD1V8), U1.H23 (PCIE30_PORT1_AVDD1V8)
VCC_1V8_S0: C15.1, U1.AJ19 (MIPI_D/C_PHY1_VDD_1V8)
VDDA_1V2_S0: C17.1, U1.AH19 (MIPI_D/C_PHY1_VDD_1V2)
VDD_0V75_S0: C14.1, C20.1, C21.1, C24.1, C25.1, C238.1, U1.AD3 (OTP_VDDOTP_0V75), U1.AG19 (MIPI_D/C_PHY1_VDD), U1.G24 (PCIE30_PORT0_AVDD0V75), U1.H24 (PCIE30_PORT1_AVDD0V75)

Notes on the sheet:
ADC=2027
ADC=2807
ADC=945
V-/_Key
ADC=40
V+/RECOVERY_Key
MENU_Key
ESC_Key
BOARD ID CONFIG
BOOT MODE CONFIG
