CXD8/CXD-ROUTER/Sch/PCIE_SATA_USB_INTERFACES-5.kicad_sch

## KiCad design Sch/PCIE_SATA_USB_INTERFACES-5.kicad_sch (2026-08-12)

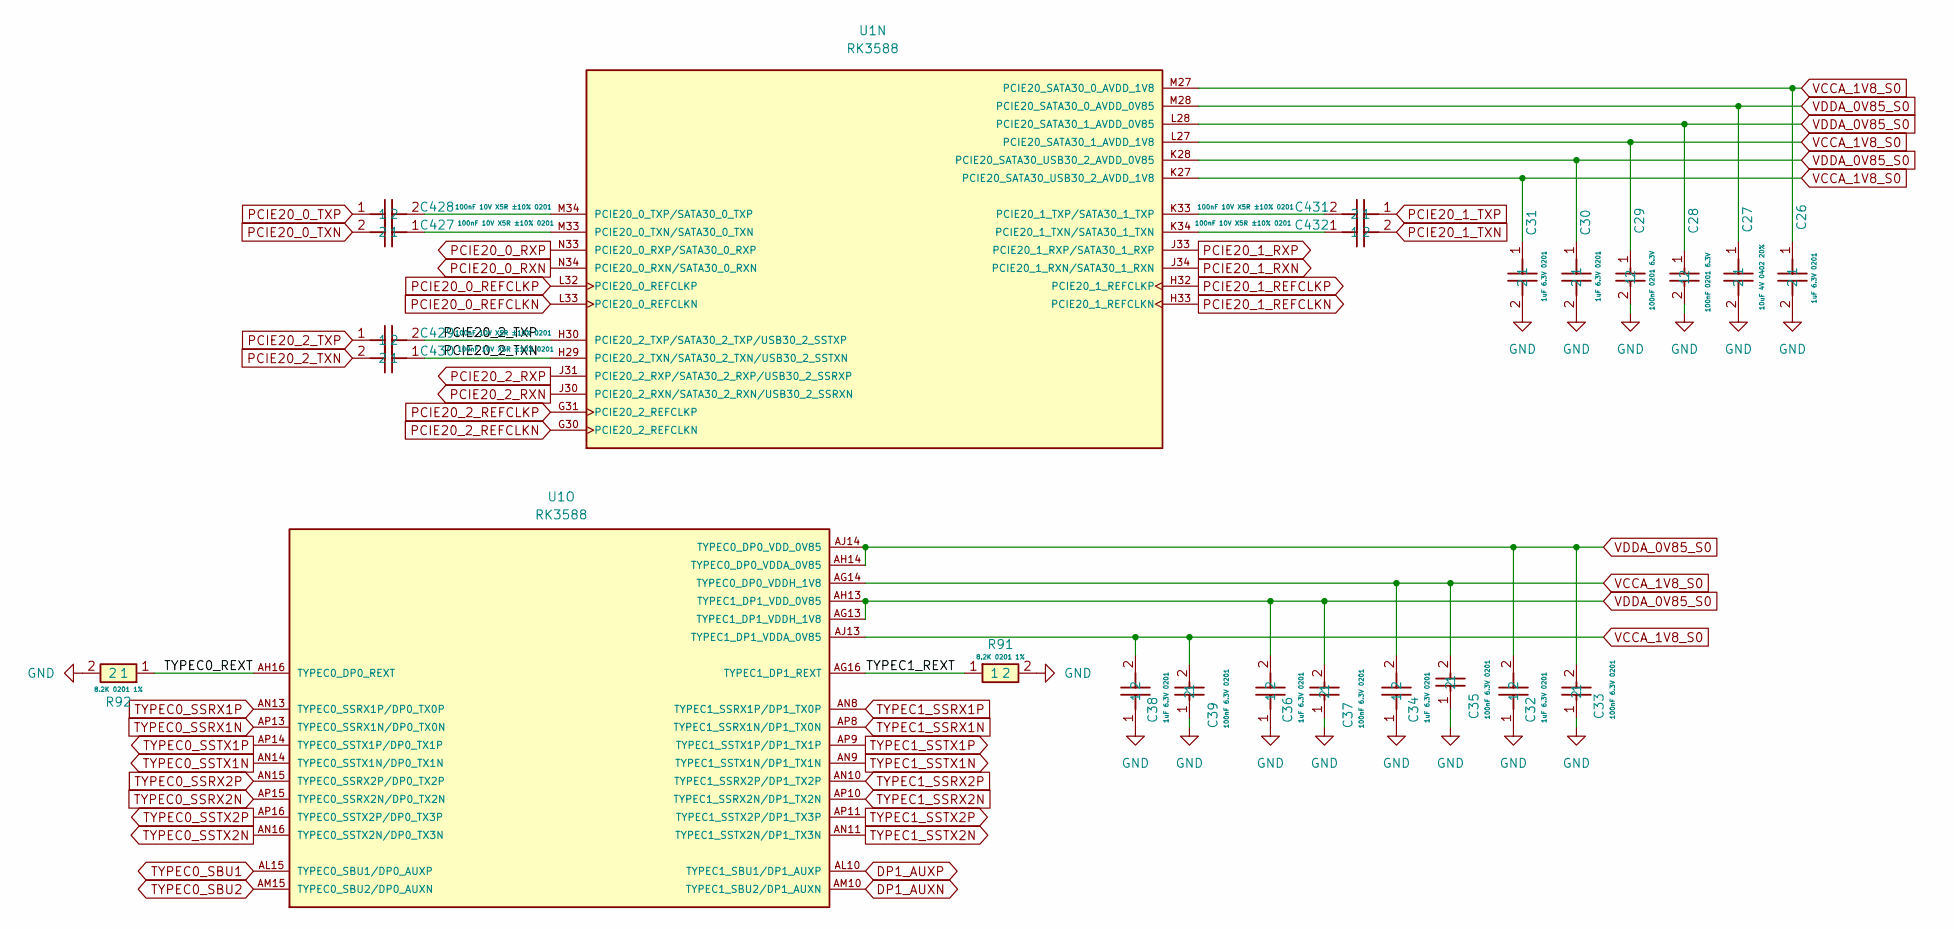
[picture p46: schematic PCIE_SATA_USB_INTERFACES-5.kicad_sch]

Parts:
C26, C30, C31, C32, C34, C36, C38: 1uF 6.3V 0201; RC0201FR-0749R9L; Manufacturer Part CC0201KRX5R5BB105; LCSC C541330
C27: 10uF 4V 0402 20%; RC0402JR-070RL; Manufacturer Part CL05A106MP5NUNC; LCSC C315248
C28, C29: 100nF 0201 6.3V; RC0201FR-0749R9L; Manufacturer Part CC0201KRX5R5BB104; LCSC C190187
C33, C35, C37, C39: 100nF 6.3V 0201; RC0201FR-0749R9L; Manufacturer Part CC0201KRX5R5BB104; LCSC C190187
C427, C428, C429, C430, C431, C432: 100nF 10V X5R ±10% 0201; CL03A104KP3NNNC; Manufacturer Part CL03A104KP3NNNC; LCSC C49062
R91, R92: 8.2K 0201 1%; 0201WMF8201TEE; Manufacturer Part 0201WMF8201TEE; LCSC C473470
U1: RK3588; BGA1088C65P34X34_2300X2300X204N; PARTREV 1.0

Connections:
DP1_AUXN: U1.AM10 (TYPEC1_SBU2/DP1_AUXN)
DP1_AUXP: U1.AL10 (TYPEC1_SBU1/DP1_AUXP)
GND: C26.2, C27.2, C28.2, C29.2, C30.2, C31.2, C32.1, C33.1, C34.1, C35.1, C36.1, C37.1, C38.1, C39.1, R91.2, R92.2
unnamed: C427.1, U1.M33 (PCIE20_0_TXN/SATA30_0_TXN)
unnamed: C428.2, U1.M34 (PCIE20_0_TXP/SATA30_0_TXP)
unnamed: C431.2, U1.K33 (PCIE20_1_TXP/SATA30_1_TXP)
unnamed: C432.1, U1.K34 (PCIE20_1_TXN/SATA30_1_TXN)
PCIE20_0_REFCLKN: U1.L33 (PCIE20_0_REFCLKN)
PCIE20_0_REFCLKP: U1.L32 (PCIE20_0_REFCLKP)
PCIE20_0_RXN: U1.N34 (PCIE20_0_RXN/SATA30_0_RXN)
PCIE20_0_RXP: U1.N33 (PCIE20_0_RXP/SATA30_0_RXP)
PCIE20_0_TXN: C427.2
PCIE20_0_TXP: C428.1
PCIE20_1_REFCLKN: U1.H33 (PCIE20_1_REFCLKN)
PCIE20_1_REFCLKP: U1.H32 (PCIE20_1_REFCLKP)
PCIE20_1_RXN: U1.J34 (PCIE20_1_RXN/SATA30_1_RXN)
PCIE20_1_RXP: U1.J33 (PCIE20_1_RXP/SATA30_1_RXP)
PCIE20_1_TXN: C432.2
PCIE20_1_TXP: C431.1
PCIE20_2_REFCLKN: U1.G30 (PCIE20_2_REFCLKN)
PCIE20_2_REFCLKP: U1.G31 (PCIE20_2_REFCLKP)
PCIE20_2_RXN: U1.J30 (PCIE20_2_RXN/SATA30_2_RXN/USB30_2_SSRXN)
PCIE20_2_RXP: U1.J31 (PCIE20_2_RXP/SATA30_2_RXP/USB30_2_SSRXP)
PCIE20_2_TXN: C430.1, C430.2, U1.H29 (PCIE20_2_TXN/SATA30_2_TXN/USB30_2_SSTXN)
PCIE20_2_TXP: C429.1, C429.2, U1.H30 (PCIE20_2_TXP/SATA30_2_TXP/USB30_2_SSTXP)
TYPEC0_REXT: R92.1, U1.AH16 (TYPEC0_DP0_REXT)
TYPEC0_SBU1: U1.AL15 (TYPEC0_SBU1/DP0_AUXP)
TYPEC0_SBU2: U1.AM15 (TYPEC0_SBU2/DP0_AUXN)
TYPEC0_SSRX1N: U1.AP13 (TYPEC0_SSRX1N/DP0_TX0N)
TYPEC0_SSRX1P: U1.AN13 (TYPEC0_SSRX1P/DP0_TX0P)
TYPEC0_SSRX2N: U1.AP15 (TYPEC0_SSRX2N/DP0_TX2N)
TYPEC0_SSRX2P: U1.AN15 (TYPEC0_SSRX2P/DP0_TX2P)
TYPEC0_SSTX1N: U1.AN14 (TYPEC0_SSTX1N/DP0_TX1N)
TYPEC0_SSTX1P: U1.AP14 (TYPEC0_SSTX1P/DP0_TX1P)
TYPEC0_SSTX2N: U1.AN16 (TYPEC0_SSTX2N/DP0_TX3N)
TYPEC0_SSTX2P: U1.AP16 (TYPEC0_SSTX2P/DP0_TX3P)
TYPEC1_REXT: R91.1, U1.AG16 (TYPEC1_DP1_REXT)
TYPEC1_SSRX1N: U1.AP8 (TYPEC1_SSRX1N/DP1_TX0N)
TYPEC1_SSRX1P: U1.AN8 (TYPEC1_SSRX1P/DP1_TX0P)
TYPEC1_SSRX2N: U1.AP10 (TYPEC1_SSRX2N/DP1_TX2N)
TYPEC1_SSRX2P: U1.AN10 (TYPEC1_SSRX2P/DP1_TX2P)
TYPEC1_SSTX1N: U1.AN9 (TYPEC1_SSTX1N/DP1_TX1N)
TYPEC1_SSTX1P: U1.AP9 (TYPEC1_SSTX1P/DP1_TX1P)
TYPEC1_SSTX2N: U1.AN11 (TYPEC1_SSTX2N/DP1_TX3N)
TYPEC1_SSTX2P: U1.AP11 (TYPEC1_SSTX2P/DP1_TX3P)
VCCA_1V8_S0: C26.1, C29.1, C31.1, C34.2, C35.2, C38.2, C39.2, U1.AG14 (TYPEC0_DP0_VDDH_1V8), U1.AJ13 (TYPEC1_DP1_VDDA_0V85), U1.K27 (PCIE20_SATA30_USB30_2_AVDD_1V8), U1.L27 (PCIE20_SATA30_1_AVDD_1V8), U1.M27 (PCIE20_SATA30_0_AVDD_1V8)
VDDA_0V85_S0: C27.1, C28.1, C30.1, C32.2, C33.2, C36.2, C37.2, U1.AG13 (TYPEC1_DP1_VDDH_1V8), U1.AH13 (TYPEC1_DP1_VDD_0V85), U1.AH14 (TYPEC0_DP0_VDDA_0V85), U1.AJ14 (TYPEC0_DP0_VDD_0V85), U1.K28 (PCIE20_SATA30_USB30_2_AVDD_0V85), U1.L28 (PCIE20_SATA30_1_AVDD_0V85), U1.M28 (PCIE20_SATA30_0_AVDD_0V85)
