CXD8/CXD-ROUTER/Sch/PMIC-14.kicad_sch

## KiCad design Sch/PMIC-14.kicad_sch (2026-08-12)

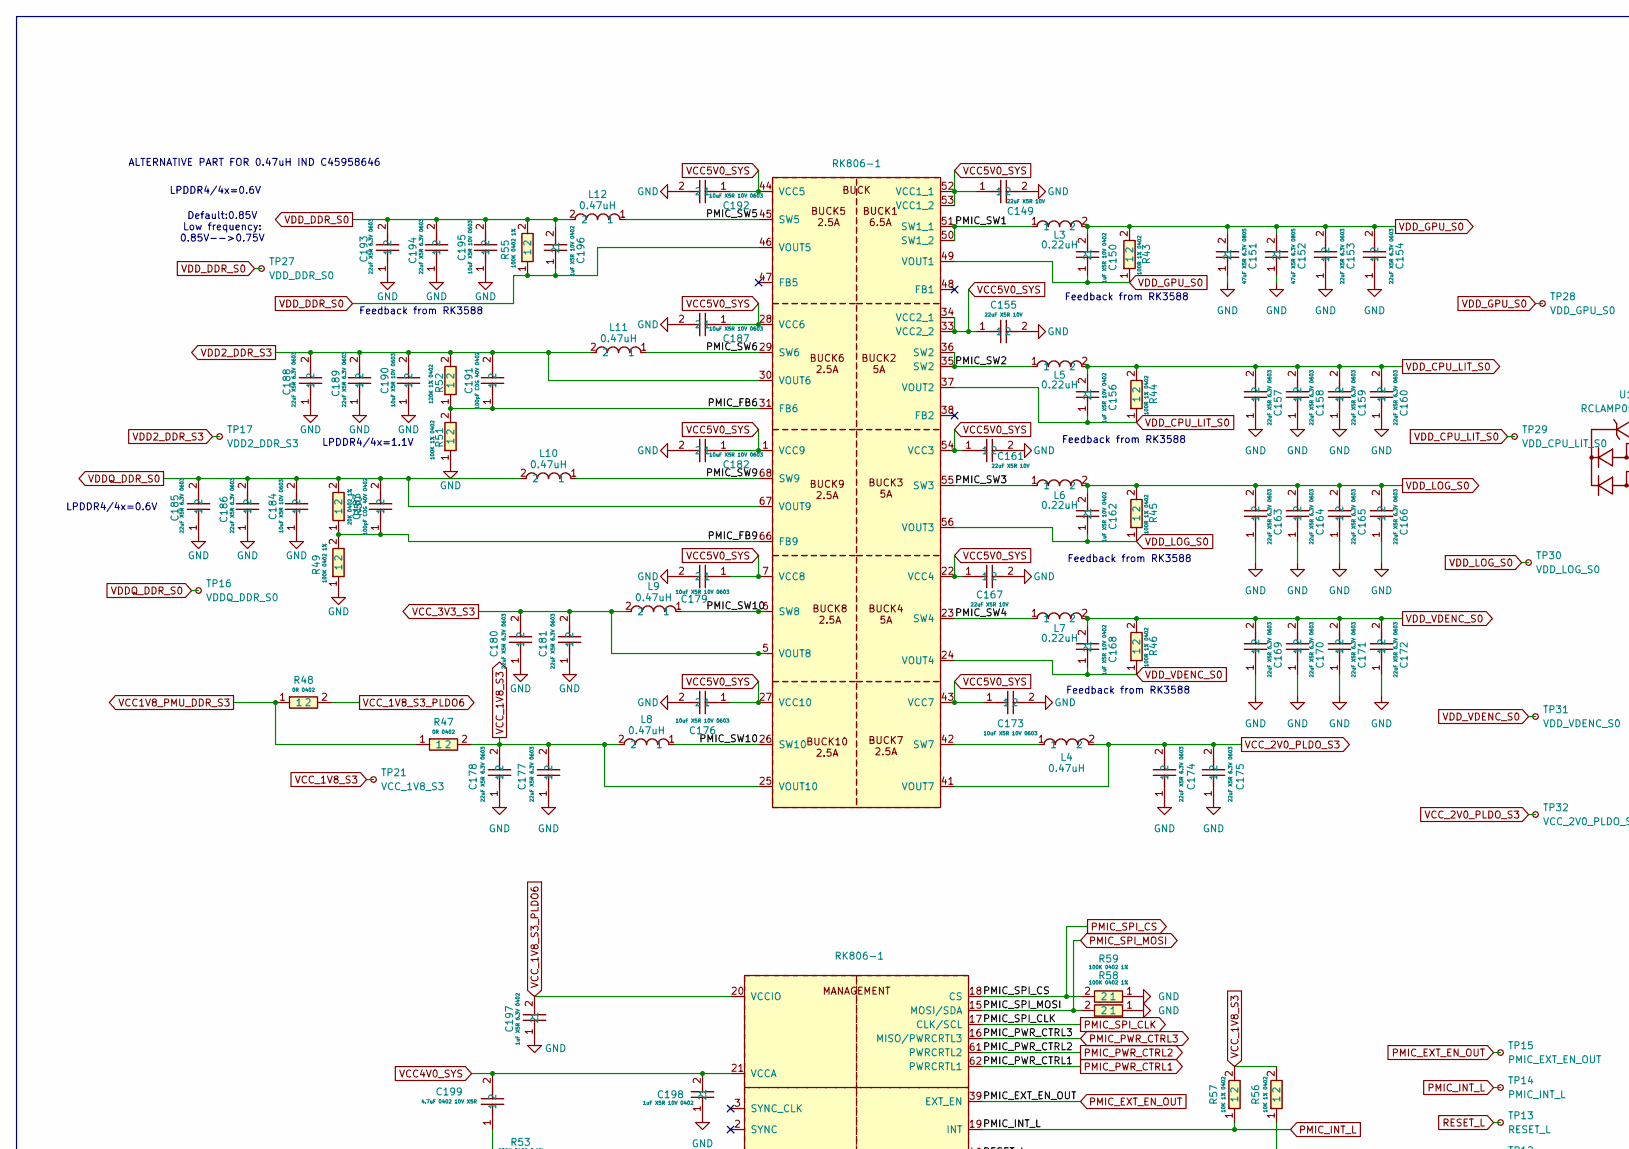
[picture p47: schematic PMIC-14.kicad_sch, part in row 1, column 1]

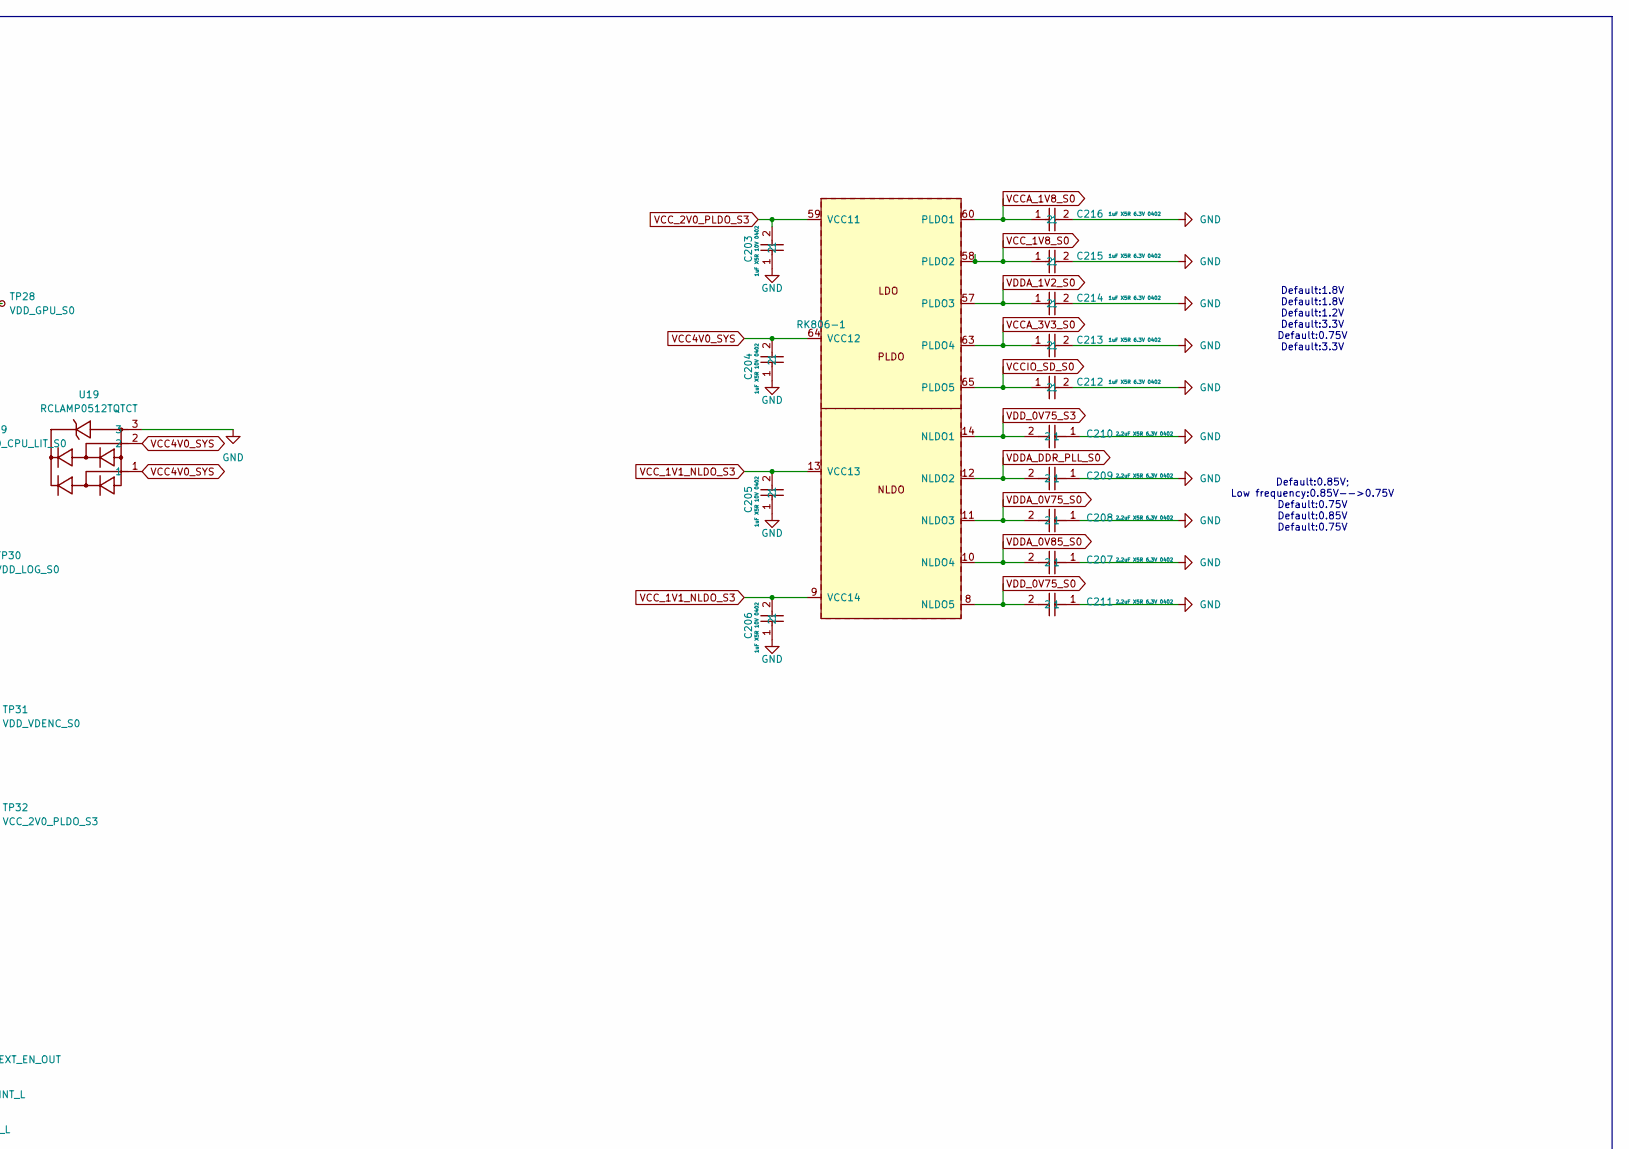
[picture p48: schematic PMIC-14.kicad_sch, part in row 1, column 2]

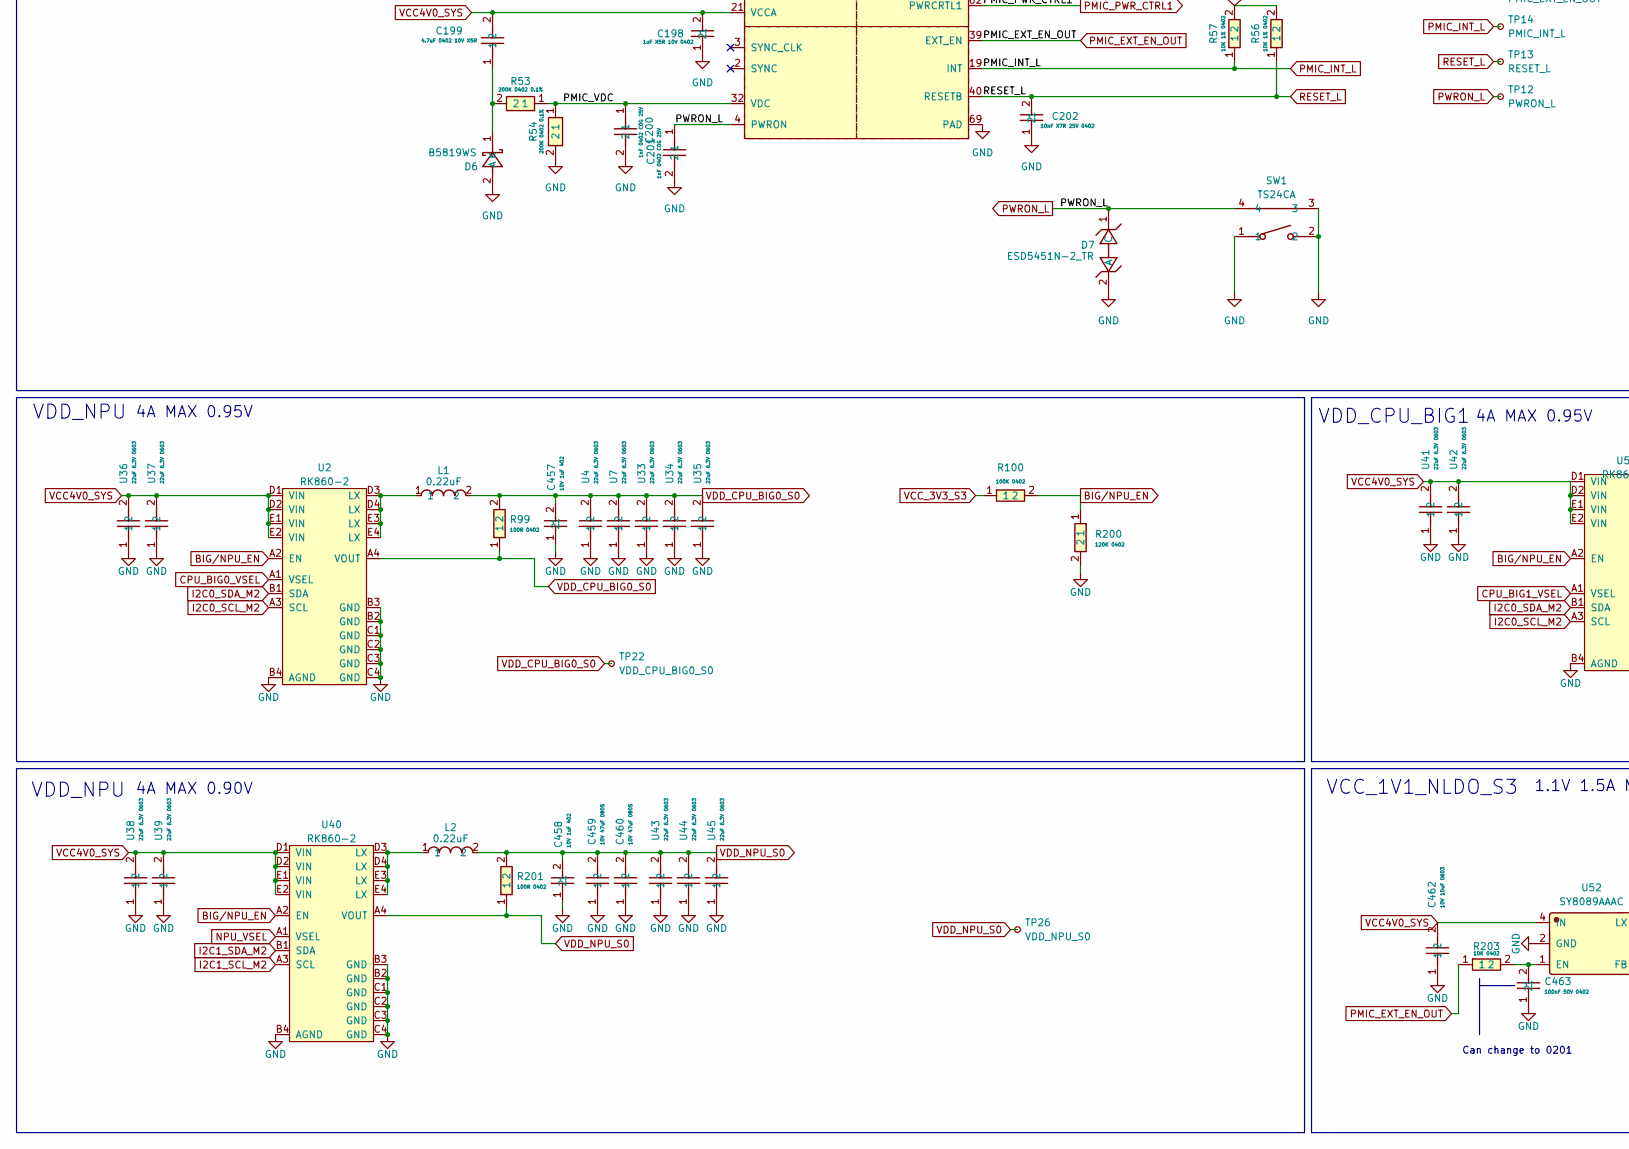
[picture p49: schematic PMIC-14.kicad_sch, part in row 2, column 1]

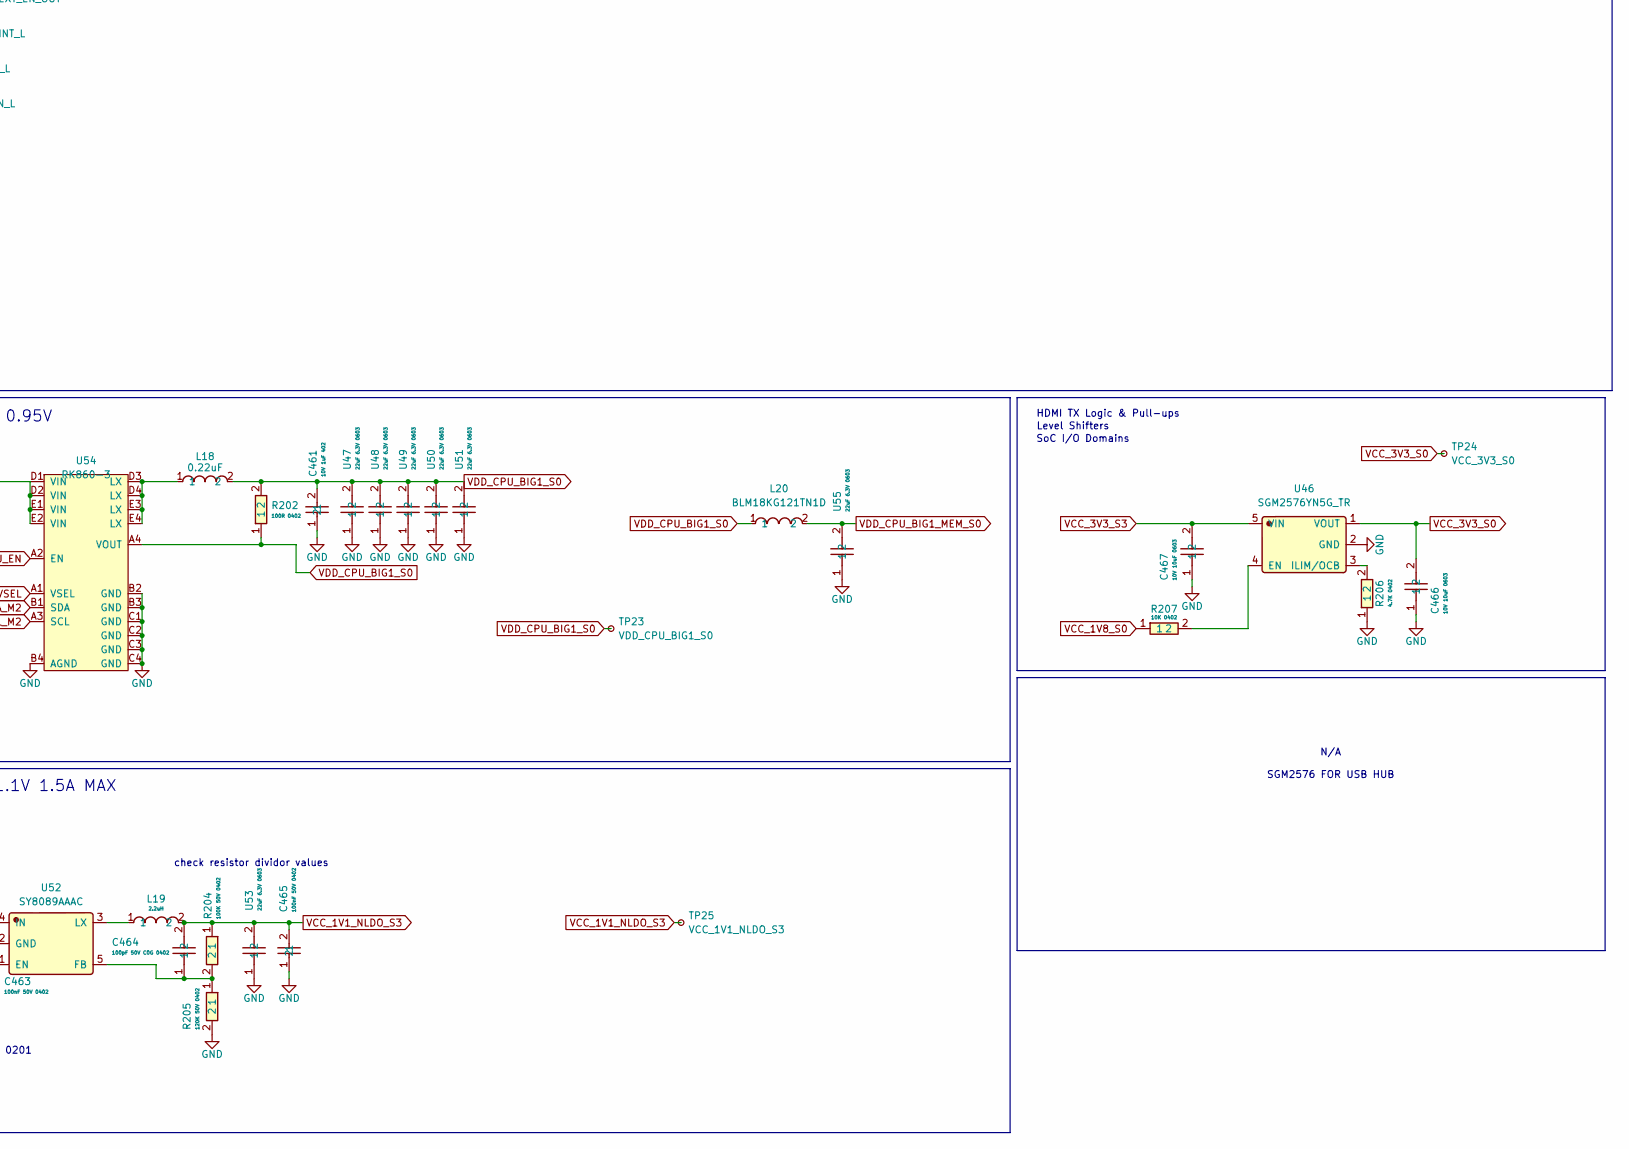
[picture p50: schematic PMIC-14.kicad_sch, part in row 2, column 2]

Parts:
C149, C155, C161, C167: 22uF X5R 10V; RC0402JR-070RL; Manufacturer Part GRM158R61A226ME15D; LCSC C3845593
C150, C156, C162, C168, C196, C198, C203, C204, C205, C206: 1uF X5R 10V 0402; FRC0402F1693TS; Manufacturer Part CL05A105KP5NNNC; LCSC C14445
C151, C152: 47uF X5R 6.3V 0805; CL21A476MQYNNNE; Manufacturer Part CL21A476MQYNNNE; LCSC C16780
C153, C154, C157, C158, C159, C160, C163, C164, C165, C166, C169, C170, C171, C172, C174, C175, C177, C178, C180, C181, C185, C186, C188, C189, C193, C194: 22uF X5R 6.3V 0603; CL10A226MQ8NRNC; Manufacturer Part CL10A226MQ8NRNC; LCSC C59461
C173, C176, C179, C182, C184, C187, C190, C192, C195: 10uF X5R 10V 0603; CL10A106KP8NNNC; Manufacturer Part CL10A106KP8NNNC; LCSC C19702
C183, C191: 100pF C0G 40V 0402; FRC0402F1693TS; Manufacturer Part GCM1555C1H101FA16D; LCSC C2941926
C197: 1uF X5R 6.3V 0402; CL05A105KQ5NNNC; Manufacturer Part CL05A105KQ5NNNC; LCSC C107372
C199: 4.7uF 0402 10V X5R; FRC0402F1693TS; Manufacturer Part CC0402MRX5R6BB475; LCSC C469468
C200, C201: 1nF 0402 C0G 25V; FRC0402F1693TS; Manufacturer Part CC0402JRNPO8BN102; LCSC C526995
C202: 10nF X7R 25V 0402; FRC0402F1693TS; Manufacturer Part CL05B103KB5NNNC; LCSC C15195
C207, C208, C209, C210, C211: 2.2uF X5R 6.3V 0402; FRC0402F1693TS; Manufacturer Part CL05A225KO5NQNC; LCSC C170151
C212, C213, C214, C215, C216: 1uF X5R 6.3V 0402; FRC0402F1693TS; Manufacturer Part CL05A105KP5NNNC; LCSC C14445
C457, C458, C461: 10V 1uF 402; FRC0402F1693TS; Manufacturer Part CL05A105KP5NNNC; LCSC C14445
C459, C460: 10V 47uF 0805; GRM21BR61A476ME15L; Manufacturer Part GRM21BR61A476ME15L; LCSC C124129
C462, C466, C467: 10V 10uF 0603; CL10A106KP8NNNC; Manufacturer Part CL10A106KP8NNNC; LCSC C19702
C463, C465: 100nF 50V 0402; RC0402JR-070RL; Manufacturer Part CC0402KRX5R9BB104; LCSC C105882
C464: 100pF 50V C0G 0402; FRC0402F1693TS; Manufacturer Part GCM1555C1H101FA16D; LCSC C2941926
D6: B5819WS; B5819WS_C916992; Manufacturer Part B5819WS; LCSC C916992
D7: ESD5451N-2_TR; Manufacturer Part ESD5451N-2/TR; LCSC C239604
L1, L2, L18: 0.22uF; FTC322512SR22MBCA; Manufacturer Part FTC322512SR22MBCA; LCSC C5832378
L3, L5, L6, L7: 0.22uH; APS252012MR22F; Manufacturer Part APS252012MR22F; LCSC C47327420
L4, L8, L9, L10, L11, L12: 0.47uH; MTC201208-R47MT; Manufacturer Part MTC201208-R47MT; LCSC C7588889
L19: 2.2uH; FTC303020D2R2MBCA; Manufacturer Part FTC303020D2R2MBCA; LCSC C7423318
L20: BLM18KG121TN1D; Manufacturer Part BLM18KG121TN1D; LCSC C85831
R43, R44, R45, R46: 100R 1% 0402; RC0402FR-07100KL; Manufacturer Part RC0402FR-07100KL; LCSC C60491
R47, R48: 0R 0402; RC0402JR-070RL; Manufacturer Part RC0402JR-070RL; LCSC C60485
R49, R55, R58, R59: 100K 0402 1%; RC0402FR-07100KL; Manufacturer Part RC0402FR-07100KL; LCSC C60491
R50: 20K 0402 1%; RC0402FR-0720KL; Manufacturer Part RC0402FR-0720KL; LCSC C93942
R51: 100K 1% 0402; RC0402FR-07100KL; Manufacturer Part RC0402FR-07100KL; LCSC C60491
R52: 120K 1% 0402; RC0402FR-07120KL; Manufacturer Part RC0402FR-07120KL; LCSC C93945
R53, R54: 200K 0402 0.1%; RT0402BRD07200KL; Manufacturer Part RT0402BRD07200KL; LCSC C728556
R56, R57: 10K 1% 0402; RC0402FR-0710KL; Manufacturer Part RC0402FR-0710KL; LCSC C60490
R99, R201, R202: 100R 0402; RC0402FR-07100RL; Manufacturer Part RC0402FR-07100RL; LCSC C106232
R100: 100K 0402; RC0402FR-07100KL; Manufacturer Part RC0402FR-07100KL; LCSC C60491
R200: 120K 0402; RC0402FR-07120KL; Manufacturer Part RC0402FR-07120KL; LCSC C93945
R203, R207: 10K 0402; RC0402FR-0710KL; Manufacturer Part RC0402FR-0710KL; LCSC C60490
R204: 100K 50V 0402; RC0402FR-07100KL; Manufacturer Part RC0402FR-07100KL; LCSC C60491
R205: 120K 50V 0402; RC0402FR-07120KL; Manufacturer Part RC0402FR-07120KL; LCSC C93945
R206: 4.7K 0402; RC0402FR-074K7L; Manufacturer Part RC0402FR-074K7L; LCSC C105871
SW1: TS24CA; Manufacturer Part TS24CA; LCSC C393942
TP12: PWRON_L; TestPoint_Pad_1.0x1.0mm
TP13: RESET_L; TestPoint_Pad_1.0x1.0mm
TP14: PMIC_INT_L; TestPoint_Pad_1.0x1.0mm
TP15: PMIC_EXT_EN_OUT; TestPoint_Pad_1.0x1.0mm
TP16: VDDQ_DDR_S0; TestPoint_Pad_1.0x1.0mm
TP17: VDD2_DDR_S3; TestPoint_Pad_1.0x1.0mm
TP21: VCC_1V8_S3; TestPoint_Pad_1.0x1.0mm
TP22: VDD_CPU_BIG0_S0; TestPoint_Pad_1.0x1.0mm
TP23: VDD_CPU_BIG1_S0; TestPoint_Pad_1.0x1.0mm
TP24: VCC_3V3_S0; TestPoint_Pad_1.0x1.0mm
TP25: VCC_1V1_NLDO_S3; TestPoint_Pad_1.0x1.0mm
TP26: VDD_NPU_S0; TestPoint_Pad_1.0x1.0mm
TP27: VDD_DDR_S0; TestPoint_Pad_1.0x1.0mm
TP28: VDD_GPU_S0; TestPoint_Pad_1.0x1.0mm
TP29: VDD_CPU_LIT_S0; TestPoint_Pad_1.0x1.0mm
TP30: VDD_LOG_S0; TestPoint_Pad_1.0x1.0mm
TP31: VDD_VDENC_S0; TestPoint_Pad_1.0x1.0mm
TP32: VCC_2V0_PLDO_S3; TestPoint_Pad_1.0x1.0mm
U2, U40: RK860-2; Manufacturer Part RK860-2; LCSC C5156489
U4, U7, U33, U34, U35, U36, U37, U38, U39, U41, U42, U43, U44, U45, U47, U48, U49, U50, U51, U53, U55: 22uF 6.3V 0603; GRM188R60J226KEA0D; Manufacturer Part GRM188R60J226KEA0D; LCSC C3020456
U18: RK806-1; QFN35P700X700X90-69N; Manufacturer Part RK806-1
U19: RCLAMP0512TQTCT; Manufacturer Part RCLAMP0512TQTCT; LCSC C512369
U46: SGM2576YN5G_TR; Manufacturer Part SGM2576YN5G/TR; LCSC C699888
U52: SY8089AAAC; Manufacturer Part SY8089AAAC; LCSC C78988
U54: RK860-3; Manufacturer Part RK860-3; LCSC C5156487

Connections:
BIG/NPU_EN: R100.2, R200.1, U2.A2 (EN), U40.A2 (EN), U54.A2 (EN)
CPU_BIG0_VSEL: U2.A1 (VSEL)
CPU_BIG1_VSEL: U54.A1 (VSEL)
GND: C149.2, C151.1, C152.1, C153.1, C154.1, C155.2, C157.1, C158.1, C159.1, C160.1, C161.2, C163.1, C164.1, C165.1, C166.1, C167.2, C169.1, C170.1, C171.1, C172.1, C173.2, C174.1, C175.1, C176.2, C177.1, C178.1, C179.2, C180.1, C181.1, C182.2, C184.1, C185.1, C186.1, C187.2, C188.1, C189.1, C190.1, C192.2, C193.1, C194.1, C195.1, C197.1, C198.1, C200.2, C201.2, C202.1, C203.1, C204.1, C205.1, C206.1, C207.1, C208.1, C209.1, C210.1, C211.1, C212.2, C213.2, C214.2, C215.2, C216.2, C457.1, C458.1, C459.1, C460.1, C461.1, C462.1, C463.1, C465.1, C466.1, C467.1, D6.2 (A), D7.2 (A), R49.1, R51.1, R54.2, R58.1, R59.1, R200.2, R205.2, R206.1, SW1.1, SW1.2, SW1.3, U2.B2 (GND), U2.B3 (GND), U2.B4 (AGND), U2.C1 (GND), U2.C2 (GND), U2.C3 (GND), U2.C4 (GND), U4.1, U7.1, U18.69 (PAD), U19.3, U33.1, U34.1, U35.1, U36.1, U37.1, U38.1, U39.1, U40.B2 (GND), U40.B3 (GND), U40.B4 (AGND), U40.C1 (GND), U40.C2 (GND), U40.C3 (GND), U40.C4 (GND), U41.1, U42.1, U43.1, U44.1, U45.1, U46.2 (GND), U47.1, U48.1, U49.1, U50.1, U51.1, U52.2 (GND), U53.1, U54.B2 (GND), U54.B3 (GND), U54.B4 (AGND), U54.C1 (GND), U54.C2 (GND), U54.C3 (GND), U54.C4 (GND), U55.1
I2C0_SCL_M2: U2.A3 (SCL), U54.A3 (SCL)
I2C0_SDA_M2: U2.B1 (SDA), U54.B1 (SDA)
I2C1_SCL_M2: U40.A3 (SCL)
I2C1_SDA_M2: U40.B1 (SDA)
NPU_VSEL: U40.A1 (VSEL)
unnamed: C199.1, D6.1 (K), R53.2
unnamed: C463.2, R203.2, U52.1 (EN)
unnamed: C464.1, R204.2, R205.1, U52.5 (FB)
unnamed: L1.1, U2.D3 (LX), U2.D4 (LX), U2.E3 (LX), U2.E4 (LX)
unnamed: L2.1, U40.D3 (LX), U40.D4 (LX), U40.E3 (LX), U40.E4 (LX)
unnamed: L4.1, U18.42 (SW7)
unnamed: L18.1, U54.D3 (LX), U54.D4 (LX), U54.E3 (LX), U54.E4 (LX)
unnamed: L19.1, U52.3 (LX)
unnamed: R206.2, U46.3 (ILIM/OCB)
unnamed: R207.2, U46.4 (EN)
PMIC_EXT_EN_OUT: R203.1, TP15.1, U18.39 (EXT_EN)
PMIC_FB6: C191.1, R51.2, R52.1, U18.31 (FB6)
PMIC_FB9: C183.1, R49.2, R50.1, U18.66 (FB9)
PMIC_INT_L: R57.1, TP14.1, U18.19 (INT)
PMIC_PWR_CTRL1: U18.62 (PWRCRTL1)
PMIC_PWR_CTRL2: U18.61 (PWRCRTL2)
PMIC_PWR_CTRL3: U18.16 (MISO/PWRCRTL3)
PMIC_SPI_CLK: U18.17 (CLK/SCL)
PMIC_SPI_CS: R59.2, U18.18 (CS)
PMIC_SPI_MOSI: R58.2, U18.15 (MOSI/SDA)
PMIC_SW1: L3.1, U18.50 (SW1_2), U18.51 (SW1_1)
PMIC_SW2: L5.1, U18.35 (SW2), U18.36 (SW2)
PMIC_SW3: L6.1, U18.55 (SW3)
PMIC_SW4: L7.1, U18.23 (SW4)
PMIC_SW5: L12.1, U18.45 (SW5)
PMIC_SW6: L11.1, U18.29 (SW6)
PMIC_SW9: L10.1, U18.68 (SW9)
PMIC_SW10: L8.1, L9.1, U18.6 (SW8), U18.26 (SW10)
PMIC_VDC: C200.1, R53.1, R54.1, U18.32 (VDC)
PWRON_L: C201.1, D7.1 (C), SW1.4, TP12.1, U18.4 (PWRON)
RESET_L: C202.2, R56.1, TP13.1, U18.40 (RESETB)
VCC1V8_PMU_DDR_S3: R47.1, R48.1
VCC4V0_SYS: C198.2, C199.2, C204.2, C462.2, U2.D1 (VIN), U2.D2 (VIN), U2.E1 (VIN), U2.E2 (VIN), U18.21 (VCCA), U18.64 (VCC12), U19.1, U19.2, U36.2, U37.2, U38.2, U39.2, U40.D1 (VIN), U40.D2 (VIN), U40.E1 (VIN), U40.E2 (VIN), U41.2, U42.2, U52.4 (IN), U54.D1 (VIN), U54.D2 (VIN), U54.E1 (VIN), U54.E2 (VIN)
VCC5V0_SYS: C149.1, C155.1, C161.1, C167.1, C173.1, C176.1, C179.1, C182.1, C187.1, C192.1, U18.1 (VCC9), U18.7 (VCC8), U18.22 (VCC4), U18.27 (VCC10), U18.28 (VCC6), U18.33 (VCC2_2), U18.34 (VCC2_1), U18.43 (VCC7), U18.44 (VCC5), U18.52 (VCC1_1), U18.53 (VCC1_2), U18.54 (VCC3)
VCCA_1V8_S0: C216.1, U18.60 (PLDO1)
VCCA_3V3_S0: C213.1, U18.63 (PLDO4)
VCCIO_SD_S0: C212.1, U18.65 (PLDO5)
VCC_1V1_NLDO_S3: C205.2, C206.2, C464.2, C465.2, L19.2, R204.1, TP25.1, U18.9 (VCC14), U18.13 (VCC13), U53.2
VCC_1V8_S0: C215.1, R207.1, U18.58 (PLDO2)
VCC_1V8_S3: C177.2, C178.2, L8.2, R47.2, R56.2, R57.2, TP21.1, U18.25 (VOUT10)
VCC_1V8_S3_PLDO6: C197.2, R48.2, U18.20 (VCCIO)
VCC_2V0_PLDO_S3: C174.2, C175.2, C203.2, L4.2, TP32.1, U18.41 (VOUT7), U18.59 (VCC11)
VCC_3V3_S0: C466.2, TP24.1, U46.1 (VOUT)
VCC_3V3_S3: C180.2, C181.2, C467.2, L9.2, R100.1, U18.5 (VOUT8), U46.5 (VIN)
VDD2_DDR_S3: C188.2, C189.2, C190.2, C191.2, L11.2, R52.2, TP17.1, U18.30 (VOUT6)
VDDA_0V75_S0: C208.2, U18.11 (NLDO3)
VDDA_0V85_S0: C207.2, U18.10 (NLDO4)
VDDA_1V2_S0: C214.1, U18.57 (PLDO3)
VDDA_DDR_PLL_S0: C209.2, U18.12 (NLDO2)
VDDQ_DDR_S0: C183.2, C184.2, C185.2, C186.2, L10.2, R50.2, TP16.1, U18.67 (VOUT9)
VDD_0V75_S0: C211.2, U18.8 (NLDO5)
VDD_0V75_S3: C210.2, U18.14 (NLDO1)
VDD_CPU_BIG0_S0: C457.2, L1.2, R99.1, R99.2, TP22.1, U2.A4 (VOUT), U4.2, U7.2, U33.2, U34.2, U35.2
VDD_CPU_BIG1_MEM_S0: L20.2, U55.2
VDD_CPU_BIG1_S0: C461.2, L18.2, L20.1, R202.1, R202.2, TP23.1, U47.2, U48.2, U49.2, U50.2, U51.2, U54.A4 (VOUT)
VDD_CPU_LIT_S0: C156.1, C156.2, C157.2, C158.2, C159.2, C160.2, L5.2, R44.1, R44.2, TP29.1, U18.37 (VOUT2)
VDD_DDR_S0: C193.2, C194.2, C195.2, C196.1, C196.2, L12.2, R55.1, R55.2, TP27.1, U18.46 (VOUT5)
VDD_GPU_S0: C150.1, C150.2, C151.2, C152.2, C153.2, C154.2, L3.2, R43.1, R43.2, TP28.1, U18.49 (VOUT1)
VDD_LOG_S0: C162.1, C162.2, C163.2, C164.2, C165.2, C166.2, L6.2, R45.1, R45.2, TP30.1, U18.56 (VOUT3)
VDD_NPU_S0: C458.2, C459.2, C460.2, L2.2, R201.1, R201.2, TP26.1, U40.A4 (VOUT), U43.2, U44.2, U45.2
VDD_VDENC_S0: C168.1, C168.2, C169.2, C170.2, C171.2, C172.2, L7.2, R46.1, R46.2, TP31.1, U18.24 (VOUT4)

Notes on the sheet:
4A MAX 0.95V
ALTERNATIVE PART FOR 0.47uH IND C45958646
N/A SGM2576 FOR USB HUB
LPDDR4/4x=1.1V
VCC_1V1_NLDO_S3
SoC I/O Domains
Default:0.85V Low frequency: 0.85V-->0.75V
Feedback from RK3588
Default:1.8V Default:1.8V Default:1.2V Default:3.3V Default:0.75V Default:3.3V Default:0.85V; Low frequency:0.85V-->0.75V Default:0.75V Default:0.85V Default:0.75V
Can change to 0201
1.1V 1.5A MAX
check resistor dividor values
VDD_NPU
LPDDR4/4x=0.6V
VDD_CPU_BIG1
Level Shifters
4A MAX 0.90V
HDMI TX Logic & Pull-ups
