CXD8/CXD-ROUTER/Sch/PMU_CLOCK-7.kicad_sch

## KiCad design Sch/PMU_CLOCK-7.kicad_sch (2026-08-12)

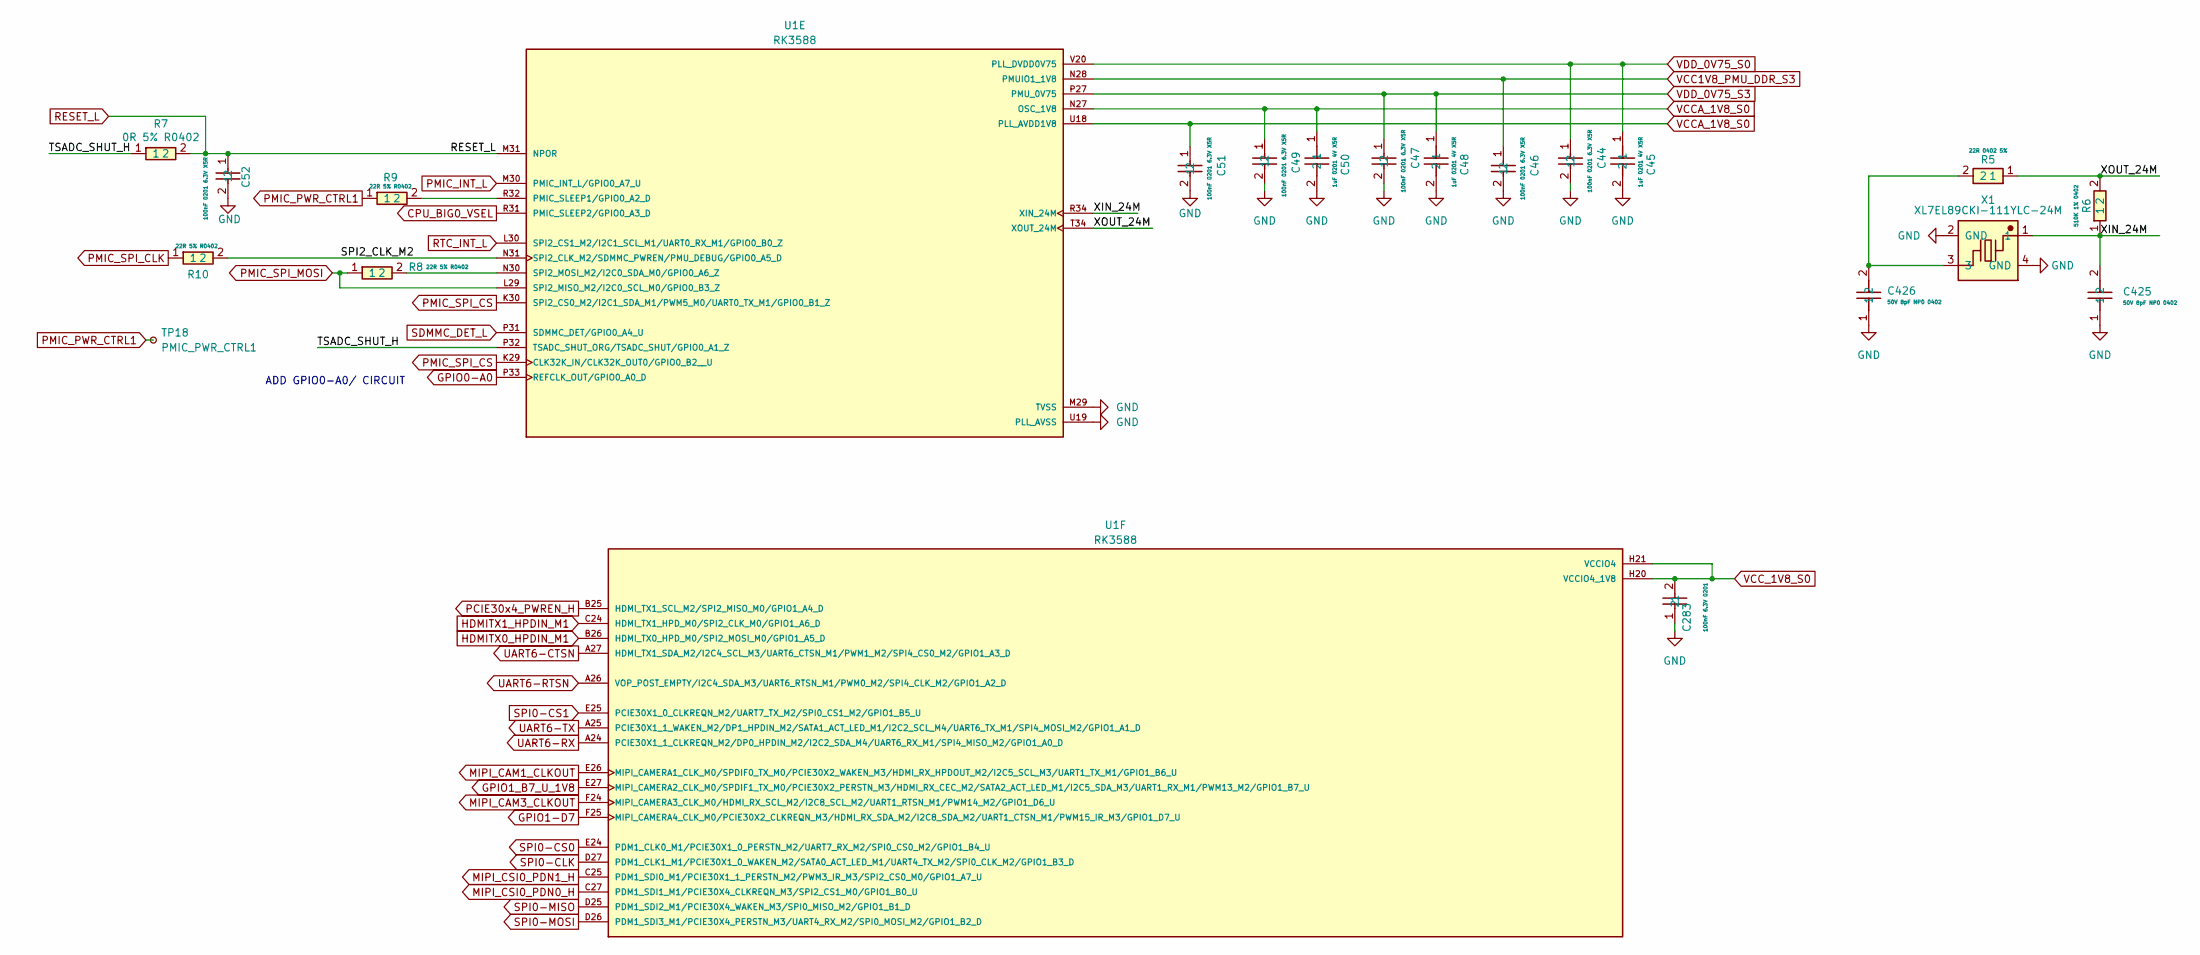
[picture p51: schematic PMU_CLOCK-7.kicad_sch]

Parts:
C44, C46, C47, C49, C51, C52: 100nF 0201 6.3V X5R; RC0201FR-0749R9L; Manufacturer Part CC0201KRX5R5BB104; LCSC C190187
C45, C48, C50: 1uF 0201 4V X5R; RC0201FR-0749R9L; Manufacturer Part GRM033C80G105MEA2D; LCSC C161455
C283: 100nF 6.3V 0201; RC0201FR-0749R9L; Manufacturer Part CC0201KRX5R5BB104; LCSC C190187
C425, C426: 50V 8pF NP0 0402; RC0402FR-071KL; Manufacturer Part CC0402BRNPO9BN8R0; LCSC C281765
R5: 22R 0402 5%; CRCW040222R0JNED; Manufacturer Part CRCW040222R0JNED; LCSC C482107
R6: 510K 1% 0402; RC0402FR-07510KL; Manufacturer Part RC0402FR-07510KL; LCSC C137961
R7: 0R 5% R0402; RC0402JR-070RL; Manufacturer Part RC0402JR-070RL; LCSC C60485
R8, R9, R10: 22R 5% R0402; RC0402JR-0722RL; Manufacturer Part RC0402JR-0722RL; LCSC C93929
TP18: PMIC_PWR_CTRL1; TestPoint_Pad_1.0x1.0mm
U1: RK3588; BGA1088C65P34X34_2300X2300X204N; PARTREV 1.0
X1: XL7EL89CKI-111YLC-24M; Manufacturer Part XL7EL89CKI-111YLC-24M; LCSC C2965580

Connections:
CPU_BIG0_VSEL: U1.R31 (PMIC_SLEEP2/GPIO0_A3_D)
GND: C44.2, C45.2, C46.2, C47.2, C48.2, C49.2, C50.2, C51.2, C52.2, C283.1, C425.1, C426.1, U1.M29 (TVSS), U1.U19 (PLL_AVSS), X1.2 (GND), X1.4 (GND)
GPIO0-A0: U1.P33 (REFCLK_OUT/GPIO0_A0_D)
GPIO1-D7: U1.F25 (MIPI_CAMERA4_CLK_M0/PCIE30X2_CLKREQN_M3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)
GPIO1_B7_U_1V8: U1.E27 (MIPI_CAMERA2_CLK_M0/SPDIF1_TX_M0/PCIE30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)
HDMITX0_HPDIN_M1: U1.B26 (HDMI_TX0_HPD_M0/SPI2_MOSI_M0/GPIO1_A5_D)
HDMITX1_HPDIN_M1: U1.C24 (HDMI_TX1_HPD_M0/SPI2_CLK_M0/GPIO1_A6_D)
MIPI_CAM1_CLKOUT: U1.E26 (MIPI_CAMERA1_CLK_M0/SPDIF0_TX_M0/PCIE30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)
MIPI_CAM3_CLKOUT: U1.F24 (MIPI_CAMERA3_CLK_M0/HDMI_RX_SCL_M2/I2C8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)
MIPI_CSI0_PDN0_H: U1.C27 (PDM1_SDI1_M1/PCIE30X4_CLKREQN_M3/SPI2_C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)
MIPI_CSI0_PDN1_H: U1.C25 (PDM1_SDI0_M1/PCIE30X1_1_PERSTN_M2/PWM3_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)
unnamed: C426.2, R5.2, X1.3
unnamed: R8.2, U1.N30 (SPI2_MOSI_M2/I2C0_SDA_M0/GPIO0_A6_Z)
unnamed: R9.2, U1.R32 (PMIC_SLEEP1/GPIO0_A2_D)
PCIE30x4_PWREN_H: U1.B25 (HDMI_TX1_SCL_M2/SPI2_MISO_M0/GPIO1_A4_D)
PMIC_INT_L: U1.M30 (PMIC_INT_L/GPIO0_A7_U)
PMIC_PWR_CTRL1: R9.1, TP18.1
PMIC_SPI_CLK: R10.1
PMIC_SPI_CS: U1.K29 (CLK32K_IN/CLK32K_OUT0/GPIO0_B2__U), U1.K30 (SPI2_CS0_M2/I2C1_SDA_M1/PWM5_M0/UART0_T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)
PMIC_SPI_MOSI: R8.1, U1.L29 (SPI2_MISO_M2/I2C0_SCL_M0/GPIO0_B3_Z)
RESET_L: C52.1, R7.2, U1.M31 (NPOR)
RTC_INT_L: U1.L30 (SPI2_CS1_M2/I2C1_SCL_M1/UART0_RX_M1/GPI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)
SDMMC_DET_L: U1.P31 (SDMMC_DET/GPIO0_A4_U)
SPI0-CLK: U1.D27 (PDM1_CLK1_M1/PCIE30X1_0_WAKEN_M2/SATA0_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)
SPI0-CS0: U1.E24 (PDM1_CLK0_M1/PCIE30X1_0_PERSTN_M2/UART7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)
SPI0-CS1: U1.E25 (PCIE30X1_0_CLKREQN_M2/UART7_TX_M2/SPI0_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)
SPI0-MISO: U1.D25 (PDM1_SDI2_M1/PCIE30X4_WAKEN_M3/SPI0_MIS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)
SPI0-MOSI: U1.D26 (PDM1_SDI3_M1/PCIE30X4_PERSTN_M3/UART4_R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)
SPI2_CLK_M2: R10.2, U1.N31 (SPI2_CLK_M2/SDMMC_PWREN/PMU_DEBUG/GPIO0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)
TSADC_SHUT_H: R7.1, U1.P32 (TSADC_SHUT_ORG/TSADC_SHUT/GPIO0_A1_Z)
UART6-CTSN: U1.A27 (HDMI_TX1_SDA_M2/I2C4_SCL_M3/UART6_CTSN_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)
UART6-RTSN: U1.A26 (VOP_POST_EMPTY/I2C4_SDA_M3/UART6_RTSN_M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)
UART6-RX: U1.A24 (PCIE30X1_1_CLKREQN_M2/DP0_HPDIN_M2/I2C2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)
UART6-TX: U1.A25 (PCIE30X1_1_WAKEN_M2/DP1_HPDIN_M2/SATA1_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)
VCC1V8_PMU_DDR_S3: C46.1, U1.N28 (PMUIO1_1V8)
VCCA_1V8_S0: C49.1, C50.1, C51.1, U1.N27 (OSC_1V8), U1.U18 (PLL_AVDD1V8)
VCC_1V8_S0: C283.2, U1.H20 (VCCIO4_1V8), U1.H21 (VCCIO4)
VDD_0V75_S0: C44.1, C45.1, U1.V20 (PLL_DVDD0V75)
VDD_0V75_S3: C47.1, C48.1, U1.P27 (PMU_0V75)
XIN_24M: C425.2, R6.1, U1.R34 (XIN_24M), X1.1
XOUT_24M: R5.1, R6.2, U1.T34 (XOUT_24M)

Notes on the sheet:
ADD GPIO0-A0/ CIRCUIT
