CXD8/CXD-ROUTER/Sch/RTC-16.kicad_sch

## KiCad design Sch/RTC-16.kicad_sch (2026-08-12)

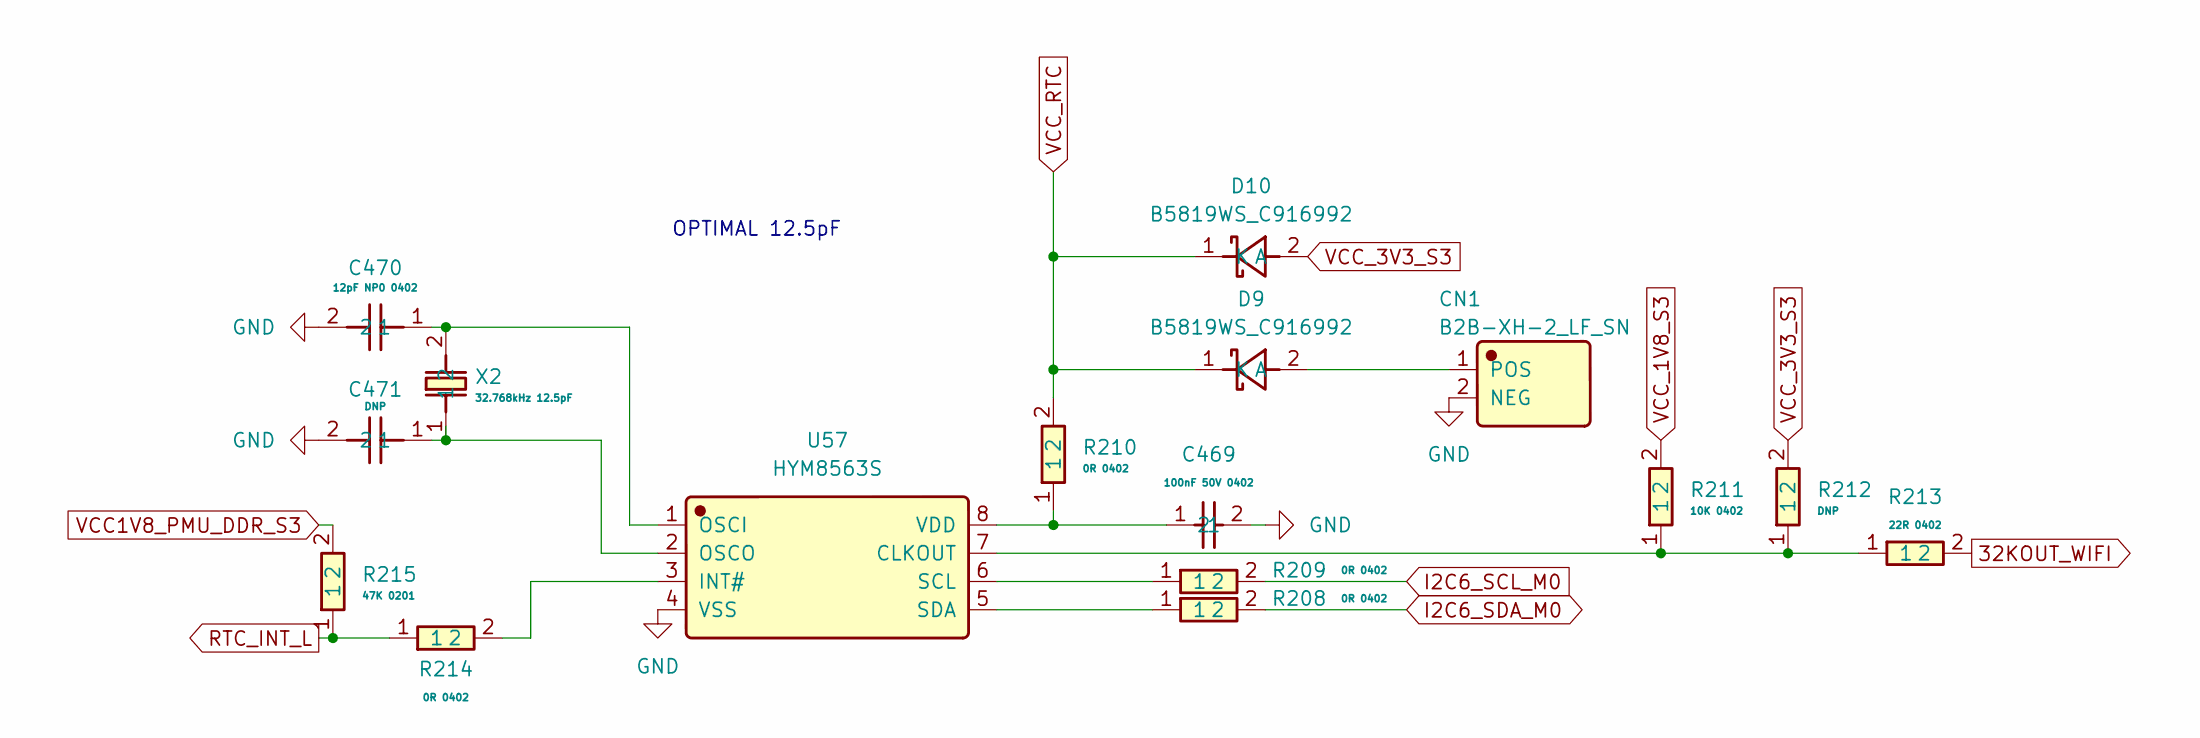
[picture p52: schematic RTC-16.kicad_sch]

Parts:
C469: 100nF 50V 0402; RC0402JR-070RL; Manufacturer Part CC0402KRX5R9BB104; LCSC C105882
C470: 12pF NP0 0402; RC0402FR-071KL; Manufacturer Part CC0402FRNPO9BN120; LCSC C326662
C471: DNP; RC0402FR-071KL; Manufacturer Part CC0402FRNPO9BN120; LCSC C326662
CN1: B2B-XH-2_LF_SN; Manufacturer Part B2B-XH-2(LF)(SN); LCSC C158014
D9, D10: B5819WS_C916992; Manufacturer Part B5819WS; LCSC C916992
R208, R209, R210, R214: 0R 0402; RC0402JR-070RL; Manufacturer Part RC0402JR-070RL; LCSC C60485
R211: 10K 0402; RC0402FR-0710KL; Manufacturer Part RC0402FR-0710KL; LCSC C60490
R212: DNP; RC0402JR-070RL; Manufacturer Part RC0402JR-070RL; LCSC C60485
R213: 22R 0402; RC0402JR-0722RL; Manufacturer Part RC0402JR-0722RL; LCSC C93929
R215: 47K 0201; RC0201FR-0747KL; Manufacturer Part RC0201FR-0747KL; LCSC C138139
U57: HYM8563S; Manufacturer Part HYM8563S; LCSC C155754
X2: 32.768kHz 12.5pF; SC-32S32_768kHz20PPM12_5pF; Manufacturer Part SC-32S32.768kHz20PPM12.5pF; LCSC C97606

Connections:
32KOUT_WIFI: R213.2
GND: C469.2, C470.2, C471.2, CN1.2 (NEG), U57.4 (VSS)
I2C6_SCL_M0: R209.2
I2C6_SDA_M0: R208.2
unnamed: C469.1, R210.1, U57.8 (VDD)
unnamed: C470.1, U57.1 (OSCI), X2.2
unnamed: C471.1, U57.2 (OSCO), X2.1
unnamed: CN1.1 (POS), D9.2 (A)
unnamed: R208.1, U57.5 (SDA)
unnamed: R209.1, U57.6 (SCL)
unnamed: R211.1, R212.1, R213.1, U57.7 (CLKOUT)
unnamed: R214.2, U57.3 (INT#)
RTC_INT_L: R214.1, R215.1
VCC1V8_PMU_DDR_S3: R215.2
VCC_1V8_S3: R211.2
VCC_3V3_S3: D10.2 (A), R212.2
VCC_RTC: D9.1 (K), D10.1 (K), R210.2

Notes on the sheet:
OPTIMAL 12.5pF
