CXD8/CXD-ROUTER/Sch/SPI_FLASH-17.kicad_sch

## KiCad design Sch/SPI_FLASH-17.kicad_sch (2026-08-12)

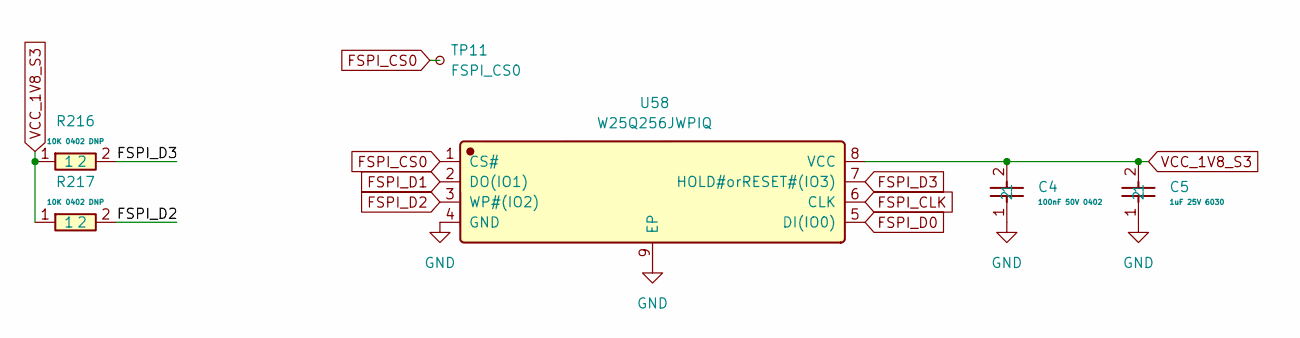
[picture p53: schematic SPI_FLASH-17.kicad_sch]

Parts:
C4: 100nF 50V 0402; RC0402JR-070RL; Manufacturer Part CC0402KRX5R9BB104; LCSC C105882
C5: 1uF 25V 6030; CL10B105KA8NNNC; Manufacturer Part CL10B105KA8NNNC; LCSC C29936
R216, R217: 10K 0402 DNP; RC0402FR-0710KL; Manufacturer Part RC0402FR-0710KL; LCSC C60490
TP11: FSPI_CS0; TestPoint_Pad_1.0x1.0mm
U58: W25Q256JWPIQ; Manufacturer Part W25Q256JWPIQ; LCSC C5362614

Connections:
FSPI_CLK: U58.6 (CLK)
FSPI_CS0: TP11.1, U58.1 (CS#)
FSPI_D0: U58.5 (DI(IO0))
FSPI_D1: U58.2 (DO(IO1))
FSPI_D2: R217.2, U58.3 (WP#(IO2))
FSPI_D3: R216.2, U58.7 (HOLD#orRESET#(IO3))
GND: C4.1, C5.1, U58.4 (GND), U58.9 (EP)
VCC_1V8_S3: C4.2, C5.2, R216.1, R217.1, U58.8 (VCC)
