CXD8/CXD-ROUTER/Sch/USB_INTERFACES-8.kicad_sch

## KiCad design Sch/USB_INTERFACES-8.kicad_sch (2026-08-12)

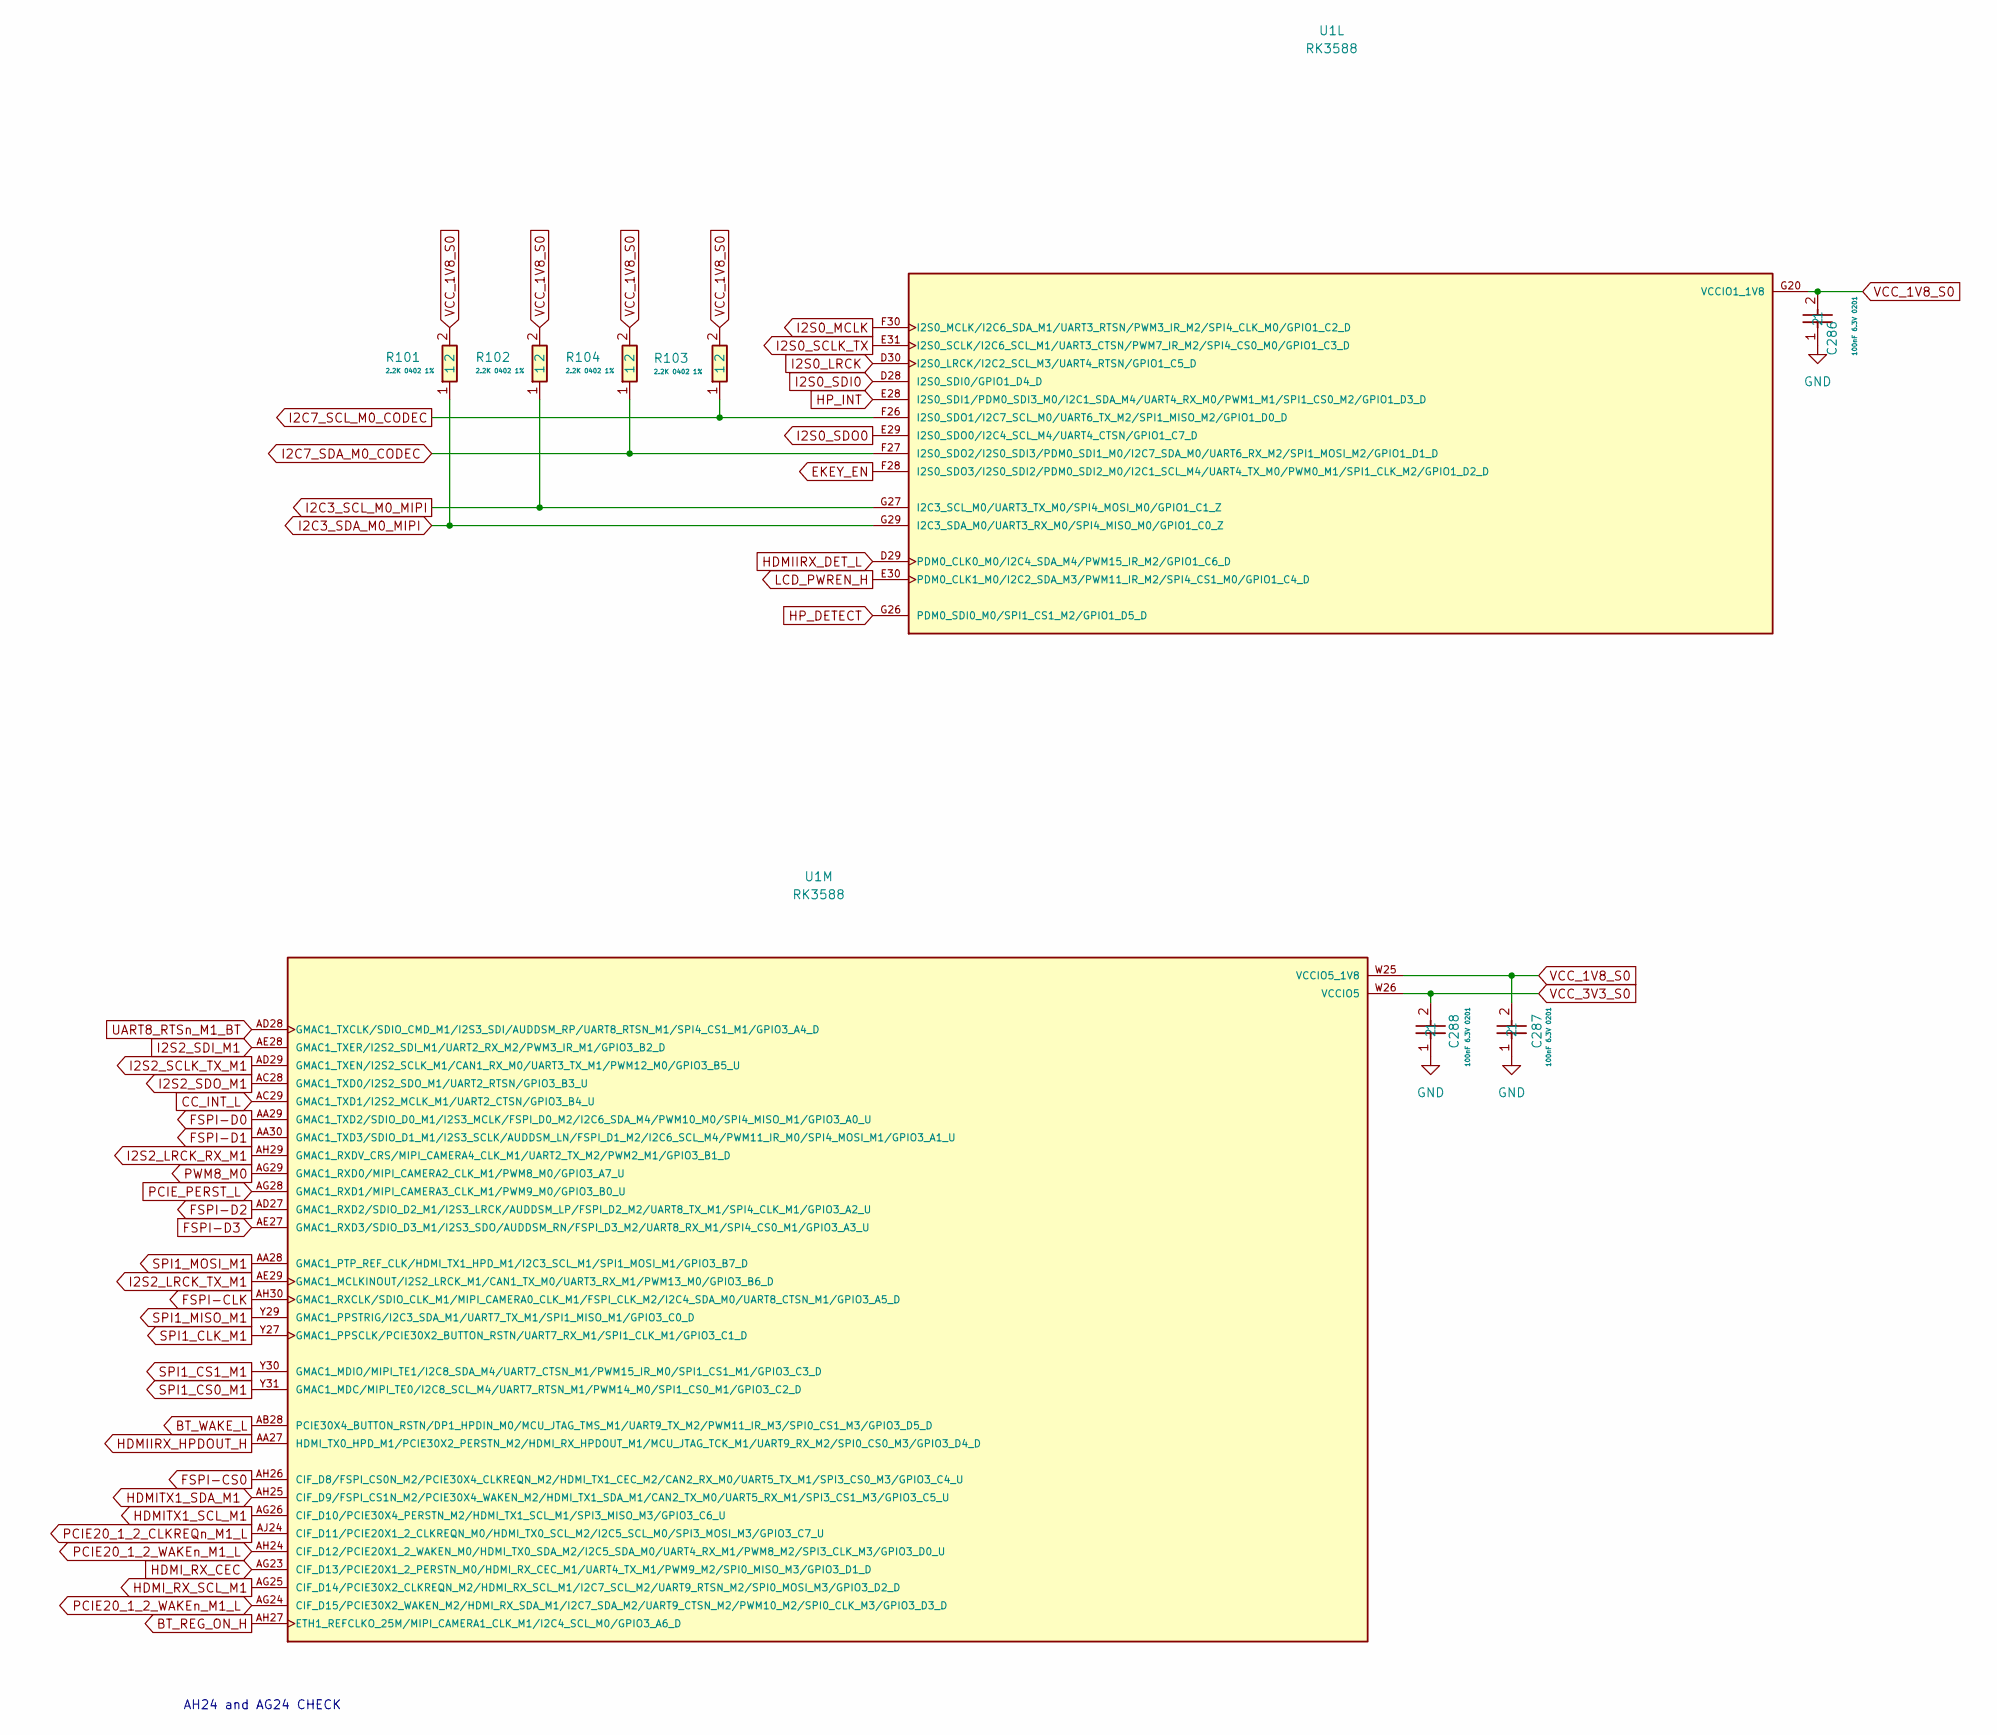
[picture p54: schematic USB_INTERFACES-8.kicad_sch]

Parts:
C286, C287, C288: 100nF 6.3V 0201; RC0201FR-0749R9L; Manufacturer Part CC0201KRX5R5BB104; LCSC C190187
R101, R102, R103, R104: 2.2K 0402 1%; RC0402FR-072K2L; Manufacturer Part RC0402FR-072K2L; LCSC C114762
U1: RK3588; BGA1088C65P34X34_2300X2300X204N; PARTREV 1.0

Connections:
BT_REG_ON_H: U1.AH27 (ETH1_REFCLKO_25M/MIPI_CAMERA1_CLK_M1/I2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)
BT_WAKE_L: U1.AB28 (PCIE30X4_BUTTON_RSTN/DP1_HPDIN_M0/MCU_J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)
CC_INT_L: U1.AC29 (GMAC1_TXD1/I2S2_MCLK_M1/UART2_CTSN/GPIO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)
EKEY_EN: U1.F28 (I2S0_SDO3/I2S0_SDI2/PDM0_SDI2_M0/I2C1_S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)
FSPI-CLK: U1.AH30 (GMAC1_RXCLK/SDIO_CLK_M1/MIPI_CAMERA0_CL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)
FSPI-CS0: U1.AH26 (CIF_D8/FSPI_CS0N_M2/PCIE30X4_CLKREQN_M2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)
FSPI-D0: U1.AA29 (GMAC1_TXD2/SDIO_D0_M1/I2S3_MCLK/FSPI_D0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)
FSPI-D1: U1.AA30 (GMAC1_TXD3/SDIO_D1_M1/I2S3_SCLK/AUDDSM_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)
FSPI-D2: U1.AD27 (GMAC1_RXD2/SDIO_D2_M1/I2S3_LRCK/AUDDSM_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)
FSPI-D3: U1.AE27 (GMAC1_RXD3/SDIO_D3_M1/I2S3_SDO/AUDDSM_R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)
GND: C286.1, C287.1, C288.1
HDMIIRX_DET_L: U1.D29 (PDM0_CLK0_M0/I2C4_SDA_M4/PWM15_IR_M2/GP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)
HDMIIRX_HPDOUT_H: U1.AA27 (HDMI_TX0_HPD_M1/PCIE30X2_PERSTN_M2/HDMI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)
HDMITX1_SCL_M1: U1.AG26 (CIF_D10/PCIE30X4_PERSTN_M2/HDMI_TX1_SCL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)
HDMITX1_SDA_M1: U1.AH25 (CIF_D9/FSPI_CS1N_M2/PCIE30X4_WAKEN_M2/H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)
HDMI_RX_CEC: U1.AG23 (CIF_D13/PCIE20X1_2_PERSTN_M0/HDMI_RX_CE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)
HDMI_RX_SCL_M1: U1.AG25 (CIF_D14/PCIE30X2_CLKREQN_M2/HDMI_RX_SCL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)
HP_DETECT: U1.G26 (PDM0_SDI0_M0/SPI1_CS1_M2/GPIO1_D5_D)
HP_INT: U1.E28 (I2S0_SDI1/PDM0_SDI3_M0/I2C1_SDA_M4/UART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)
I2C3_SCL_M0_MIPI: R102.1, U1.G27 (I2C3_SCL_M0/UART3_TX_M0/SPI4_MOSI_M0/GP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)
I2C3_SDA_M0_MIPI: R101.1, U1.G29 (I2C3_SDA_M0/UART3_RX_M0/SPI4_MISO_M0/GP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)
I2C7_SCL_M0_CODEC: R103.1, U1.F26 (I2S0_SDO1/I2C7_SCL_M0/UART6_TX_M2/SPI1_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)
I2C7_SDA_M0_CODEC: R104.1, U1.F27 (I2S0_SDO2/I2S0_SDI3/PDM0_SDI1_M0/I2C7_S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)
I2S0_LRCK: U1.D30 (I2S0_LRCK/I2C2_SCL_M3/UART4_RTSN/GPIO1_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)
I2S0_MCLK: U1.F30 (I2S0_MCLK/I2C6_SDA_M1/UART3_RTSN/PWM3_I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)
I2S0_SCLK_TX: U1.E31 (I2S0_SCLK/I2C6_SCL_M1/UART3_CTSN/PWM7_I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)
I2S0_SDI0: U1.D28 (I2S0_SDI0/GPIO1_D4_D)
I2S0_SDO0: U1.E29 (I2S0_SDO0/I2C4_SCL_M4/UART4_CTSN/GPIO1_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)
I2S2_LRCK_RX_M1: U1.AH29 (GMAC1_RXDV_CRS/MIPI_CAMERA4_CLK_M1/UART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)
I2S2_LRCK_TX_M1: U1.AE29 (GMAC1_MCLKINOUT/I2S2_LRCK_M1/CAN1_TX_M0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)
I2S2_SCLK_TX_M1: U1.AD29 (GMAC1_TXEN/I2S2_SCLK_M1/CAN1_RX_M0/UART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)
I2S2_SDI_M1: U1.AE28 (GMAC1_TXER/I2S2_SDI_M1/UART2_RX_M2/PWM3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)
I2S2_SDO_M1: U1.AC28 (GMAC1_TXD0/I2S2_SDO_M1/UART2_RTSN/GPIO3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)
LCD_PWREN_H: U1.E30 (PDM0_CLK1_M0/I2C2_SDA_M3/PWM11_IR_M2/SP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)
PCIE20_1_2_CLKREQn_M1_L: U1.AJ24 (CIF_D11/PCIE20X1_2_CLKREQN_M0/HDMI_TX0_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)
PCIE20_1_2_WAKEn_M1_L: U1.AG24 (CIF_D15/PCIE30X2_WAKEN_M2/HDMI_RX_SDA_M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), U1.AH24 (CIF_D12/PCIE20X1_2_WAKEN_M0/HDMI_TX0_SD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)
PCIE_PERST_L: U1.AG28 (GMAC1_RXD1/MIPI_CAMERA3_CLK_M1/PWM9_M0/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)
PWM8_M0: U1.AG29 (GMAC1_RXD0/MIPI_CAMERA2_CLK_M1/PWM8_M0/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)
SPI1_CLK_M1: U1.Y27 (GMAC1_PPSCLK/PCIE30X2_BUTTON_RSTN/UART7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)
SPI1_CS0_M1: U1.Y31 (GMAC1_MDC/MIPI_TE0/I2C8_SCL_M4/UART7_RT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)
SPI1_CS1_M1: U1.Y30 (GMAC1_MDIO/MIPI_TE1/I2C8_SDA_M4/UART7_C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)
SPI1_MISO_M1: U1.Y29 (GMAC1_PPSTRIG/I2C3_SDA_M1/UART7_TX_M1/S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)
SPI1_MOSI_M1: U1.AA28 (GMAC1_PTP_REF_CLK/HDMI_TX1_HPD_M1/I2C3_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)
UART8_RTSn_M1_BT: U1.AD28 (GMAC1_TXCLK/SDIO_CMD_M1/I2S3_SDI/AUDDSM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)
VCC_1V8_S0: C286.2, C287.2, R101.2, R102.2, R103.2, R104.2, U1.G20 (VCCIO1_1V8), U1.W25 (VCCIO5_1V8)
VCC_3V3_S0: C288.2, U1.W26 (VCCIO5)

Notes on the sheet:
AH24 and AG24 CHECK
