CXD8/CXD-ROUTER/Sch/VVCIO-10.kicad_sch

## KiCad design Sch/VVCIO-10.kicad_sch (2026-08-12)

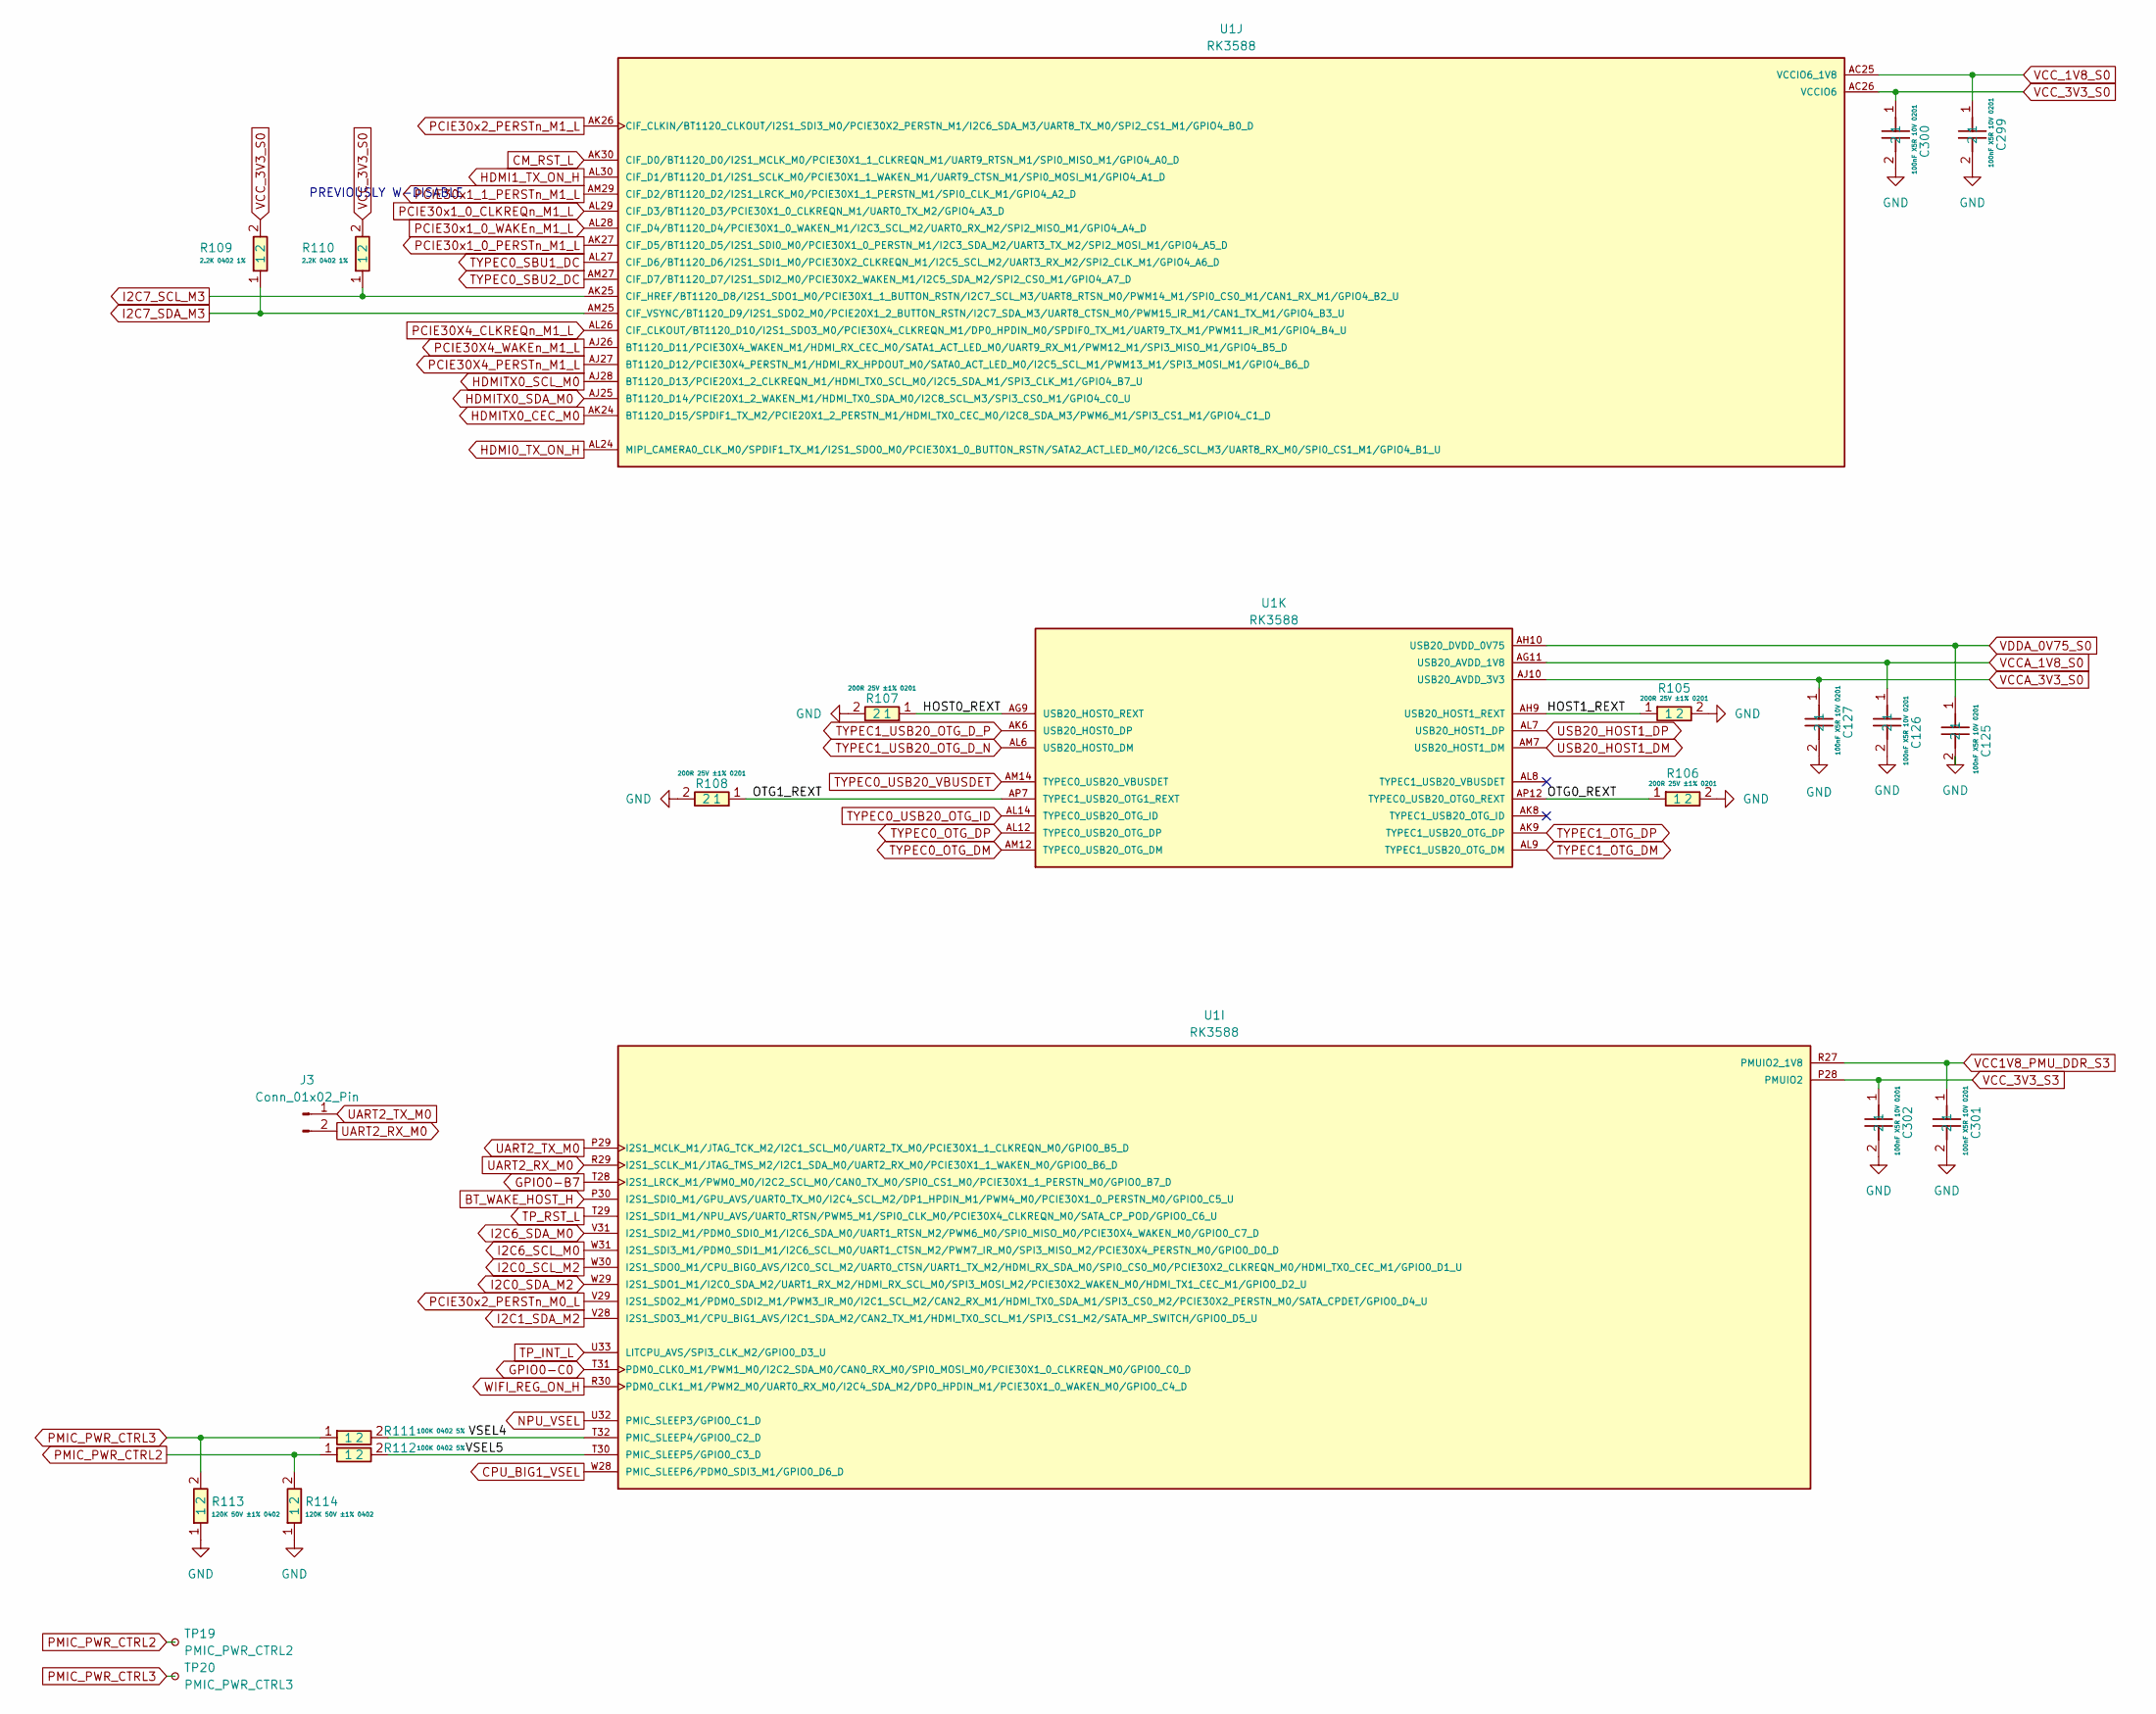
[picture p55: schematic VVCIO-10.kicad_sch]

Parts:
C125, C126, C127, C299, C300, C301, C302: 100nF X5R 10V 0201; CL03A104KP3NNNC; Manufacturer Part CL03A104KP3NNNC; LCSC C49062
J3: Conn_01x02_Pin; PinHeader_1x02_P2.54mm_Vertical
R105, R106, R107, R108: 200R 25V ±1% 0201; RC0201FR-07200RL; Manufacturer Part RC0201FR-07200RL; LCSC C274337
R109, R110: 2.2K 0402 1%; RC0402FR-072K2L; Manufacturer Part RC0402FR-072K2L; LCSC C114762
R111, R112: 100K 0402 5%; RC0402JR-07100KL; Manufacturer Part RC0402JR-07100KL; LCSC C106234
R113, R114: 120K 50V ±1% 0402; RC0402FR-07120KL; Manufacturer Part RC0402FR-07120KL; LCSC C93945
TP19: PMIC_PWR_CTRL2; TestPoint_Pad_1.0x1.0mm
TP20: PMIC_PWR_CTRL3; TestPoint_Pad_1.0x1.0mm
U1: RK3588; BGA1088C65P34X34_2300X2300X204N; PARTREV 1.0

Connections:
BT_WAKE_HOST_H: U1.P30 (I2S1_SDI0_M1/GPU_AVS/UART0_TX_M0/I2C4_S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)
CM_RST_L: U1.AK30 (CIF_D0/BT1120_D0/I2S1_MCLK_M0/PCIE30X1_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)
CPU_BIG1_VSEL: U1.W28 (PMIC_SLEEP6/PDM0_SDI3_M1/GPIO0_D6_D)
GND: C125.2, C126.2, C127.2, C299.2, C300.2, C301.2, C302.2, R105.2, R106.2, R107.2, R108.2, R113.1, R114.1
GPIO0-B7: U1.T28 (I2S1_LRCK_M1/PWM0_M0/I2C2_SCL_M0/CAN0_T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)
GPIO0-C0: U1.T31 (PDM0_CLK0_M1/PWM1_M0/I2C2_SDA_M0/CAN0_R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)
HDMI0_TX_ON_H: U1.AL24 (MIPI_CAMERA0_CLK_M0/SPDIF1_TX_M1/I2S1_S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)
HDMI1_TX_ON_H: U1.AL30 (CIF_D1/BT1120_D1/I2S1_SCLK_M0/PCIE30X1_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)
HDMITX0_CEC_M0: U1.AK24 (BT1120_D15/SPDIF1_TX_M2/PCIE20X1_2_PERS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)
HDMITX0_SCL_M0: U1.AJ28 (BT1120_D13/PCIE20X1_2_CLKREQN_M1/HDMI_T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)
HDMITX0_SDA_M0: U1.AJ25 (BT1120_D14/PCIE20X1_2_WAKEN_M1/HDMI_TX0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)
HOST0_REXT: R107.1, U1.AG9 (USB20_HOST0_REXT)
HOST1_REXT: R105.1, U1.AH9 (USB20_HOST1_REXT)
I2C0_SCL_M2: U1.W30 (I2S1_SDO0_M1/CPU_BIG0_AVS/I2C0_SCL_M2/U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)
I2C0_SDA_M2: U1.W29 (I2S1_SDO1_M1/I2C0_SDA_M2/UART1_RX_M2/HD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)
I2C1_SDA_M2: U1.V28 (I2S1_SDO3_M1/CPU_BIG1_AVS/I2C1_SDA_M2/C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)
I2C6_SCL_M0: U1.W31 (I2S1_SDI3_M1/PDM0_SDI1_M1/I2C6_SCL_M0/U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)
I2C6_SDA_M0: U1.V31 (I2S1_SDI2_M1/PDM0_SDI0_M1/I2C6_SDA_M0/U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)
I2C7_SCL_M3: R110.1, U1.AK25 (CIF_HREF/BT1120_D8/I2S1_SDO1_M0/PCIE30X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)
I2C7_SDA_M3: R109.1, U1.AM25 (CIF_VSYNC/BT1120_D9/I2S1_SDO2_M0/PCIE20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)
NPU_VSEL: U1.U32 (PMIC_SLEEP3/GPIO0_C1_D)
OTG0_REXT: R106.1, U1.AP12 (TYPEC0_USB20_OTG0_REXT)
OTG1_REXT: R108.1, U1.AP7 (TYPEC1_USB20_OTG1_REXT)
PCIE30X4_CLKREQn_M1_L: U1.AL26 (CIF_CLKOUT/BT1120_D10/I2S1_SDO3_M0/PCIE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)
PCIE30X4_PERSTn_M1_L: U1.AJ27 (BT1120_D12/PCIE30X4_PERSTN_M1/HDMI_RX_H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)
PCIE30X4_WAKEn_M1_L: U1.AJ26 (BT1120_D11/PCIE30X4_WAKEN_M1/HDMI_RX_CE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)
PCIE30x1_0_CLKREQn_M1_L: U1.AL29 (CIF_D3/BT1120_D3/PCIE30X1_0_CLKREQN_M1/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)
PCIE30x1_0_PERSTn_M1_L: U1.AK27 (CIF_D5/BT1120_D5/I2S1_SDI0_M0/PCIE30X1_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)
PCIE30x1_0_WAKEn_M1_L: U1.AL28 (CIF_D4/BT1120_D4/PCIE30X1_0_WAKEN_M1/I2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)
PCIE30x1_1_PERSTn_M1_L: U1.AM29 (CIF_D2/BT1120_D2/I2S1_LRCK_M0/PCIE30X1_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)
PCIE30x2_PERSTn_M0_L: U1.V29 (I2S1_SDO2_M1/PDM0_SDI2_M1/PWM3_IR_M0/I2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)
PCIE30x2_PERSTn_M1_L: U1.AK26 (CIF_CLKIN/BT1120_CLKOUT/I2S1_SDI3_M0/PC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)
PMIC_PWR_CTRL2: R112.1, R114.2, TP19.1
PMIC_PWR_CTRL3: R111.1, R113.2, TP20.1
TP_INT_L: U1.U33 (LITCPU_AVS/SPI3_CLK_M2/GPIO0_D3_U)
TP_RST_L: U1.T29 (I2S1_SDI1_M1/NPU_AVS/UART0_RTSN/PWM5_M1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)
TYPEC0_OTG_DM: U1.AM12 (TYPEC0_USB20_OTG_DM)
TYPEC0_OTG_DP: U1.AL12 (TYPEC0_USB20_OTG_DP)
TYPEC0_SBU1_DC: U1.AL27 (CIF_D6/BT1120_D6/I2S1_SDI1_M0/PCIE30X2_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)
TYPEC0_SBU2_DC: U1.AM27 (CIF_D7/BT1120_D7/I2S1_SDI2_M0/PCIE30X2_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)
TYPEC0_USB20_OTG_ID: U1.AL14 (TYPEC0_USB20_OTG_ID)
TYPEC0_USB20_VBUSDET: U1.AM14 (TYPEC0_USB20_VBUSDET)
TYPEC1_OTG_DM: U1.AL9 (TYPEC1_USB20_OTG_DM)
TYPEC1_OTG_DP: U1.AK9 (TYPEC1_USB20_OTG_DP)
TYPEC1_USB20_OTG_D_N: U1.AL6 (USB20_HOST0_DM)
TYPEC1_USB20_OTG_D_P: U1.AK6 (USB20_HOST0_DP)
UART2_RX_M0: J3.2, U1.R29 (I2S1_SCLK_M1/JTAG_TMS_M2/I2C1_SDA_M0/UA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)
UART2_TX_M0: J3.1, U1.P29 (I2S1_MCLK_M1/JTAG_TCK_M2/I2C1_SCL_M0/UA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)
USB20_HOST1_DM: U1.AM7 (USB20_HOST1_DM)
USB20_HOST1_DP: U1.AL7 (USB20_HOST1_DP)
VCC1V8_PMU_DDR_S3: C301.1, U1.R27 (PMUIO2_1V8)
VCCA_1V8_S0: C126.1, U1.AG11 (USB20_AVDD_1V8)
VCCA_3V3_S0: C127.1, U1.AJ10 (USB20_AVDD_3V3)
VCC_1V8_S0: C299.1, U1.AC25 (VCCIO6_1V8)
VCC_3V3_S0: C300.1, R109.2, R110.2, U1.AC26 (VCCIO6)
VCC_3V3_S3: C302.1, U1.P28 (PMUIO2)
VDDA_0V75_S0: C125.1, U1.AH10 (USB20_DVDD_0V75)
VSEL4: R111.2, U1.T32 (PMIC_SLEEP4/GPIO0_C2_D)
VSEL5: R112.2, U1.T30 (PMIC_SLEEP5/GPIO0_C3_D)
WIFI_REG_ON_H: U1.R30 (PDM0_CLK1_M1/PWM2_M0/UART0_RX_M0/I2C4_S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)

Notes on the sheet:
PREVIOUSLY W-DISABLE
